roberto314/Unicomp2/various/JTAG Chain.pdf

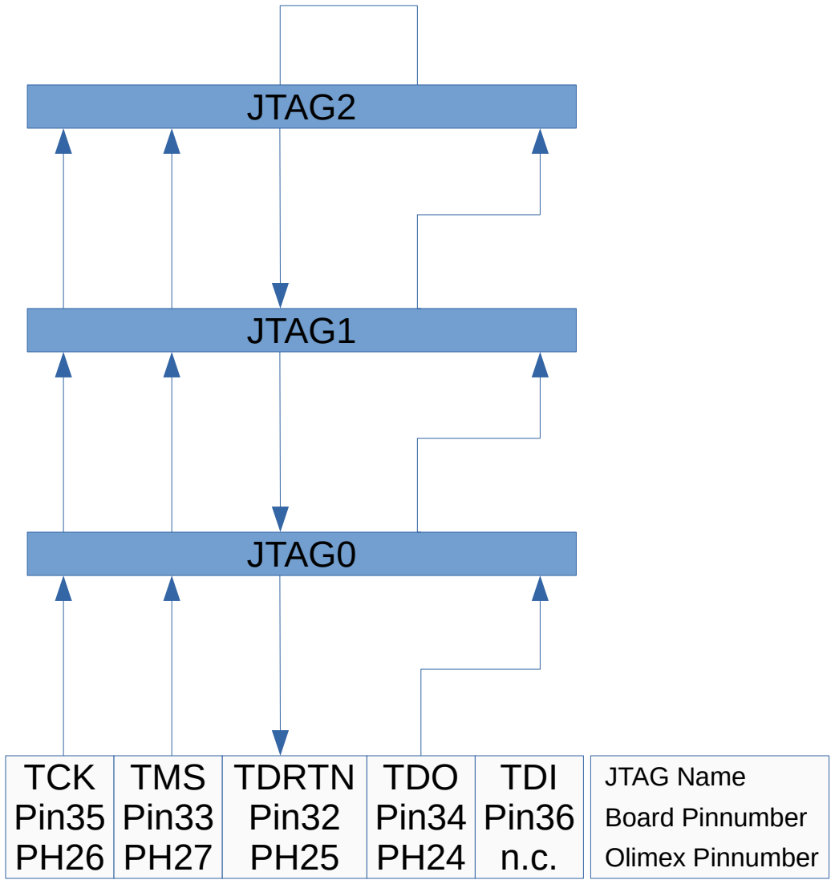
[picture p6: figure]
JTAG0; TCK Pin35 PH26; TMS Pin33 PH27; TDI Pin36 n.c.; TDO Pin34 PH24; TDRTN Pin32 PH25; JTAG1; JTAG2; JTAG Name Board Pinnumber Olimex Pinnumber

JTAG Chain and end connection
