roberto314/Unicomp2/computer/dream6800/Dream_Invaders/Dream_Invaders.pdf

### T EI FI EAM I TVVAtrTE FIEiI

COPYRIGHT 1980 | M.J. Bauer

Memory requ'irements :

Loading address:

Run address:

2K (0800)
0200 - 0700

0200 (Not C000)

Control s : Move gun-tumet LEFT: key 0, Move gun-turret RIGHT: key Lo
FIRE photon missile: key 3,
Game ends if | all four guns get zapped, or
an alien gets down to the bottom row (6th row).

Scoring:
10 points are scored for each alien exterminated. There are 24 aliens per round. Internal arithmetic is 8 bits, so maximum score is 250 x 10 = 2500, at which point the score (and ]evel of djfficulty) freezes; but you'1i never get to 2500 unless you're superhuman! Beyond 2500, the number of rounds played continues to be counted. The score is displayed after each completed round, and whenever the aliens score a turret hit. Also shown js the current round (on the left) and number of gun-turrets remaining.
Player gets a bonus of 2 new guns at the end of round 101

Mi scel I aneous :
Game speed increases as the game progresses; starting off fairly tame, but getting frantic towards round 8! The rate at whjch aliens tend to drop to a lower level also increases;, beware when one gets onto the 5th row! (Hint: Many events which appear to be random-are not, but in fact are more or less under the control of the player!)

The aliens also step up the number of missi'les they use, at round 3, and again at round 6. There are no shields, so you must rely on your skil1 at dodging and develop
a strategy to avoid being anihilated!
Game can be restarted by pressing any key (after 4 second delay).

Checks um:
A short Checksum Verify program is provided to check that your Invaders program 'loaded from tape without error. Key in and run this routine at 0700. It only takes a fraction of a second to run. Then use 'memory modify' to
examine location 00FF; jt should contain AA. If it does, there is a99.6% probabi'lity that your program loaded without emor.

DREAM INVADERS has been thoroughly debugged and tuned, and exhaustively tested (by eager Space invaders addicts) so as to ensure you many'long hours of enjoyment. If the program appears to be misbehaving on your systemo then either it did not load correctly (which can be checked, as above), or your

system has a hardware fault. Note: adjustment to the tape demoduiator trimpot may be necessary to effect a successful load.

(4, I or C) (5, 9 or D) (7, g or F)

(a)
(b)

## trl Ft EAM6sOO soFrvl/AFIE

CI{TCKSUM VERI FI ER
Titis litt1e program is used to check that d4ta in a given menory block (in chls case,0200 - 0700) has been correctly loaded. A1l it does js to add all the bytes together, without carry, and the B-bit result is stored in a certain RAM localion. namely 00FF. Thls result should be AA in the case of DREAM INVAIERS, trt i6
highly reconunended that you run rhe verifier after the firsL attempt at load'lng INVADERS. Note that the srarting address of the veri-fier is $0700 (not C000) ,
* CHECI{SUII VERIFY RBUTINEI (,7OC, | trRB | $0700
o70O CE O?OCI VI-RIFY I"DX | *$OzO{t
oloS 4F | CLR A
C'7O4 E6 {'O | VER1 LDA B X
0706 IB | AFA
a707 06 | INX
o70B 8C 0700 | CPX | *tO700
OTOB 2b F7 | BNE | VER1
Cr7ofr V7 Ff | STA A tlOoFF
o70F 7E C360 | JF1P *C360

LEVER AND PUSH-BUTTON CONTROLS
To avoid wear and tear on your keyboard, I recormend that you construcL a heavy-duty control-lever and fire-button assenbly on a lump of 4-by-21 The buttons are wired in parallel with key-switches (0), (1) and (3). They will not interf,ere with keypad operation because they are normally open. For ultra-reliabili-ty, you
could use rnicroswitehes.

A

V

ocK

Fm

W0 |DEN Et
l fBi-cFrFl

# Fre

eble
C HE,4 P
PUtH-gurroNt

NET|L ERAOKETS

WN'HE' PIVOT
( EMst)
CA N rNOL LEV ER 4 SSEfu TLY | ,tN PLu6. {2700)

2K RAM EXPANSION FOR TIJE DREAM-6800
Important Notes:
It is highly recomrnended to wire B x 10k pullup resistors from the data lines (00 - D7) to Vcc (+5V), on rhe DREAM board; (see diagram).

A 2.2k pullup resistor is required on R/W, as shornrn, since VMA is not used. REMOVE RAM CHIPS FROM TIIE DREAM BOARD; to be installed later in expander board..
Never remove or replace the e>cpander board with power appJ-ied.
GND and Vcc leads should be connected first on installation (before bus leads). Ground yourself and your work (via a lM resistor) to avoid static discharge damage. Construction Hints:
Fabricate the circuit on vero rDrp Boardf (No. zoo-21084E) or similar.
Use sockets for all ICs. Place O.luF ceramic bypass capaci-tors near the 2114s. Use two ribbon cables (4" to 6" long), terminated at each end with 16-pin DIL plugs ' to connect. the expander board to the DREAM board. These can be purchased already made up. The DIL plugs on the expander board end should be soldered in (i.e. not socketed) to ensure reliability and to save 2 sockets.

Take extra special precautions not to get Vcc and GND reversed! The use of a
polarized Z-pin plug and socket is highly recommended to avoid catastrophy.
Use fine hookup wire for interconnections on the expander board; 30 gauge 'Klmart wj-re-wrap wire is ideal. Cut wires about fu cn longer than the direct point-to- point distanee; youtll end up with a mess if they are too short or too long. Be eareful not to nick the wire when stripping insulation and avoid bending the wires at the joints too often. use solder sparingly; donrt make blobs!

The signat frE (rnemory Write Enable) is not available on the bus connectors, so it is necessary to sacrifice one that is. It so happens that IlQ is pretty useless,
so wer11 use pin-10 for FE. Cut the PCB track at pin L0 on the lower bus socket. wire a link from rc10 (74LSl0) pin-12(wT) ro rhe bus connecror pin-L0.

Testi ng
First, test your expanded system using tmemory modifyr. Try reading and writing a few locations at random. If the computer appears to be working at all, thatrs a very good sign! You should be able to deposit and exannine data from 0100 to 0800, but from 0800 to 2000 you should get 'FFt, indicating no RAIvI present.

If that works OK, you mi-ght like to try the memory check program in the CHIpOS manual, j.f you have one. This program can be improved to provi-de an audio bleep after each successful scan of the block under test; as foll-ows:-

O22C BD CzDF
022F 7E 0203
| JSR BLEEP JMP OVER
Note that DREAMBUG is required with the memory check" so that if a RAIvI fault occurs' a register dump will be displayed so you can figure out what went wrong!

Check the block starring at 0280, ending at 0800.
If you have a malfunction, carefully check over your wiring. With ICs removed, use a multimeter (on ohms x 1) to check for shorts and continuity. The RAM chips
can be tested in the DREAI'{ board, without the expander board connected.
Another useful test is to run the DREAIvI board (with its lK), with the expander board EMPTY (i:". all ICs, incl. 741s138, removed). If it doesnft work, you know for sure therers a wiring error somewhere!

Addendum:
The December '80 issue
Many of the above noLes

of E.A. contains details
will also be applicable

of a 4K RAM expander PCB design. to that, design.

6 F,lD
nlw

AOn(
frLA1 'A+

h5. ftb
h7
AS
A9
00

'at 4
D'A
93p9
9E
96n?
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
2.7.K

2K - +K RATh EXPAN9ION FOK THE DREAM - 58OO

2.7k

Iir (o+oo-oloo)

Resis+ors : 94W 5%
DioAes; 1Nt1*s or
7+ LS 1,38 | I,apacilors: pref. monolilhit (erami<,
nr.
log | 10 | 8 | 108

Vrc 6ND

;
A

:
:
0 t 1t+ L LL I
t----

D
FwE

Vcc 6Nt

;
:
A

211+

n

I
cs wE

V(c 6ilD

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
211+ D0--

Dr
DZ
D7

Vc< 6ND

;
:
A

4t'lL LLL I

[56 (oooo-o+oo)

vd< 6ND
ao
AOAt 4'
AZ
_q2 E
F43
E

L-..,*.--.-.,
Jj liEfrlw g0a8o | +5 Ct{} +12 -5'
,

id-A- o

-ol

| ------J
t,,*,,,-- JC3-
-,
| j.:-:;6::x: .ir,i., [fI r- I
| siil;i-.,i'; i ; I

### I",i,i'i

| | * I

tl

il
.rl

f

lm
1>< l"o{>32. iw

1oIt

;

I rrr
lL
I ltt l-lxI :-t

I
i
JY

## L{EErk'

(x ree )
I hot.tj

0
Ic5 | ICI+
H

trc6
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
## li ^t^^

I

<^>tl

ErDtrtolv5 T0 ,8Enm E0A8p
F06 Ex?nNstoN j gus socKETs
IIN' ?ALL.UP frESISTORS.

SU66ESTFD VENO LAYOUT i
8oT'r0M | ^ vrEW ! | r',\ V

L€AV€ frOON FOF FUTUEE
ExfnNstotv (e.9. p.r"A. ) .
cHEcK hllslN6 A6Att(5T ClRCotr !

6rp
0,Lr,P'
\76a o1 fi\e
6ND * (irH
Y" '.:Y;
iEEFr irr-,
vb .I*

## gg $EggHsEfi$EgaEaS$ $EgnEEgE $g$$3}$$$$3E $3

st*fr 8$rH gsil*f; fr $8R 8s s8H8S8S hHSSFilS*hSgf, H8 b 8HtflilHtafil3sSsf;$H8ftHsSSHEf;tHhfrh?HtHsHSflHf; co E F,F g gf t+ g!? h. gg €€ gJ s !.8 {! E l o sglr.{r rr, tr r(.r n. €rJ€x { rr o e a ir} rrr"t o o.(\ + s,{ EErs tr.O8j dtrsi [.J qt.{ 46{.j6f d,r AiUil dEdir. <i} 6t mn j stRh$3b*$ssi8s8s8H8bsst*8s8fHHk8Hs*sEil?s

## = e{t.g+gass€qNN${ o E0s roo,rjnr' dFdiric+8fl3t? ftn3Sflh8k$HSiHS*SSHSgt

S tagEES.Of{st! O€ rfr.O {

## :r a;dEEFrn{uooos'ot3U3B dSSnSgSSSSHtfr$fSH*fl?S

: RTbEEftT83HH3E8$tSEhEfiHSIgSKfKF*STSHEilRHf;
'F qg { h f t{qtP g g{-) g{ h r,.r I?a g g g FrF.q e € \ t €r.\ { tf rrr{ Nt.o br . r{ o :, {$ e r.rN s {rr E ou e{ NN E <x o 6 tr i6itft6 db ii Iii { of d Lj n,J tFl G i

## g 8HHhfi3*atH8S83iF8f;U88$8R:5fft8ilEftfrH38fl8H8

o H I s l'-l € t I € Q F t'.. { f r\ $ F LJ o H n { q gJ s E :r g u a g s tr | g} < !{ rr} s o. r.r o { o s < id m o 6 < E $ < {J 6 o q F.t l^t u fi d t\ ii m G Ci A E fi rq d ct fi O 6 5 Fr r. r'.

## th ft +*ft Ef, H8t$ sg 8H8 3ilrS*ff h8fr H85ft Sil8838Ufl H8

8 k h *8 fr t fr g f S E H * H 5d E E * h H b f HS I H8 3 H s S H I k b i9 R e

## Rgefi8s8H 3fr ES*i8+ilSSft 8H8drf; s8h*Eh88hF 88S8

8S$ES Hrts$ilRhh* SSh E 88S88rf8 SRlHSdEsFsk$fl f,
I g f* \ lg € !& I -t F E q A q tr { * $ l.f F { td g g $ { € O tfi t\ id r g r,. { { r\ u $ trl c.i o s < cr e.t tr rd <> e O o cr u rn -r $t -{ u ii 6 E fi d ; {,1 d ; t ii E ti 6 fr f, d it E - [

## tsdtsEstH?f, 3s* E$s sf;s8ffsgHrH8*ttH*$rili8fl il

il 8h lt $8 8h3 S 83 k 8r R8b 8S8 r hF t 8E 6 *8 tLiE 8FR f; 3t d

## s*3 8EE EbBSSSEh$ft 838:kf 33EB**h$*S8f; s8S3Hfr

I q g E I E x :r I E U !l el $ |o c' o. a H A € E O g tJ -r x € ct 8\ o. O { q c0 € o € { .{t
u <t (8 c| $ o (} o E] u co fl o o o € F{ s u c o ft t'. a s o o. o. ; Ft fiJ di o o r < 6 LI 6 6
o r,. u a r\ !q .8 g o r! !q o Ll gl E t\ trt o o + s N td *t o .o < f\ o fit rA o N rr c0 N Ll (t) .o 6 O e LJ E u} tl,l C* f'{ (J E O -t (J C.l O e 6 < ; c0 8,,t Cv li < 6 4 f n Fi fl { O t\| { + iF r\ {t d tr u (o ry I { l! irl Ll E 4 o -r S Q -r o r x cl r o t lrl { u s tq { |f} € \ Ll n {} € !t N El cf {} € -r o o O 3E O $ N S (} Ll O O < €} i S 6 + € O -{ f N fi O S { f.t g. \ { $ -r {l () lE E O cO { g lr. F $ t al Ol E f\ tO O € € .0 € O u) + +r -t € O o. -{ N trl .o tr. tr. LJ -r N & @ l& O -t (J o o a x !Qs ta c8 E r]l <Ef,{ tr. < 6 { f{ o o * € Lr c.t o o bJ (\ gi d fl} tr fi o { N o N 6 trt x
O E$ {! Fl g -r Ll\ q to { $ f{ A O { }\ € tf a0 P'rr. r\ { NN lr. O. € { {-t lr. €.0 tl NN S o !E x t]e lr.'JG nq :f u- m <L! N s trt 6 d < rrr * € rr ir< 6 u ct o h r d 6 o r,. 6d 6 { ij d', x I O I O I {l Clr € I\ lL { tL € lrl.O b 6 -rn E -t O O A -t € rr. U tJ E { $ A trt -t l,r. E Fl { o (J o t\| r|{ 0F E t t& o. !f ul t= N fl o rR L,t o. o\ € g { o E E0 fi |o (rt (q rI < ql E s ql i& E o
O Ll tr LL '.) € tJ € -{ € lL O O rr { E ct { O € Ll { O € U tf t O .o € € tt} € o' u) r\ O .{t m t\ r l\ E \ t s g* s o f1'| tl. s o fi U) o. t A o $' t s, o s. h ..8 { -r o c! o { o tfJ o o.. t c o ft O Q q.D L, trl'{I Fl .{l € < € l& t! {t m O g { u o. E0 C € fit O .o { O cl {f E r\ S trl € o d o € E
Ct <E E .{] cg s (} -r t\| rfi !O If $l O $ O cO < O $! <C O { t'" I U b A E rln Q r N O tJ Ll O < fJ d
trt n N E tt < E trl tlt tJ A O tf { € t/. .o E Go (\| € lL t\| lrt O { t\ l'} .a n O. q !f g rD < { N < O u {}. o € o u cB 4 o lr. E0 LJ a u o r\ 6 S O u s x r E o $' |lt E < { o *r { (1 < @ N b, o. 6 0 I F { t. Fl |n n { I I o € x e{ r E o o x o 0. i.l x L { s e,t N o o. € -{ E € € o o { < O'3 E { $'i'3 trt c,r s f.l o O o m s ft N + 6 rrt o rrj trl { N o o o tr,'5 o (s g" ld 6 + 6 o 6 ri { { q b S g g I CJ < lrl bf E H} Ll O \t € Ll Q -r < ttl { x O {f € u { N f c) € 0. O €l € Q -r o s < $.aE t\| r\ri ct Lru to ':} El l{ tl|{ trlo. < { It o € ltrq 4 tf N $t {o e.{ fil qf € {Q t&
x { I u'^{ \ u tr {! -{ I s O € t\ { -t o trt € \ o r\ ct € o o g. fit u o r\ .{t o s cl tf o. ti |n € lr. o -l a8'3 E s iE O O(t, O {J.0 N g* S S{}tS O &E (} Lt -r O Q|gl -r o.{ $'i.']1+ { fl} L{ ci
N n L. { € { { { € -t N € x -r € { m lrt O O I O 4 O Cl Cl € n. Ll € O fl {0 O trl x -0 r !O E (J O l\ tB < t1'| S tt* II. .3 O lr. < { O n & rf O $ -l x Q O E S $l (} F ,} e {} 6 O 4 -r o.' iJI O E g g O { € -r r} E '| S. bf € L. O tr m .o N U| lL {l € fr N -r rr O € fi E tdl ttt O Lt -{ -{ E .A Cl .\ tr| S 6 { & O L S E {} \ r\| h () A m 6 g N d tf <t O <t < .8 -r o E tr E {i O 6 € < o e* lii .s
ooqoQoooQ oQGoooooooooooo | ooooooooo | oooo000 o -r t\{ rrl tr $} .o r\ t8 o. <E rtr u {f ..d lr. o -r e{ m lf tr, € r\ fr s s H H H H h * -{ N fi tf n s r\ SS8888SS8SES888888888883ooooooooS SSt SSES

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
