roberto314/Unicomp2/6502_6802 Board v2/MC6800_MEMR_and_MEMW.png

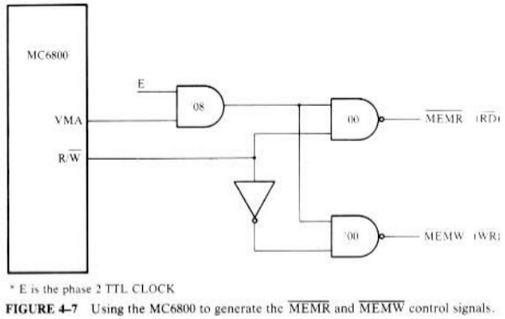
6502_6802 Board v2/MC6800_MEMR_and_MEMW.png
