roberto314/Unicomp2/computer/psion1/p1brochure.jpg

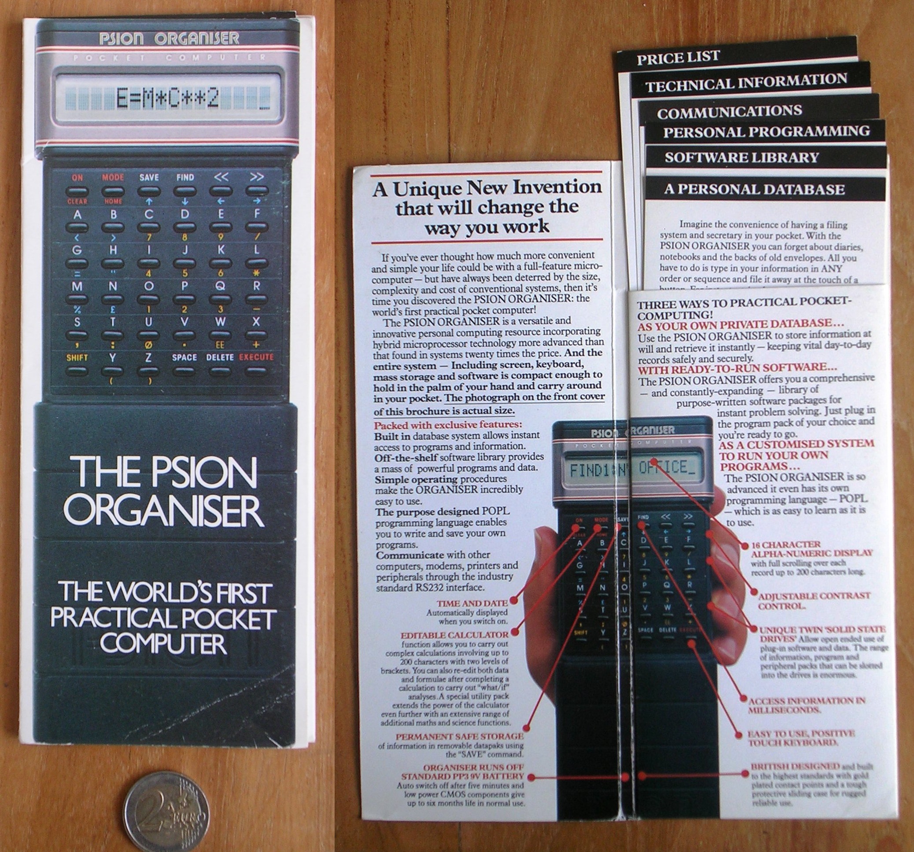
computer/psion1/p1brochure.jpg
