roberto314/Unicomp2/CPLD_board/ebay-board-EPM240.jpg

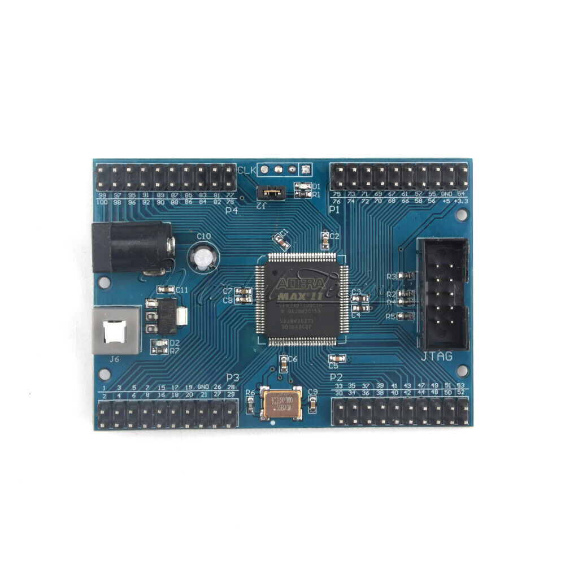
CPLD_board/ebay-board-EPM240.jpg
