roberto314/Unicomp2/Synertek KTM2/UC2_synertek_KTM2/UC2_synertek_KTM2.ods

Id | Designator | Footprint | Quantity | Designation | Supplier and ref
20 | U1 | TQFP-44_10x10mm_P0.8mm | 1 | XC9572VQ44
9 | U9,U3 | DIP-20_W7.62mm_LongPads | 2 | 74LS245
11 | U7,U10 | DIP-16_W7.62mm_LongPads | 2 | 74LS166
12 | U8,U12 | DIP-28_W15.24mm_LongPads | 2 | 27C64
18 | U2 | DIP-14_W7.62mm_LongPads | 1 | 74LS05
15 | U11,U6 | DIP-24_W15.24mm_LongPads | 2 | 6116
1 | U4 | SO-20_5.3x12.6mm_P1.27mm | 1 | 74ABT245
 |  | Sockets and Headers
2 | J8,J5 | PinHeader_1x09_P2.54mm_Vertical | 2 | Conn_01x09
3 | J1,J4,J2,J3 | PinSocket_2x20_P2.54mm_Vertical | 4 | BUS
14 | J6,J7 | PinHeader_1x08_P2.54mm_Vertical | 2 | Conn_01x08
19 | J9 | PinHeader_1x01_P2.54mm_Vertical | 1 | Conn_01x01
13 | J20 | RCA-Jack | 1 | Video
 |  | R and C and Q
4 | C5,C4,C6,C10,C1,C11,C2,C7,C3,C8,C9 | C_1206_3216Metric | 11 | 100n
5 | Q1 | TO-92_Inline | 1 | BC337
7 | R6,R1,R8 | R_1206_3216Metric_Pad1.30x1.75mm_HandSolder | 3 | 1k
8 | R17 | R_1206_3216Metric_Pad1.30x1.75mm_HandSolder | 1 | 150E
21 | R19 | R_1206_3216Metric_Pad1.30x1.75mm_HandSolder | 1 | 75E
22 | R18 | R_1206_3216Metric_Pad1.30x1.75mm_HandSolder | 1 | 680E
17 | R20,R3,R2 | R_1206_3216Metric_Pad1.30x1.75mm_HandSolder | 3 | 200E
6 | LS1 | MagneticBuzzer_Kingstate_KCG0601 | 1 | Speaker
