roberto314/Unicomp2/MultiParallel v2/schematic/MOS_MultiParallel_2/pdf/MOS_MultiParallel_2.pdf

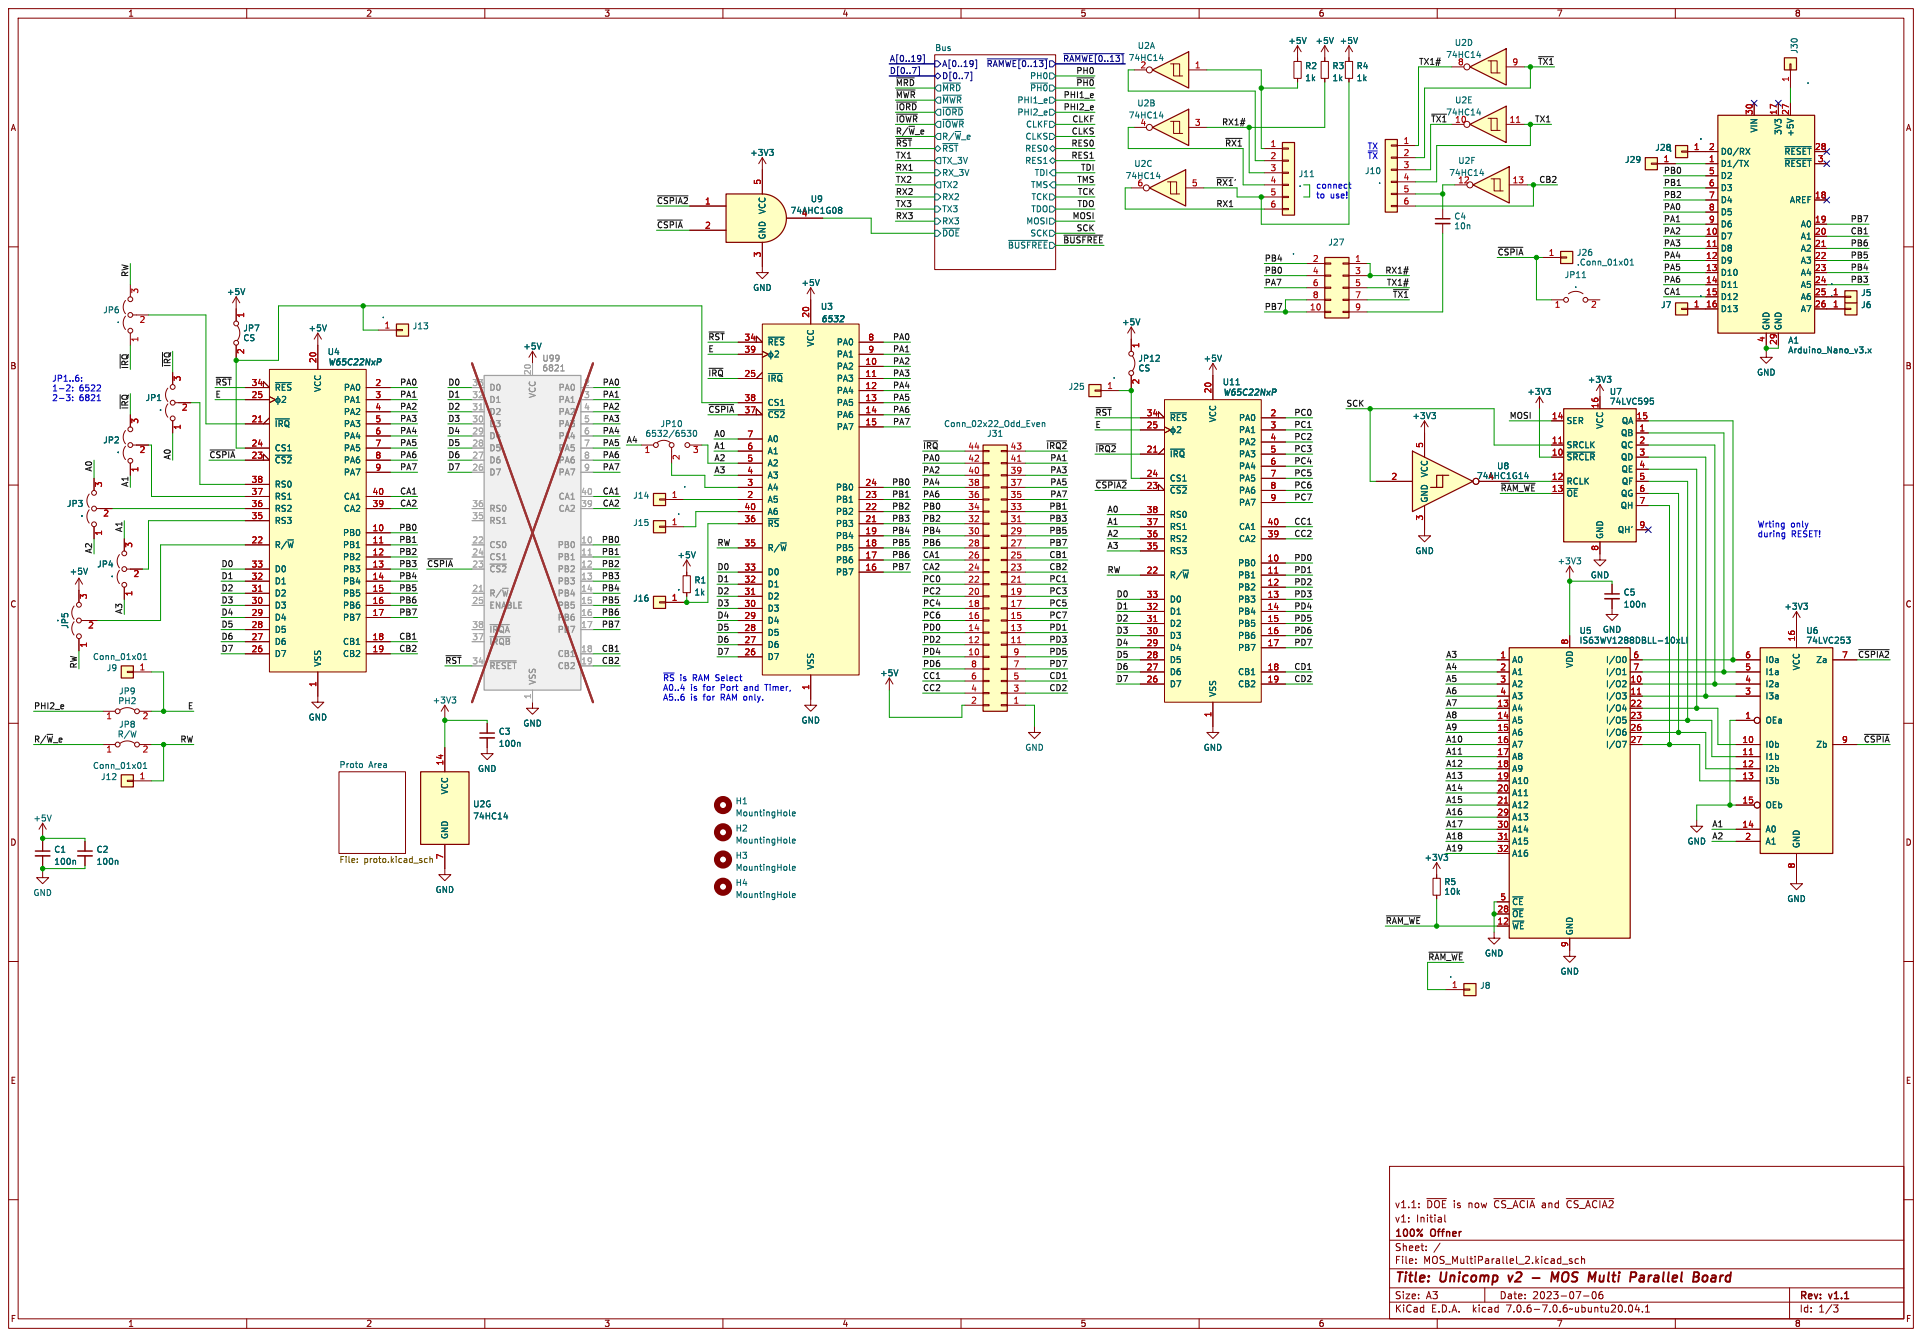
[picture p31: page 1]

1 PA2 10 PA3 11 PA4 12 PA5 13 PA6 14 PA7 15 PB7 16 PB6 17 PB5 18 PB4 19 A5 2 VCC 20 PB3 21 PB2 22 PB1 23 PB0 24 ~{IRQ} 25 D7 26 D6 27 D5 28 D4 29 A4 3 D3 30 D2 31 D1 32 D0 33 ~{RES} 34 R/~{W} 35 ~{RS} 36 ~{CS2} 37 CS1 38

7 GND GND GND GND

Proto Area File: proto.kicad_sch

Id: 1/3 Title: Unicomp v2 - MOS Multi Parallel Board

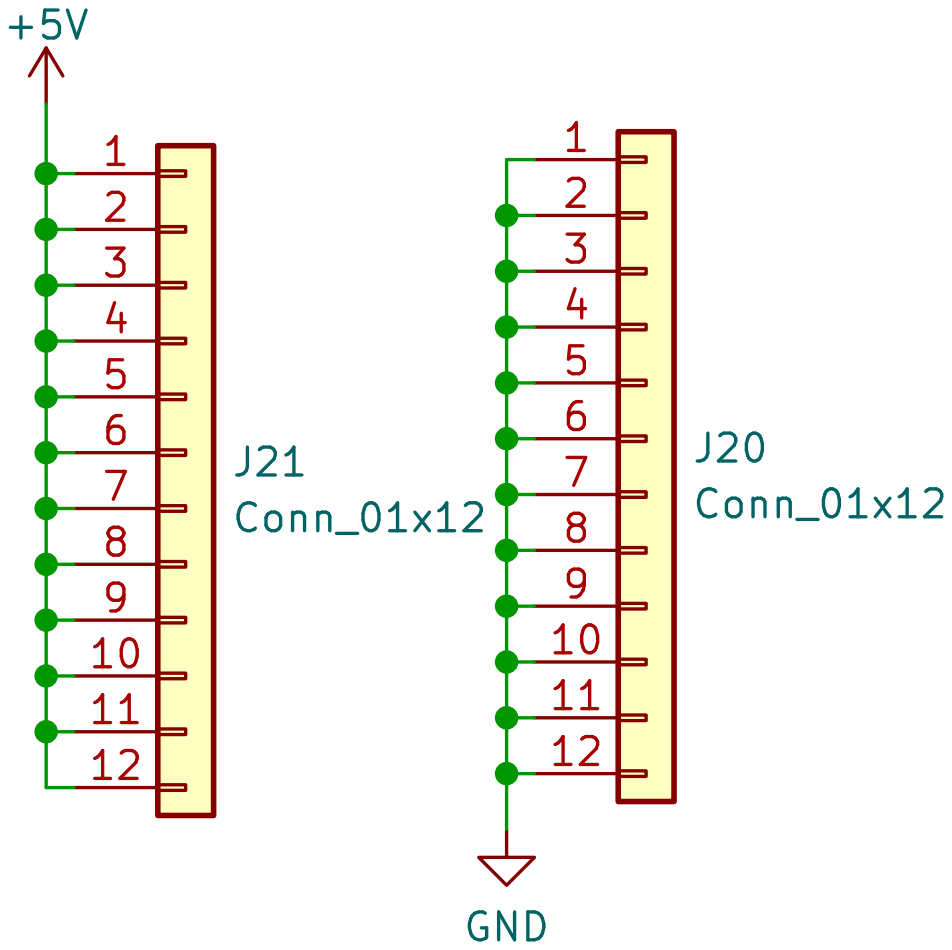
[picture p32: page 2]

Id: 2/3 Title: Unicomp v2 - MOS Multi Parallel Board

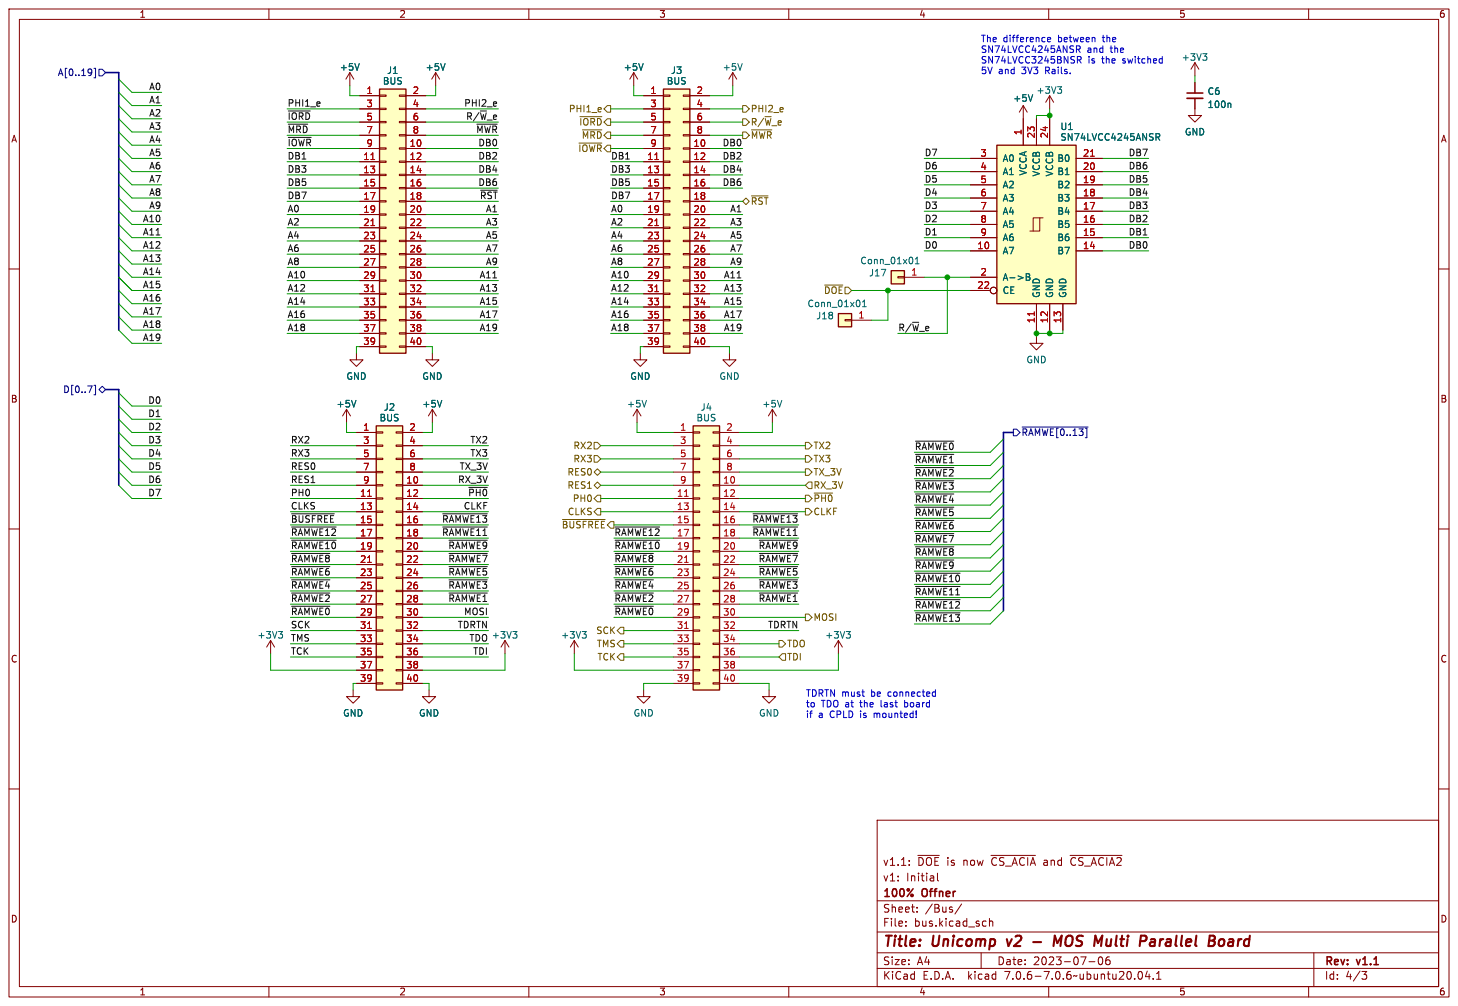
[picture p33: page 3]

1 A7 10 GND 11 GND 12 GND 13 B7 14 B6 15 B5 16 B4 17 B3 18 B2 19 A->B 2 B1 20 B0 21 CE 22 VCCB 23 VCCB 24 A0 3 A1 4 A2 5 A3 6 A4 7 A5 8 A6 9 +5V GND

1 A7 10 GND 11 GND 12 GND 13 B7 14 B6 15 B5 16 B4 17 B3 18 B2 19 A->B 2 B1 20 B0 21 CE 22 VCCB 23 VCCB 24 A0 3 A1 4 A2 5 A3 6 A4 7 A5 8 A6 9 U1SN74LVCC4245ANSR GND

TDRTN must be connected
to TDO at the last board
if a CPLD is mounted!

Id: 4/3 Title: Unicomp v2 - MOS Multi Parallel Board
