roberto314/Unicomp2/MultiSerial v2/schematic/MOS MultiSerial_ram/pdf/MOS MultiSerial_ram.pdf

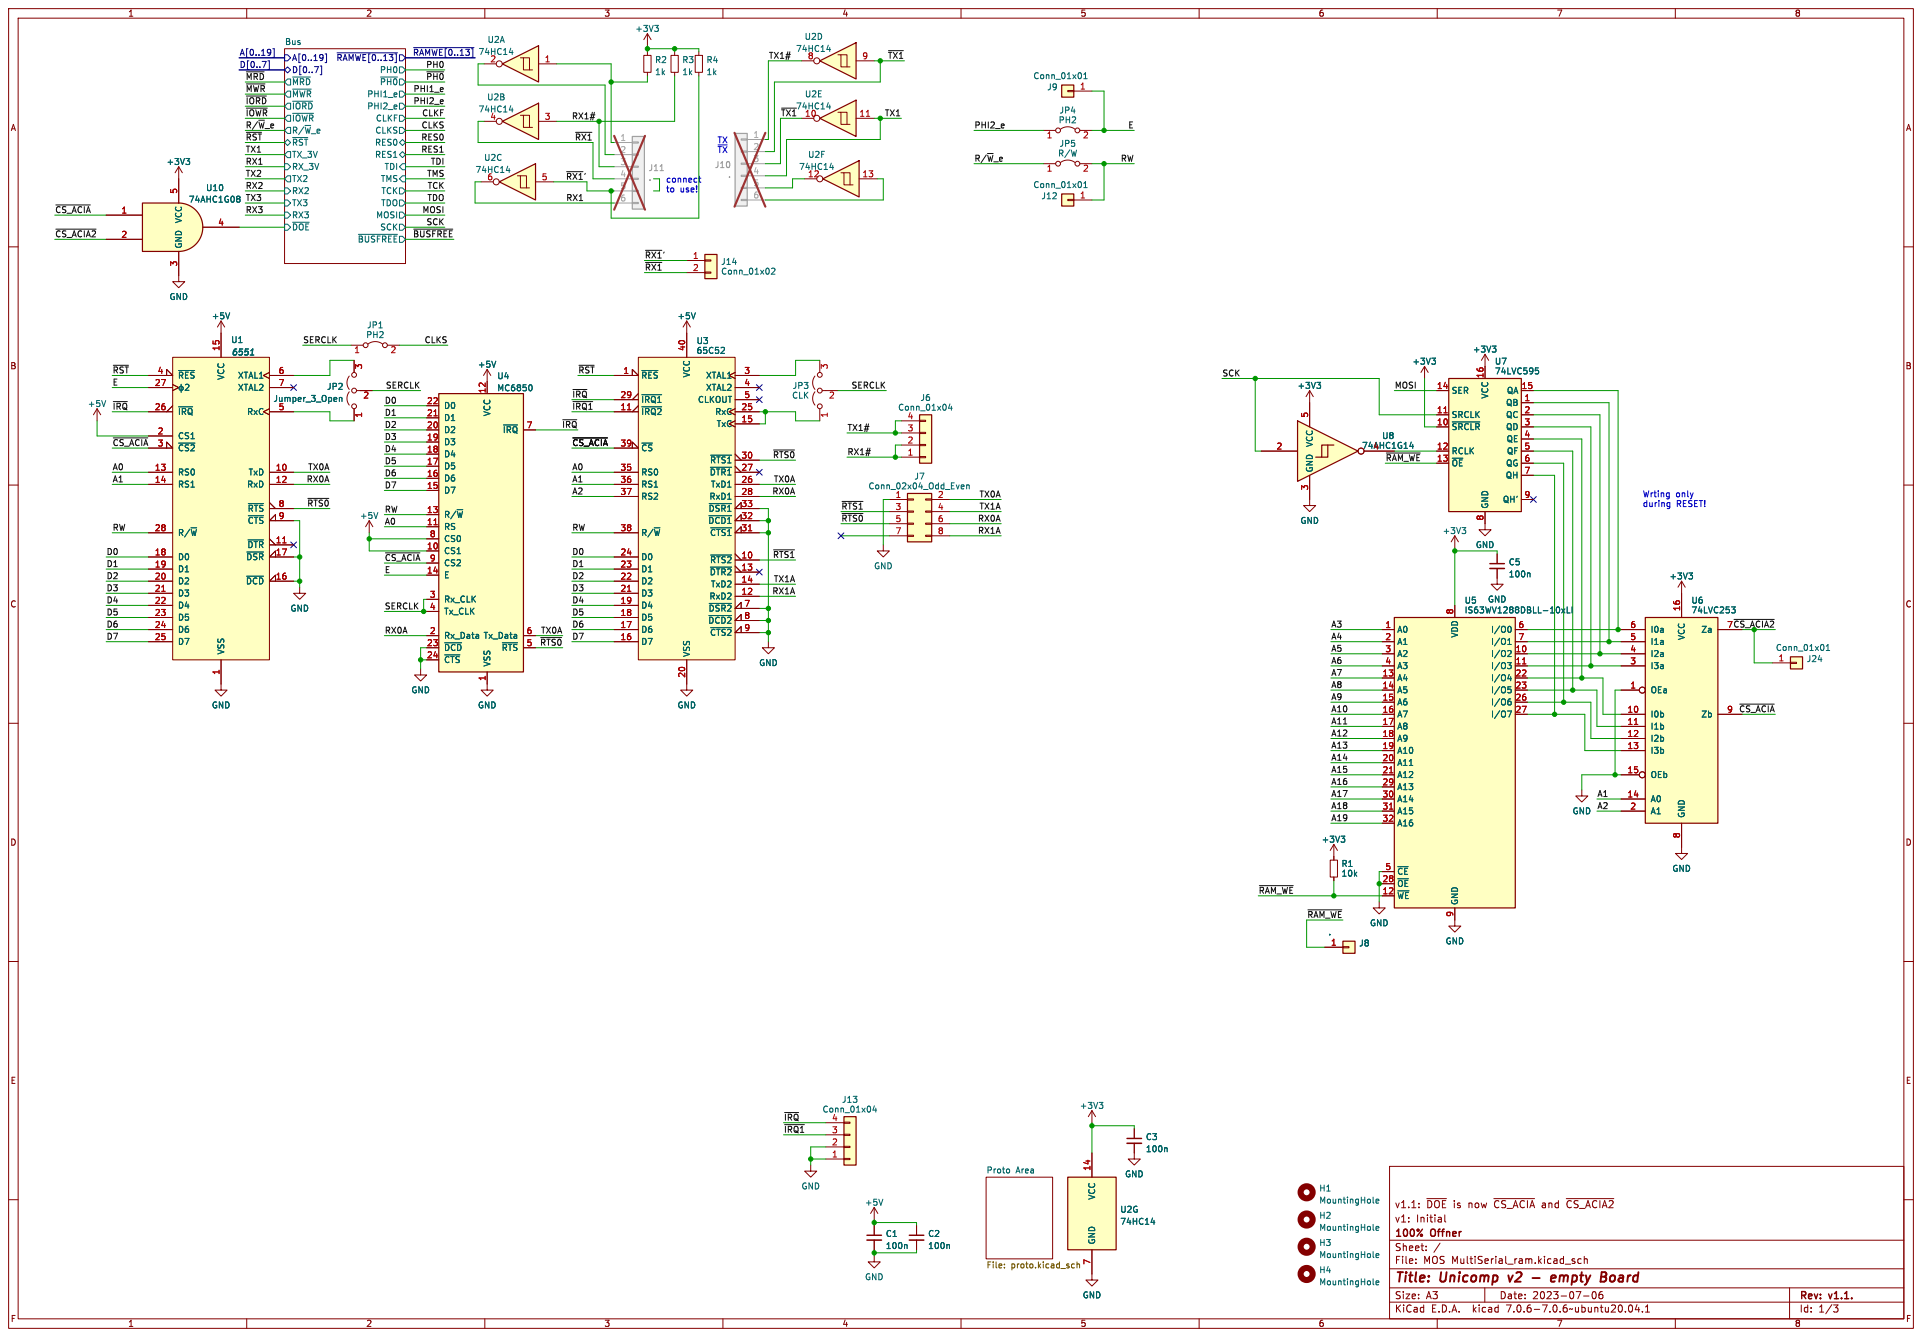
[picture p34: page 1]

1 TxD 10 ~{DTR}11 RxD 12 RS0 13 RS1 14 VCC 15

Id: 1/3 Title: Unicomp v2 - empty Board

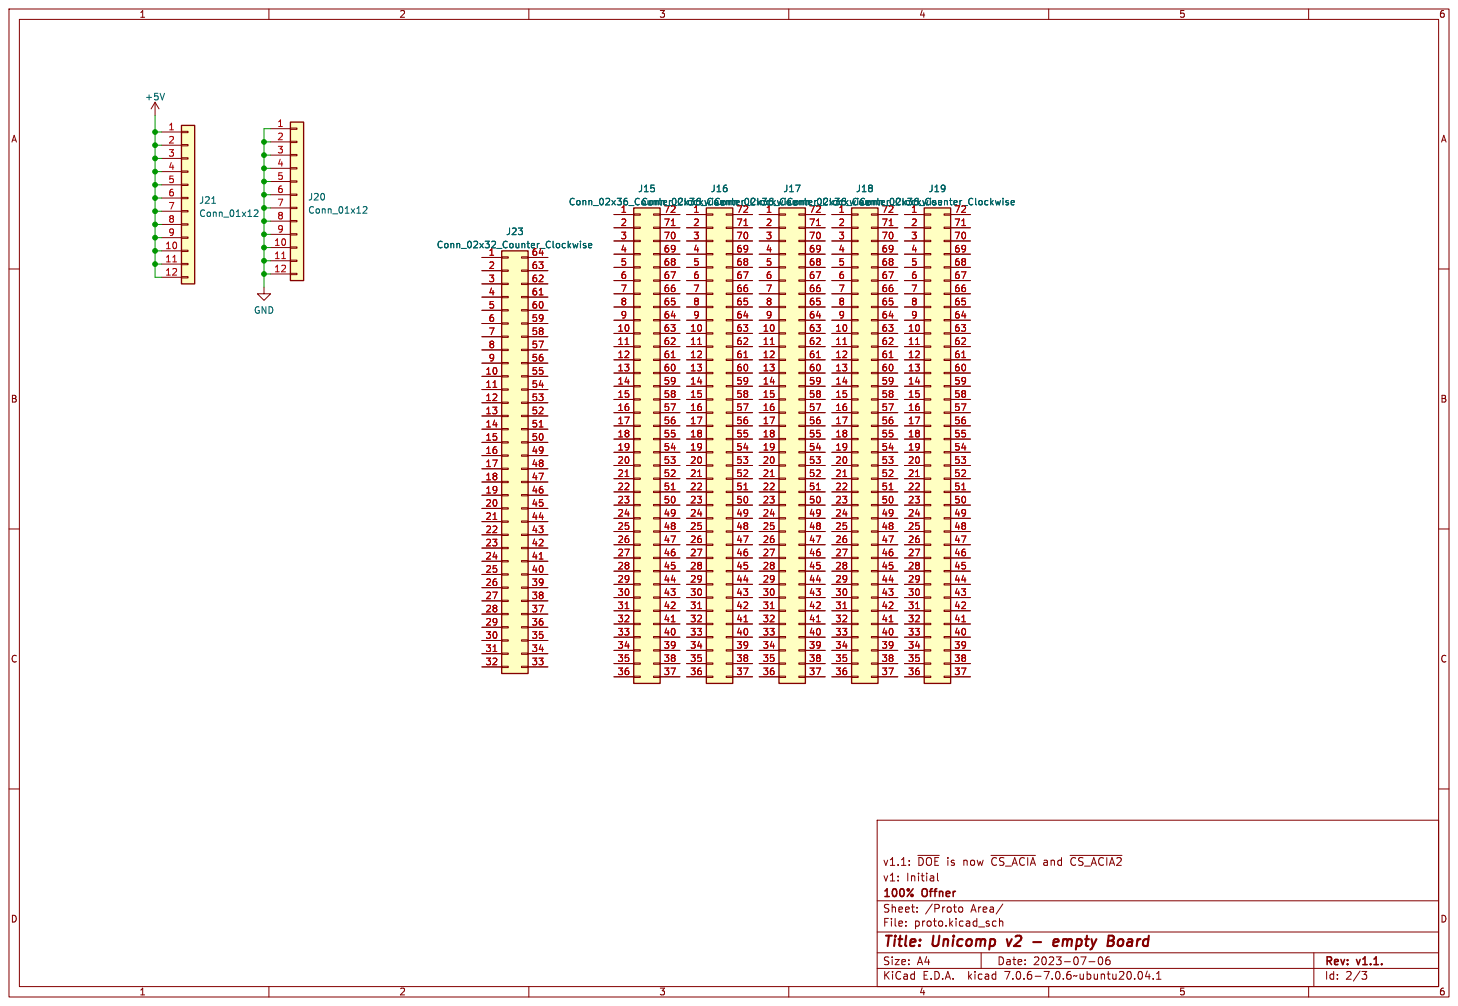
[picture p35: page 2]

Id: 2/3 Title: Unicomp v2 - empty Board

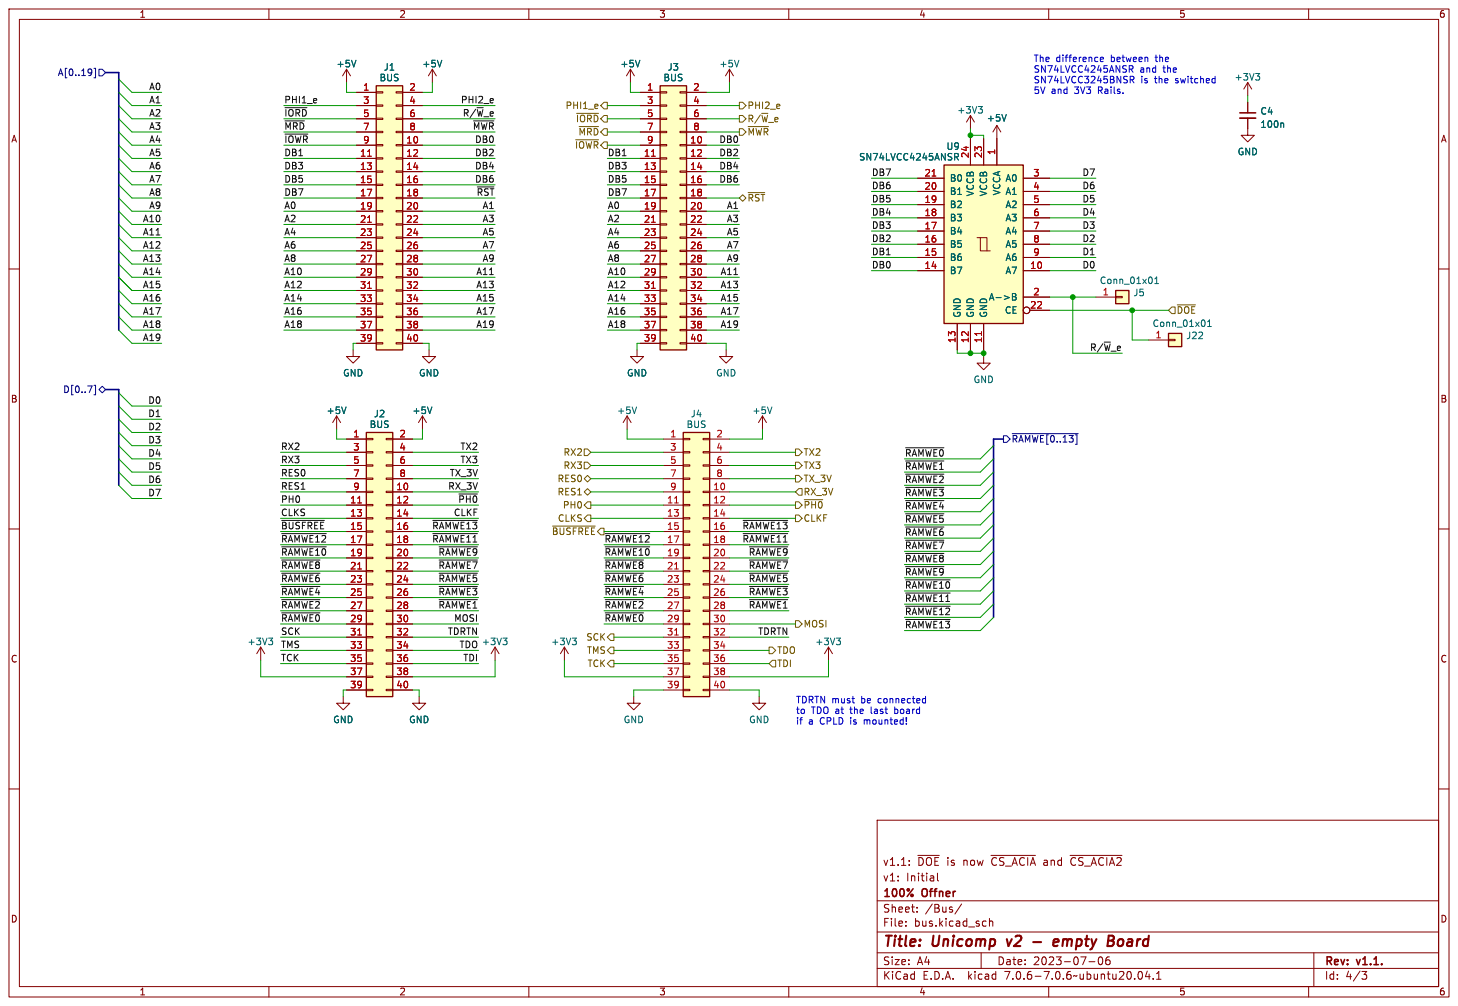
[picture p36: page 3]

1 A7 10 GND 11 GND 12 GND 13 B7 14 B6 15 B5 16 B4 17 B3 18 B2 19 A->B 2 B1 20 B0 21 CE 22 VCCB 23 VCCB 24 A0 3 A1 4 A2 5 A3 6 A4 7 A5 8 A6 9 +5V C4

1 A7 10 GND 11 GND 12 GND 13 B7 14 B6 15 B5 16 B4 17 B3 18 B2 19 A->B 2 B1 20 B0 21 CE 22 VCCB 23 VCCB 24 A0 3 A1 4 A2 5 A3 6 A4 7 A5 8 A6 9 U9 SN74LVCC4245ANSR GND

to TDO at the last board
if a CPLD is mounted!

Id: 4/3 Title: Unicomp v2 - empty Board
