roberto314/Unicomp2/olimex_board/A20-OLINUXINO-MICRO-EMMC_Rev_J.pdf

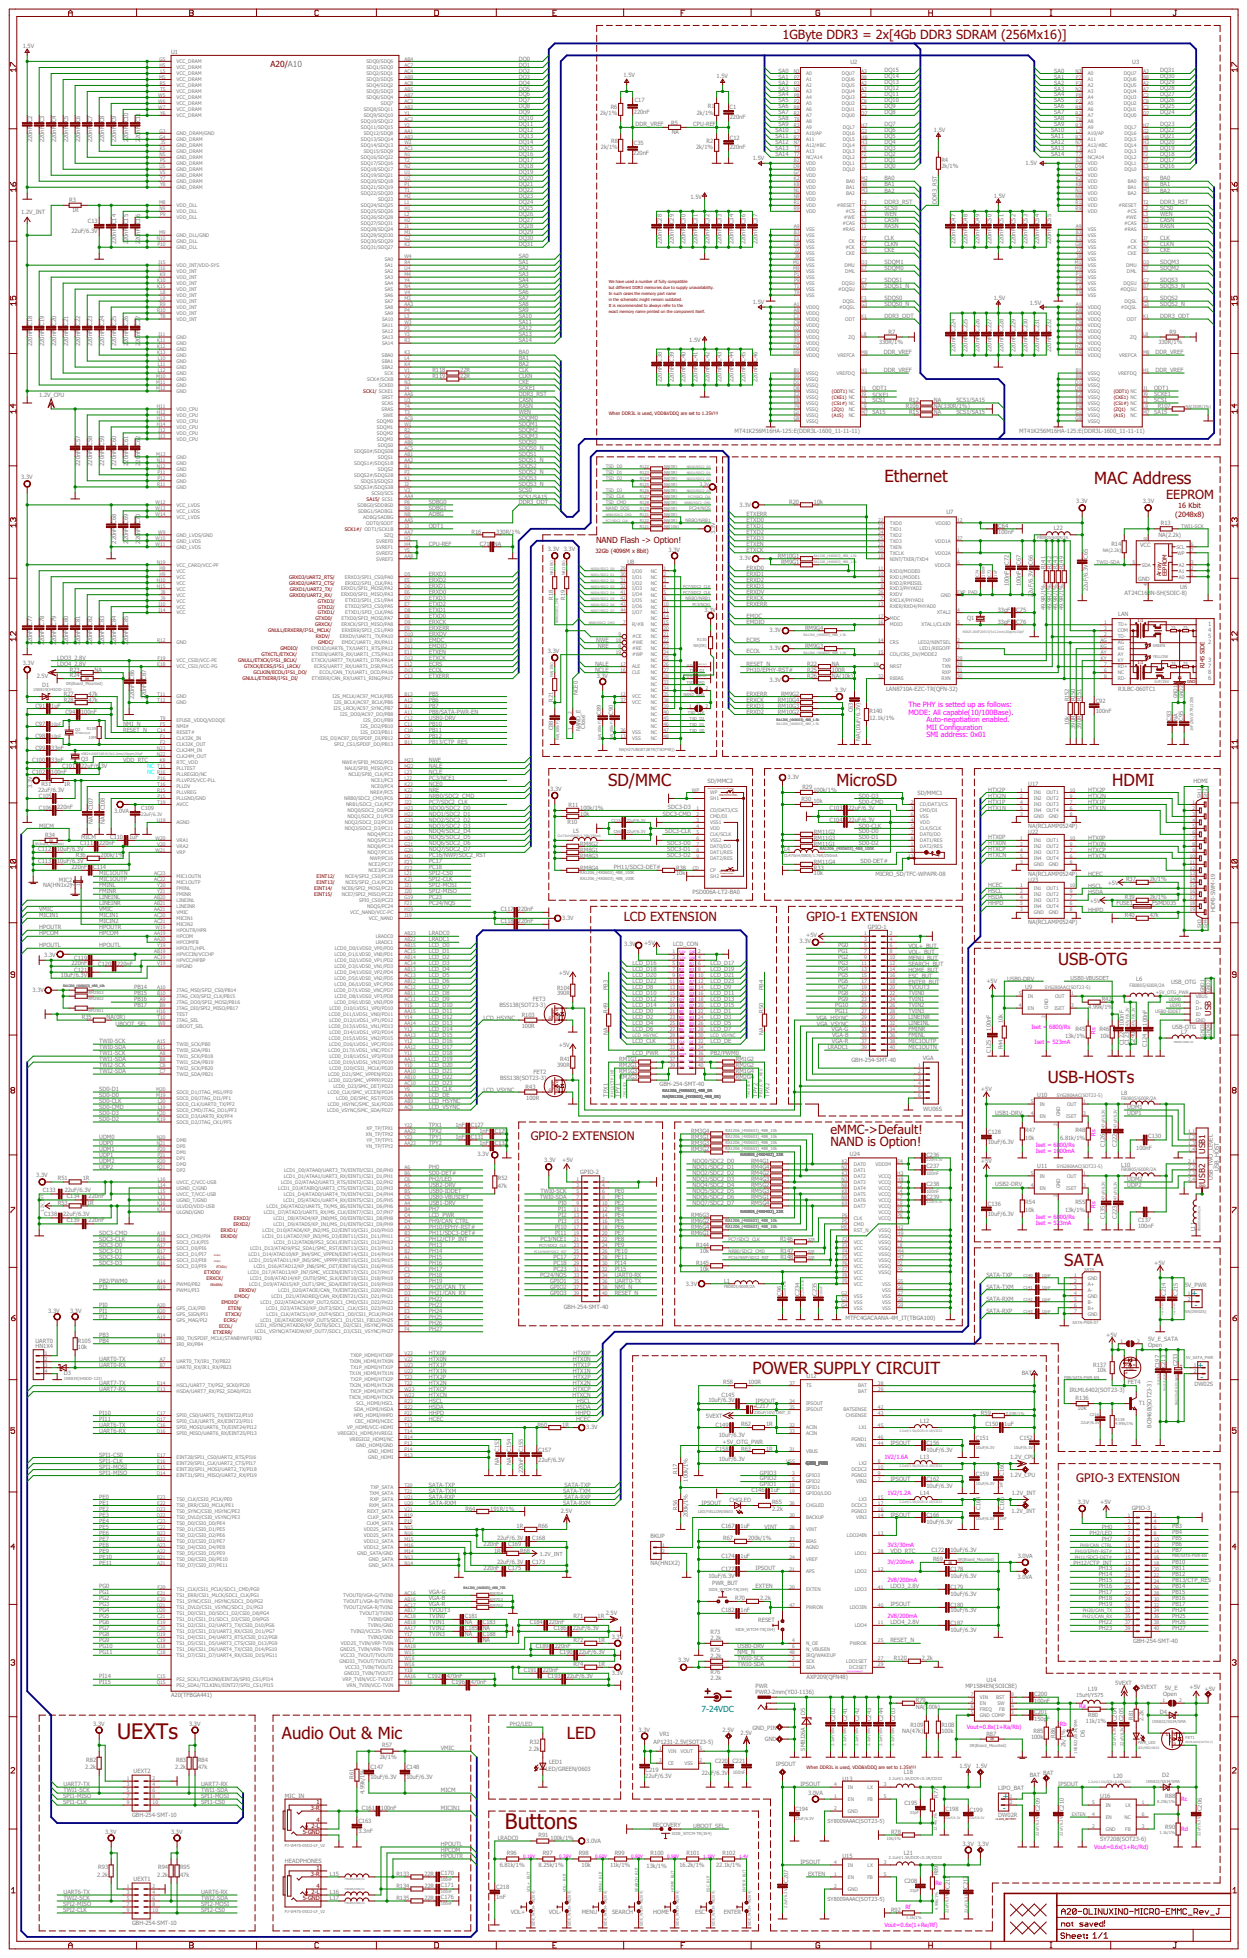
[picture p37: page 1]

We have used a number of fully compatible but different DDR3 memories due to supply unavailability. In such cases the memory part name

in the schematic might remain outdated. It is recommended to always refer to the

exact memory name printed on the component itself.

When DDR3L is used, VDD&VDDQ are set to 1.35V!!!

GRXD3/UART2_RTS/ GRXD2/UART2_CTS/ GRXD1/UART2_TX/ GRXD0/UART2_RX/ GTXD3/ GTXD2/ GTXD1/ GTXD0/ GRXCK/ GNULL/ERXERR/I²S1_MCLK/ RXDV/ GMDC/ GMDIO/ GTXCTL/ETXCK/ GNULL/ETXCK/I²S1_BCLK/ GTXCK/ECRS/I²S1_LRCK/ GCLKIN/ECOL/I²S1_DO/ GNULL/ETXERR/I²S1_DI/

eMMC->Default! NAND is Option! GPIO-2 EXTENSION
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
