roberto314/Unicomp2/RAMROM_512k_board/pdf/RAMROM_512k_board.pdf

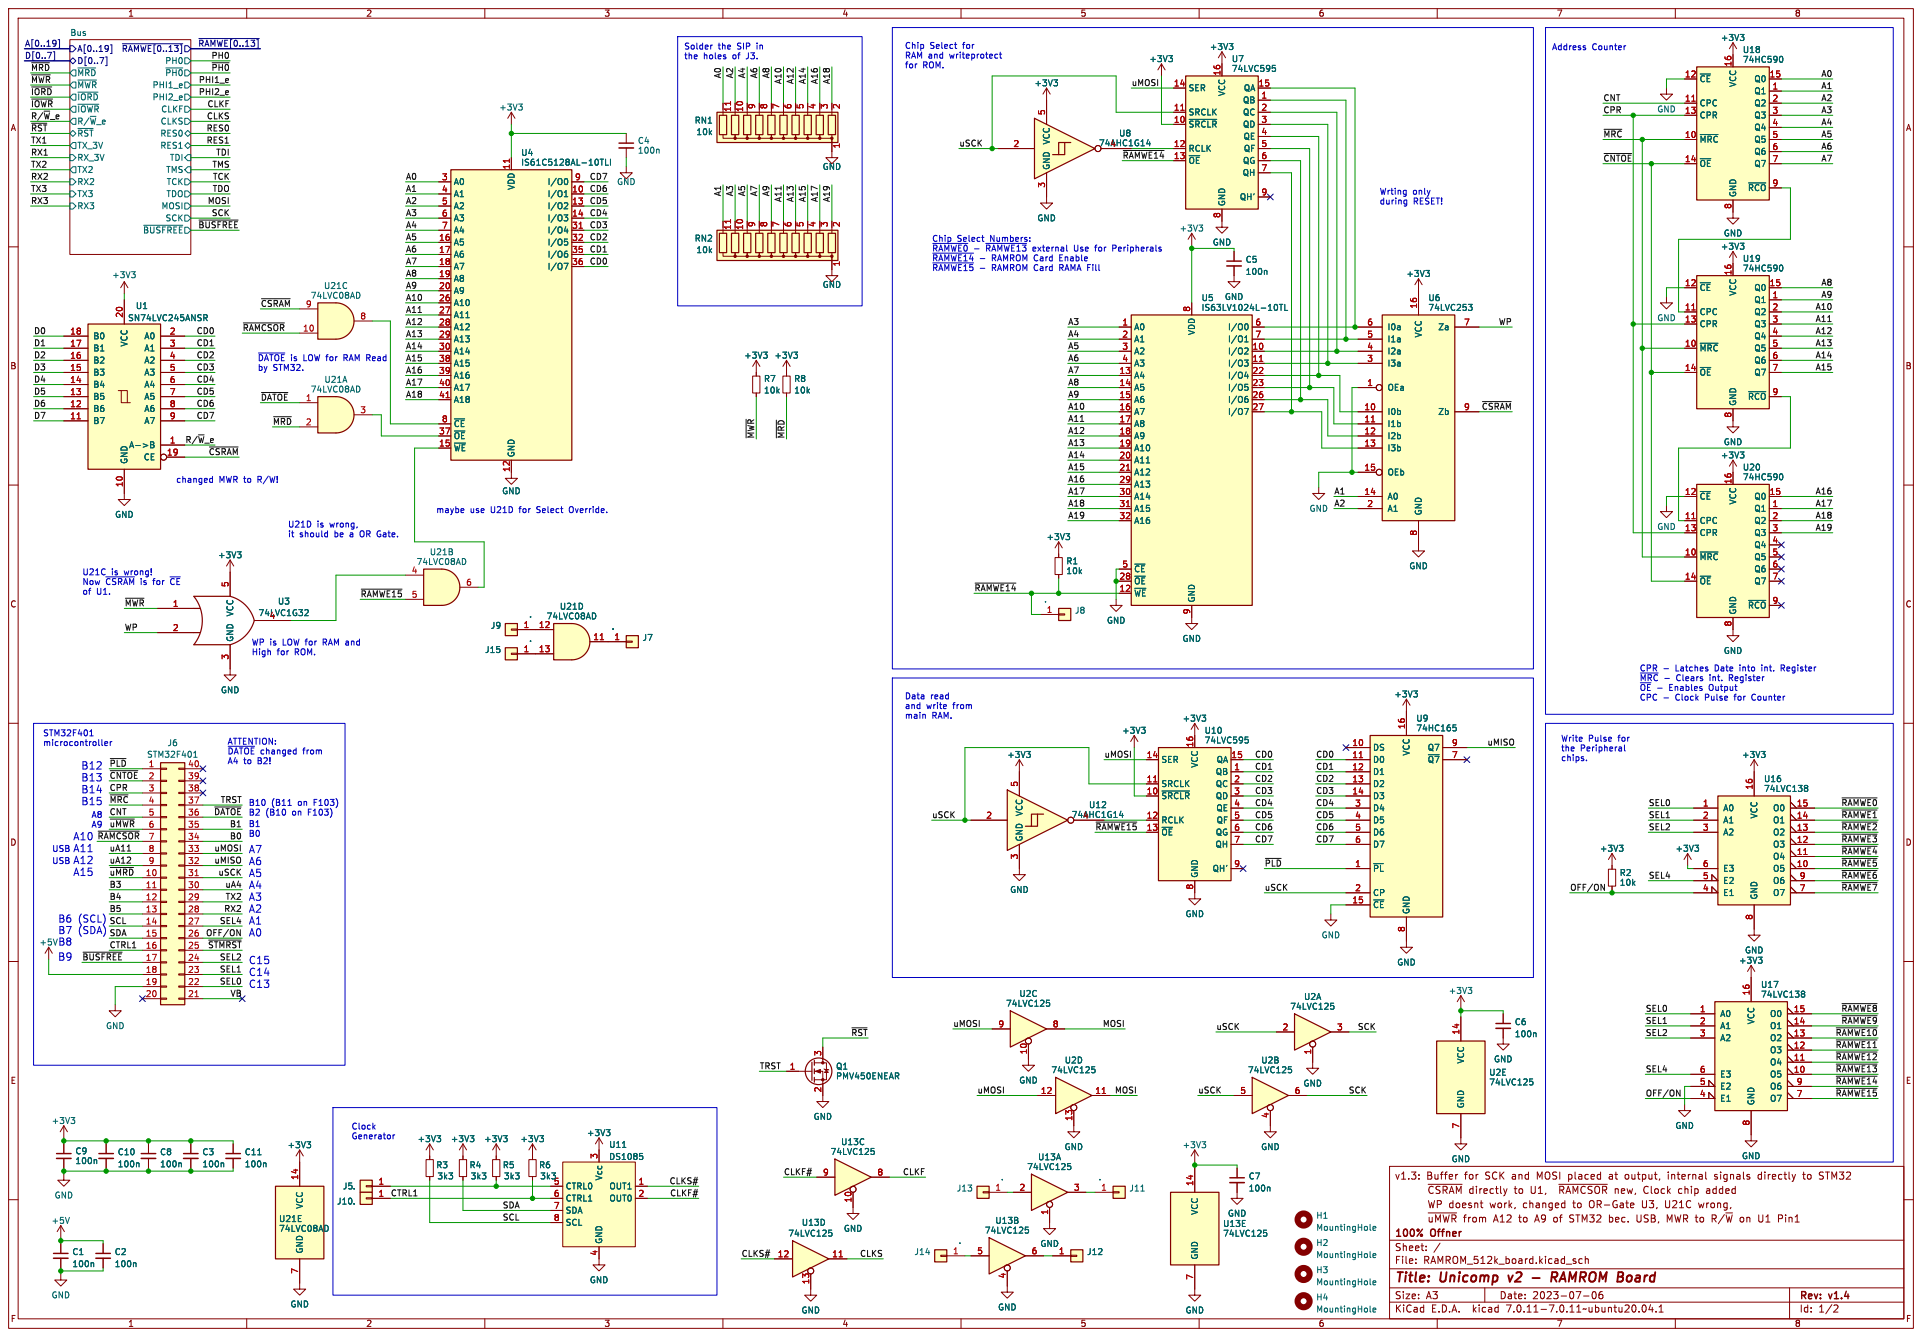
[picture p38: page 1]

Solder the SIP in

~{RAMWE14}- RAMROM Card Enable ~{RAMWE15}- RAMROM Card RAMA Fill B10 (B11 on F103) B2 (B10 on F103)

changed MWR to R/W! ~{DATOE}is LOW for RAM Read

A4 to B2! U21C is wrong! Now ~{CSRAM}is for ~{CE} of U1. USB

~{MRC}- Clears int. Register
~{OE}- Enables Output CPC - Clock Pulse for Counter

main RAM. ATTENTION: ~{DATOE}changed from

Id: 1/2 Title: Unicomp v2 - RAMROM Board

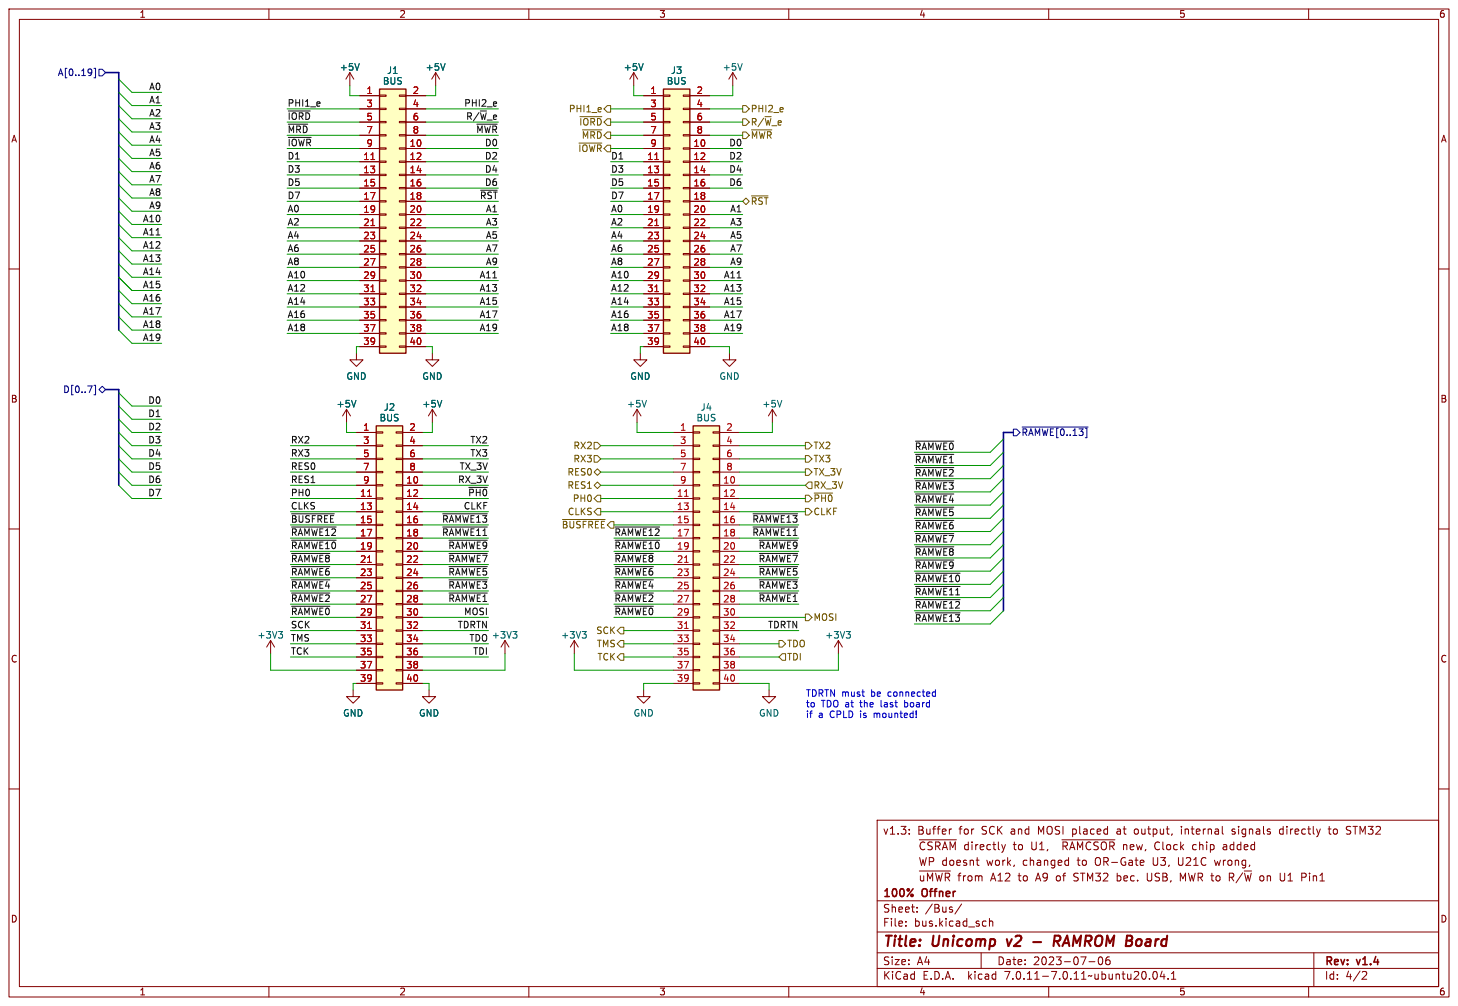
[picture p39: page 2]

to TDO at the last board

Id: 4/2 Title: Unicomp v2 - RAMROM Board
