roberto314/Unicomp2/computer/dream6800/DREAM_mini.pdf

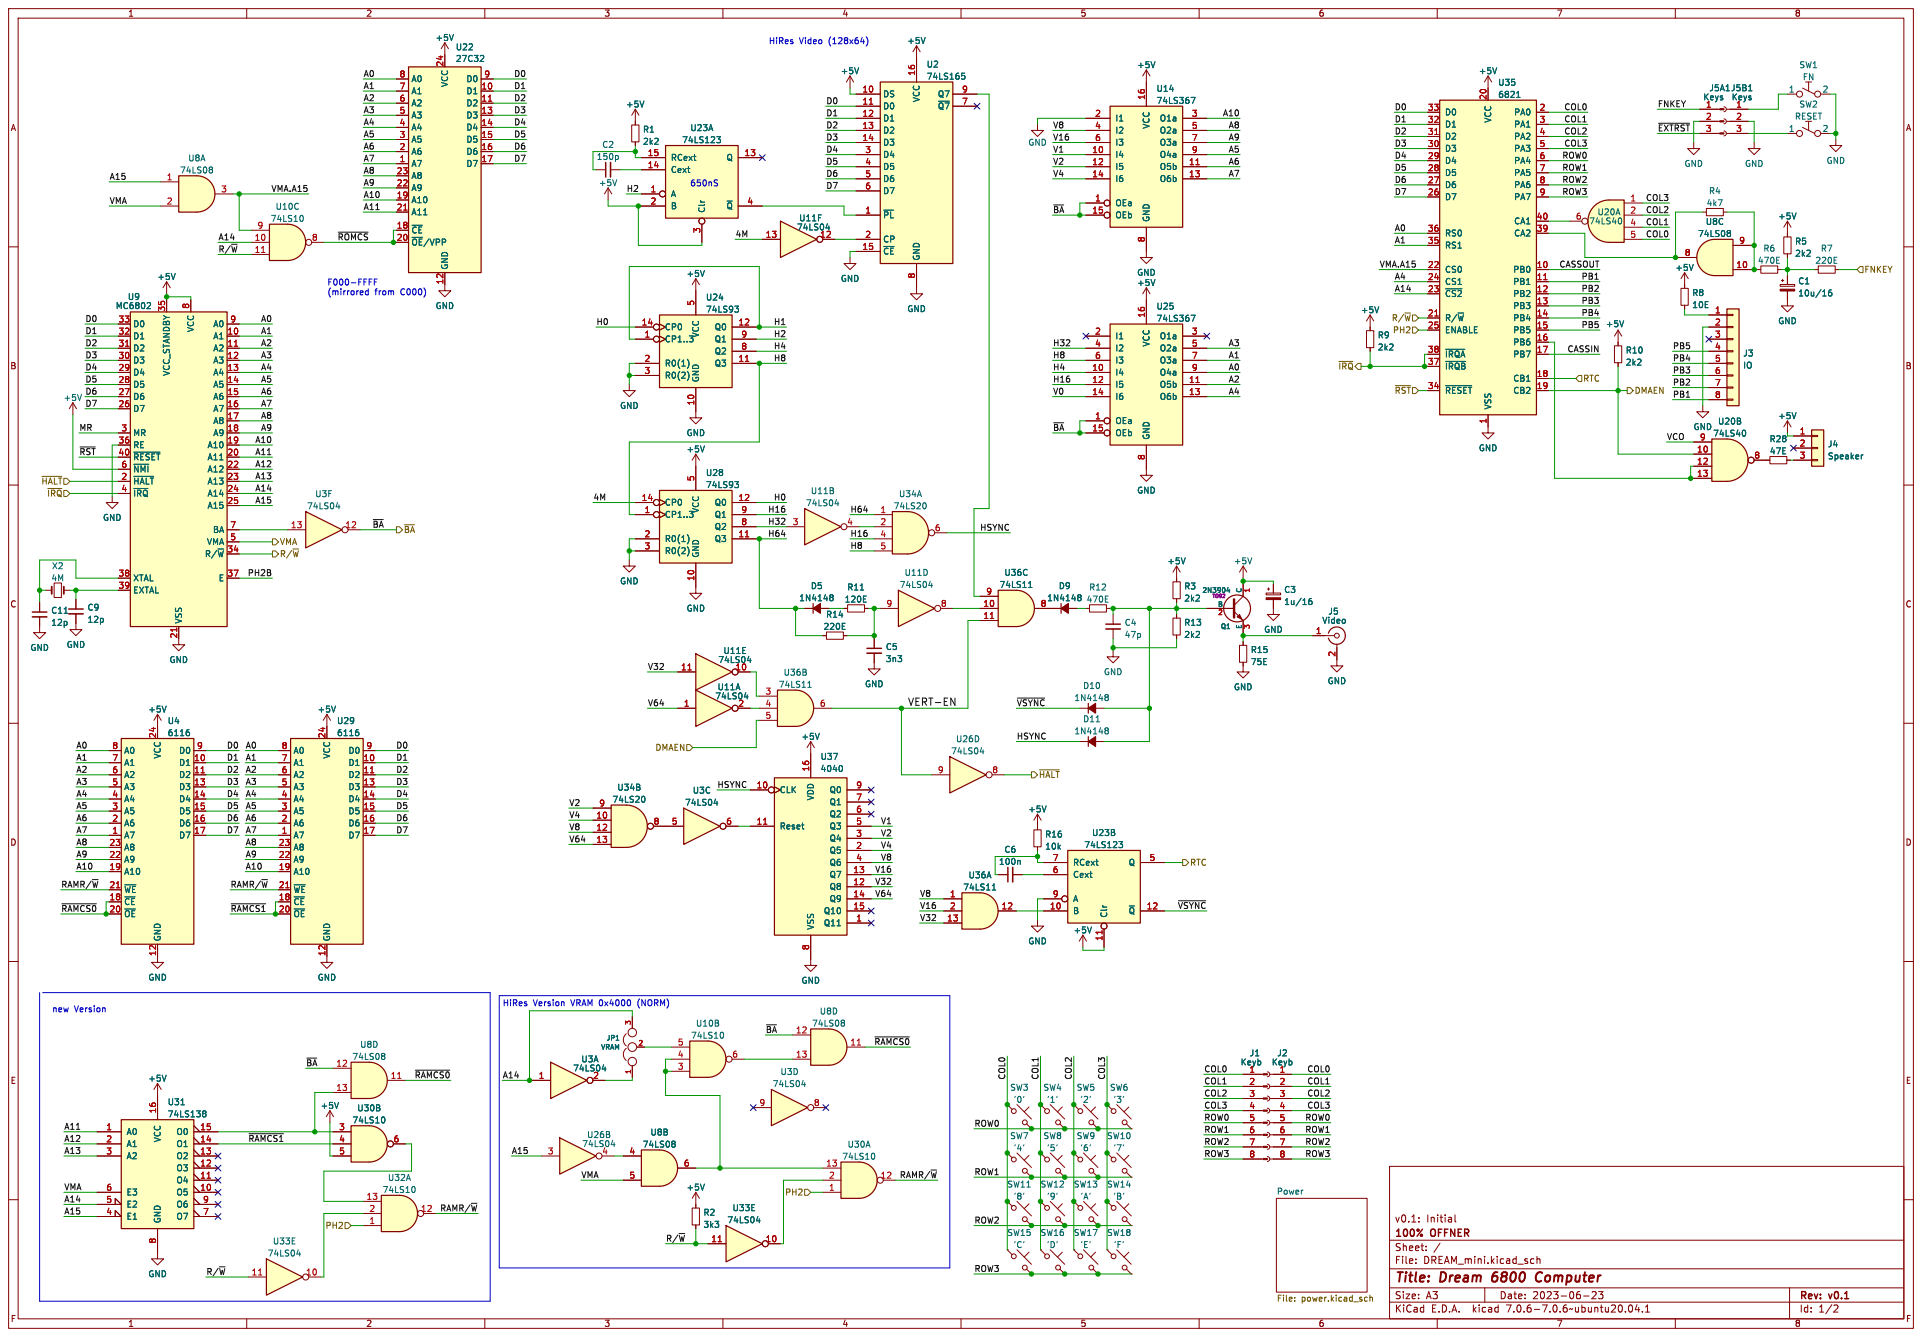
[picture p40: page 1]

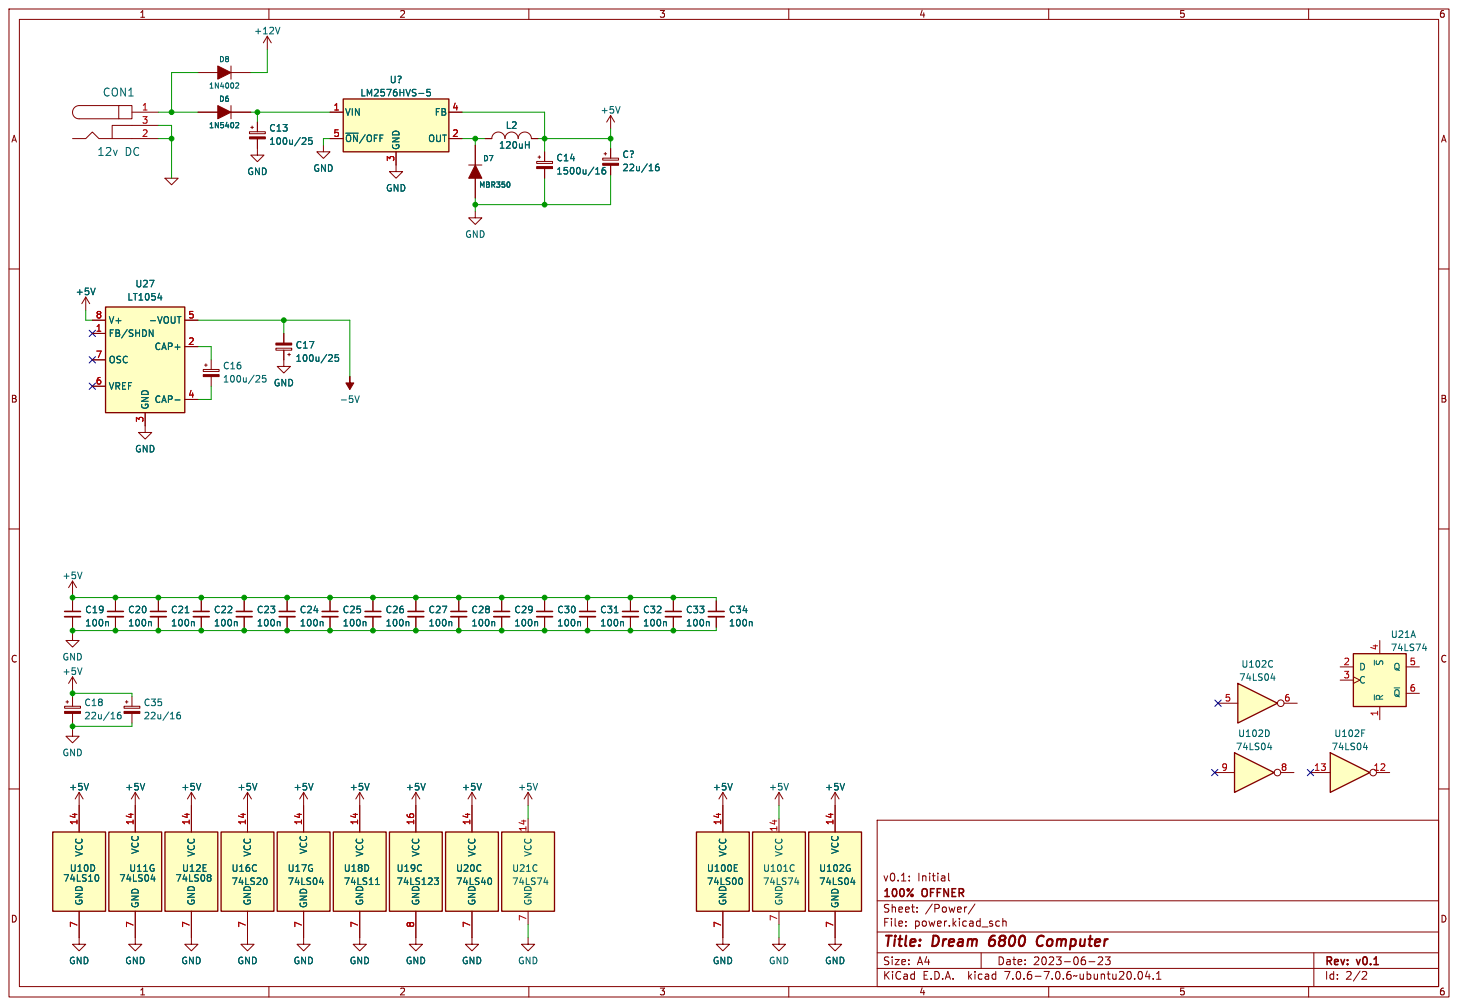
[picture p41: page 2]

3 FB 4 ~{ON}/OFF 5 GND

Id: 2/2 Title: Dream 6800 Computer File: power.kicad_sch Sheet: /Power/ 100% OFFNER
