roberto314/Unicomp2/empty_board_w_mapping_ram2/pdf/empty_board_w_mapping_ram2.pdf

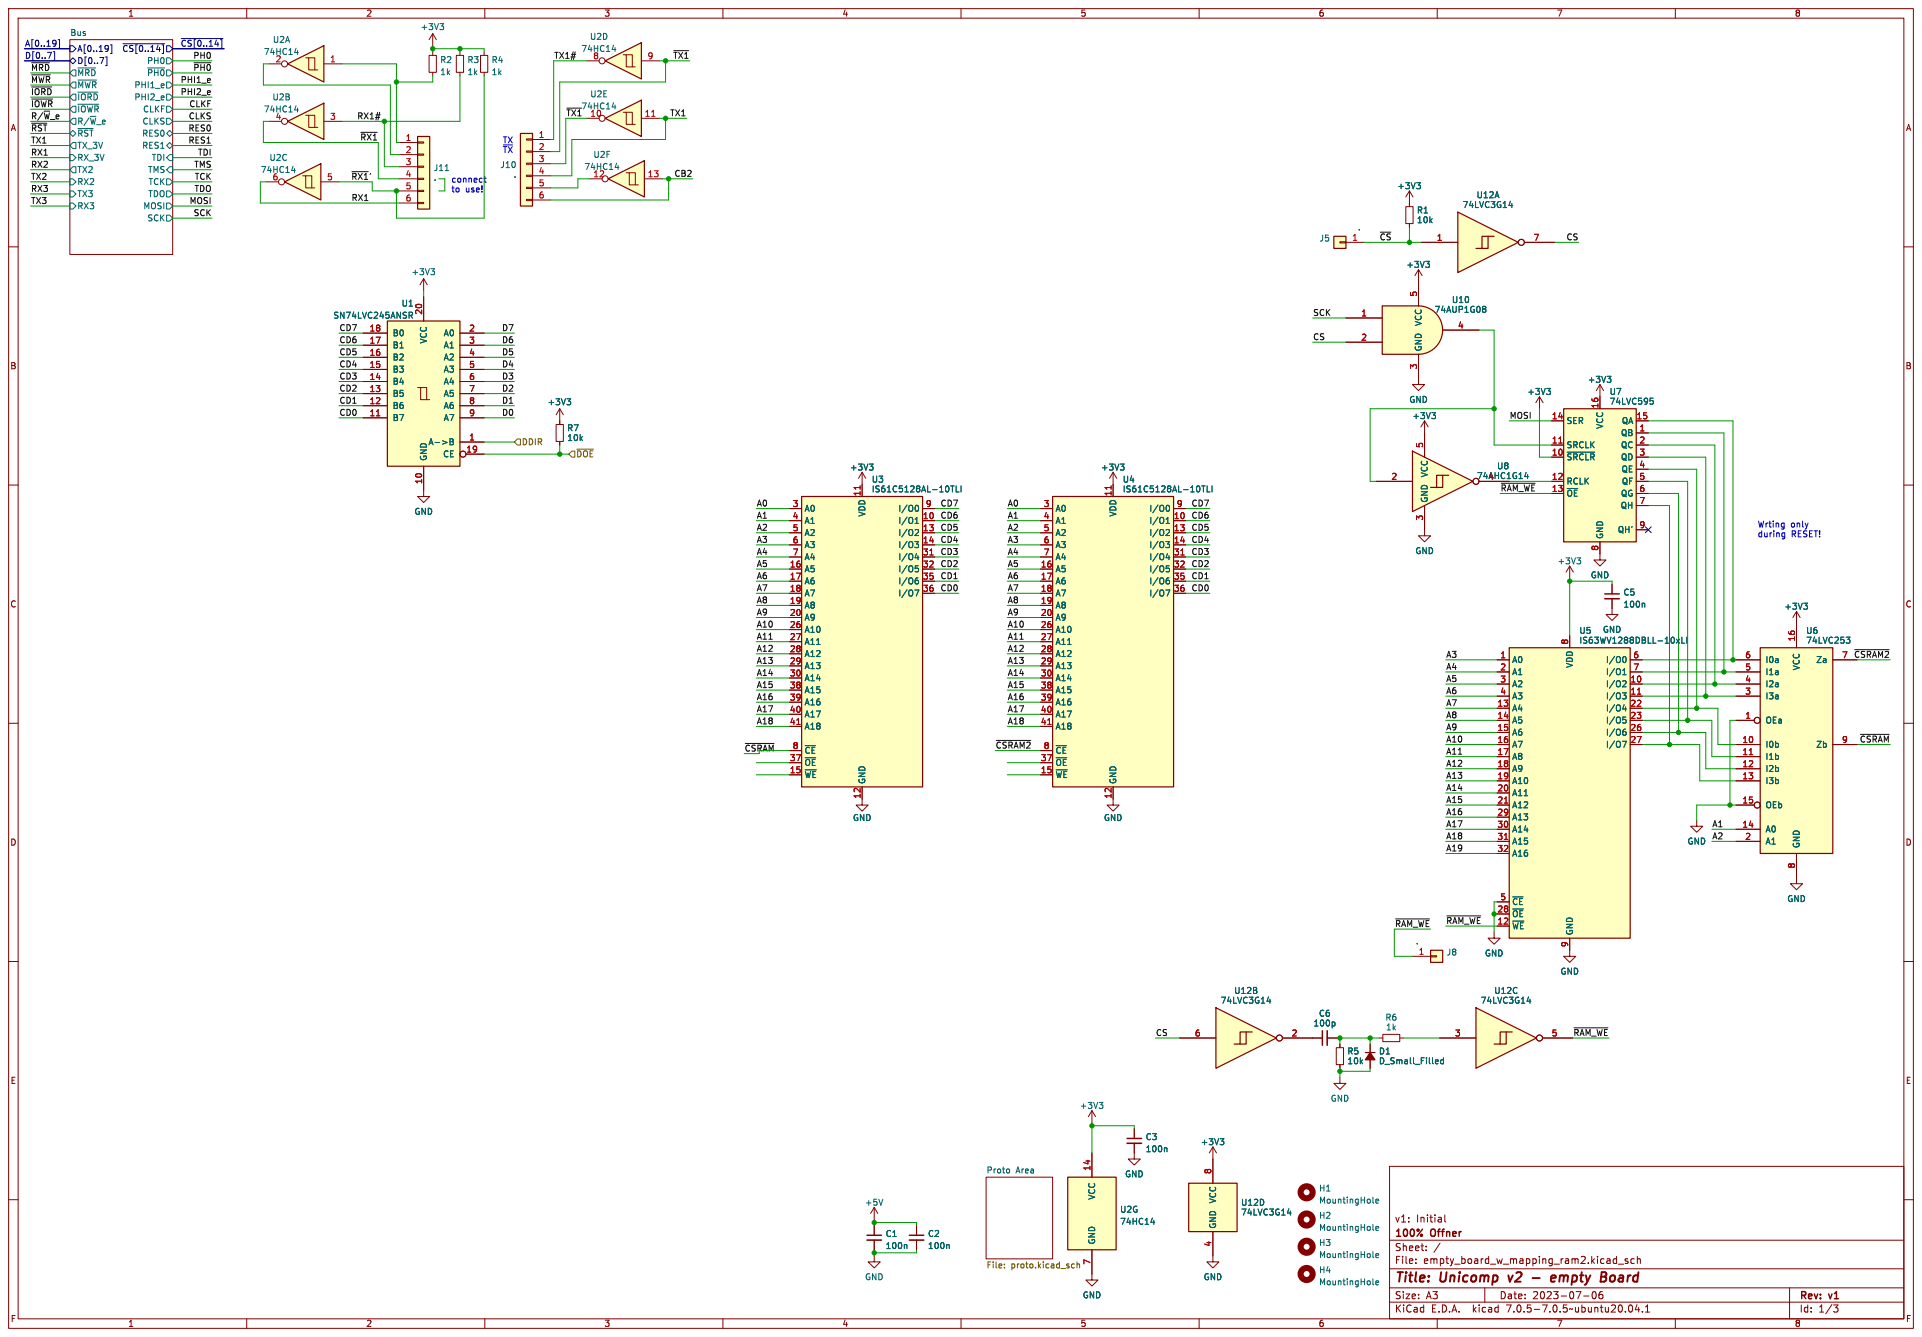
[picture p42: page 1]

File: empty_board_w_mapping_ram2.kicad_sch Sheet: / 100% Offner v1: Initial Proto Area File: proto.kicad_sch

Id: 1/3 Title: Unicomp v2 - empty Board

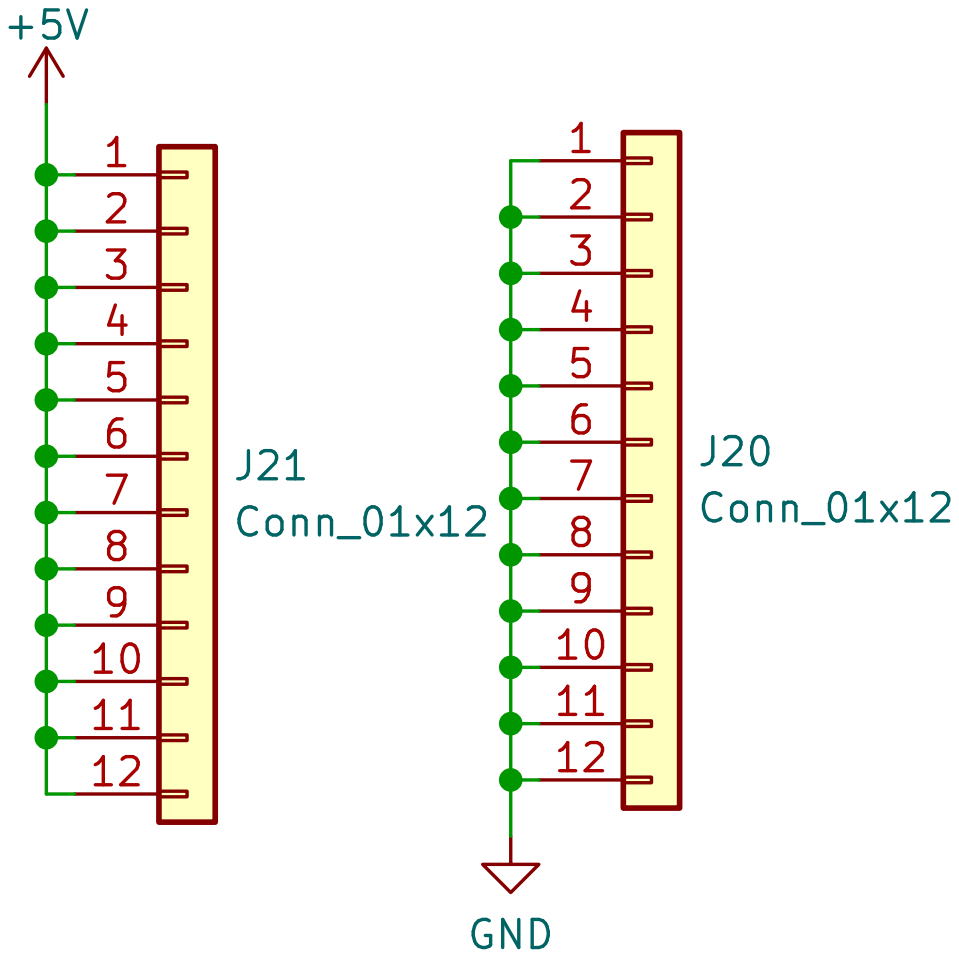
[picture p43: page 2]

Id: 2/3 Title: Unicomp v2 - empty Board

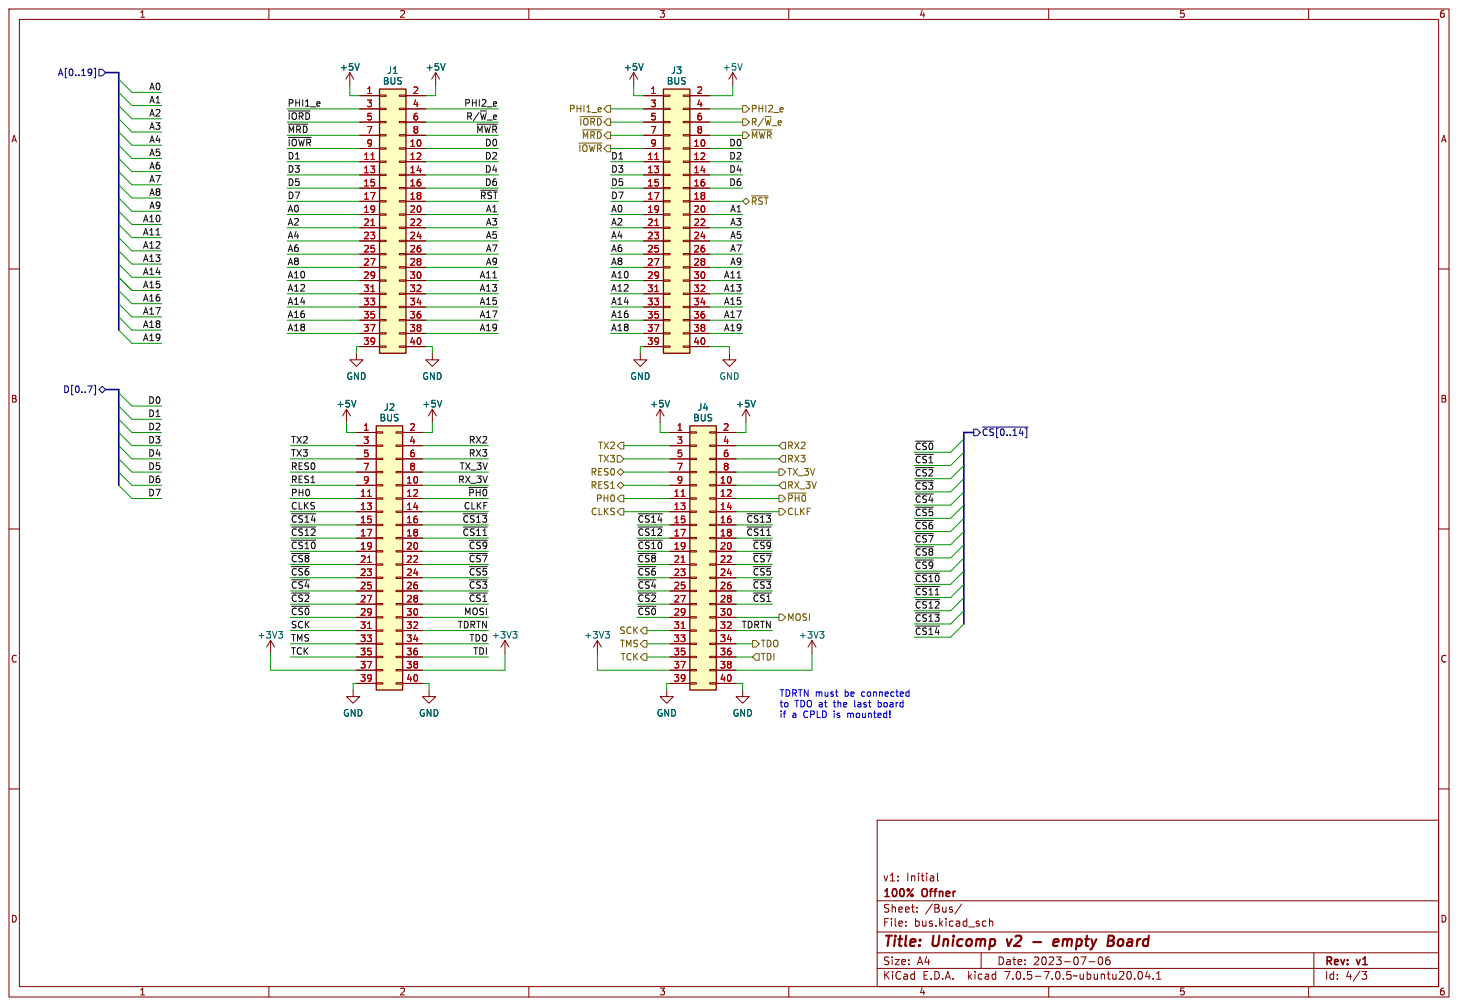
[picture p44: page 3]

if a CPLD is mounted! +5VGND

to TDO at the last board

Id: 4/3 Title: Unicomp v2 - empty Board
