roberto314/Unicomp2/empty_CPU_board_w_CPLD/pdf/empty_CPU_board_w_CPLD.pdf

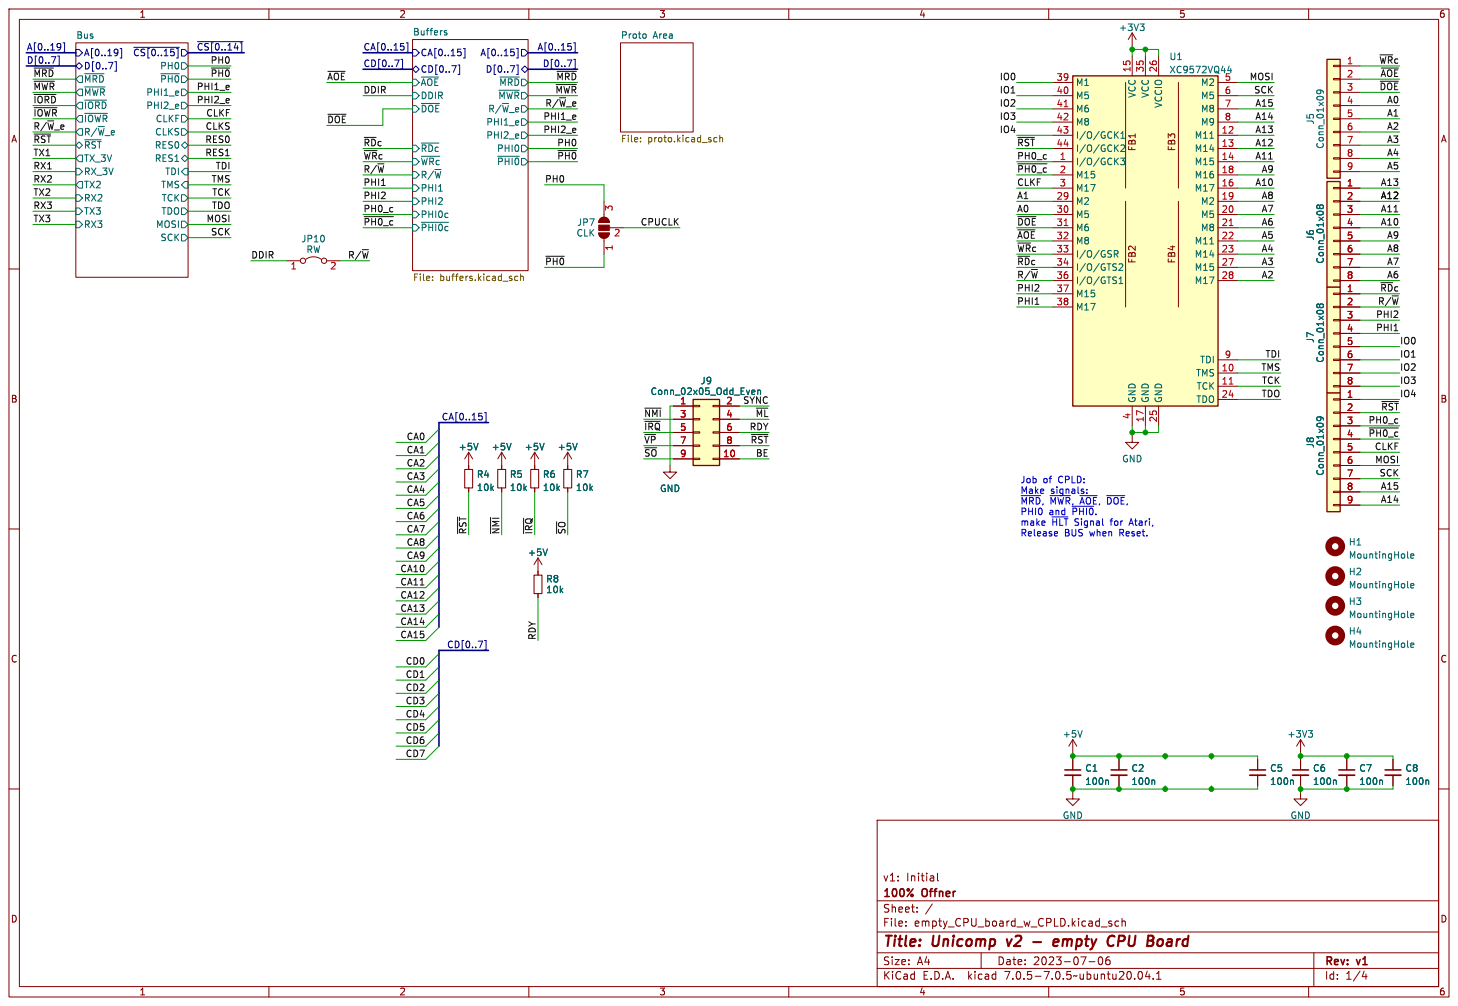
[picture p45: page 1]

Job of CPLD: Make signals:

Id: 1/4 Title: Unicomp v2 - empty CPU Board

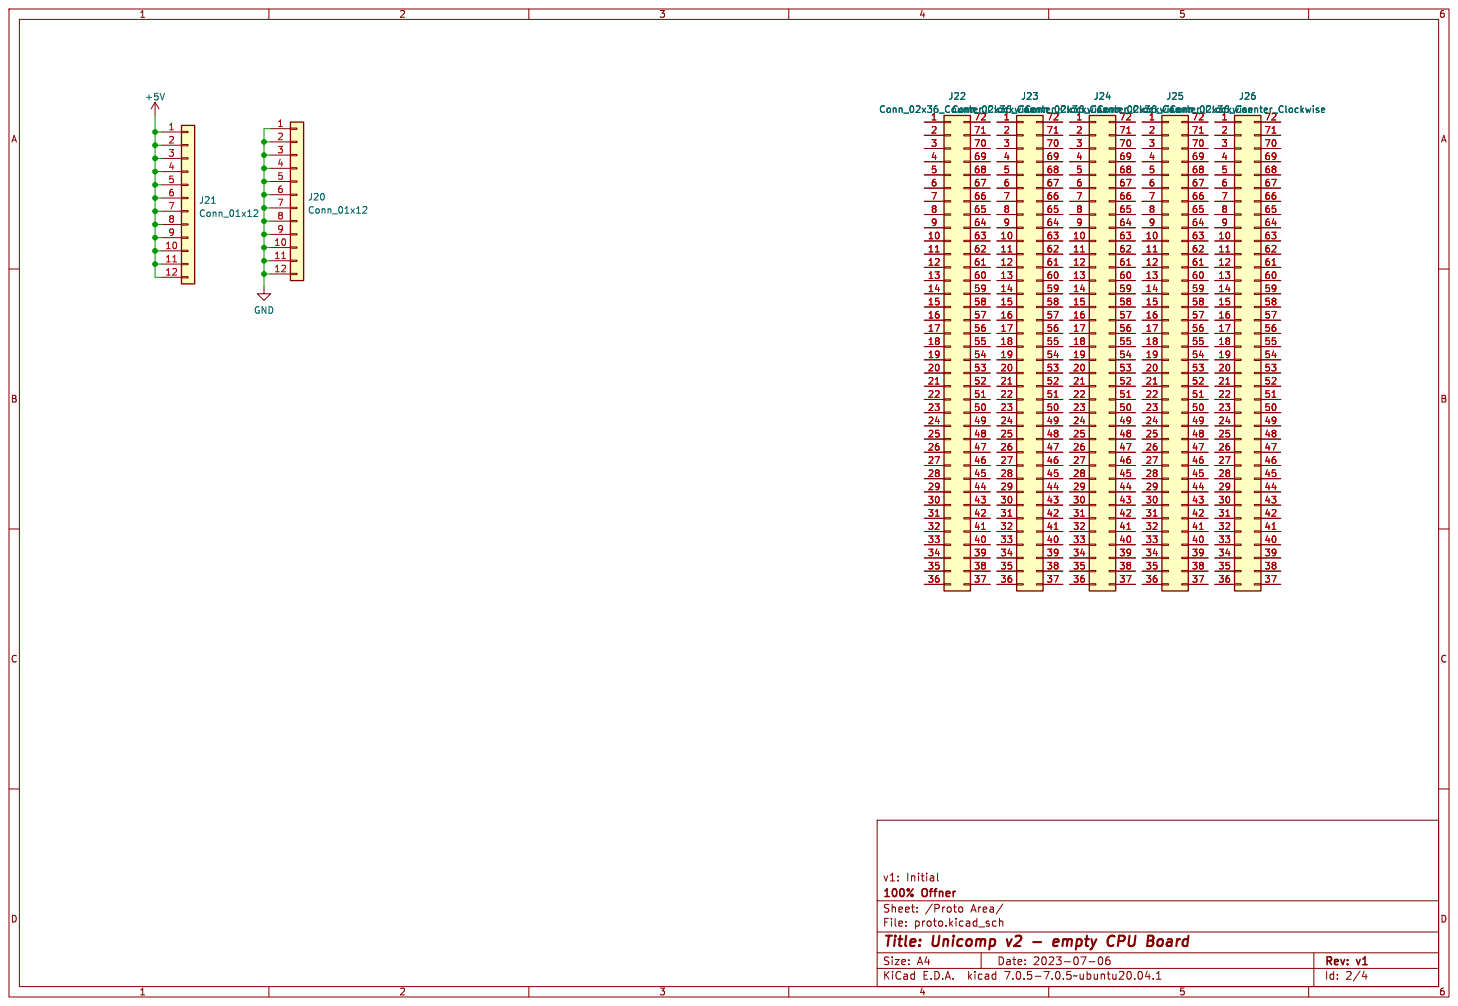
[picture p46: page 2]

Id: 2/4 Title: Unicomp v2 - empty CPU Board

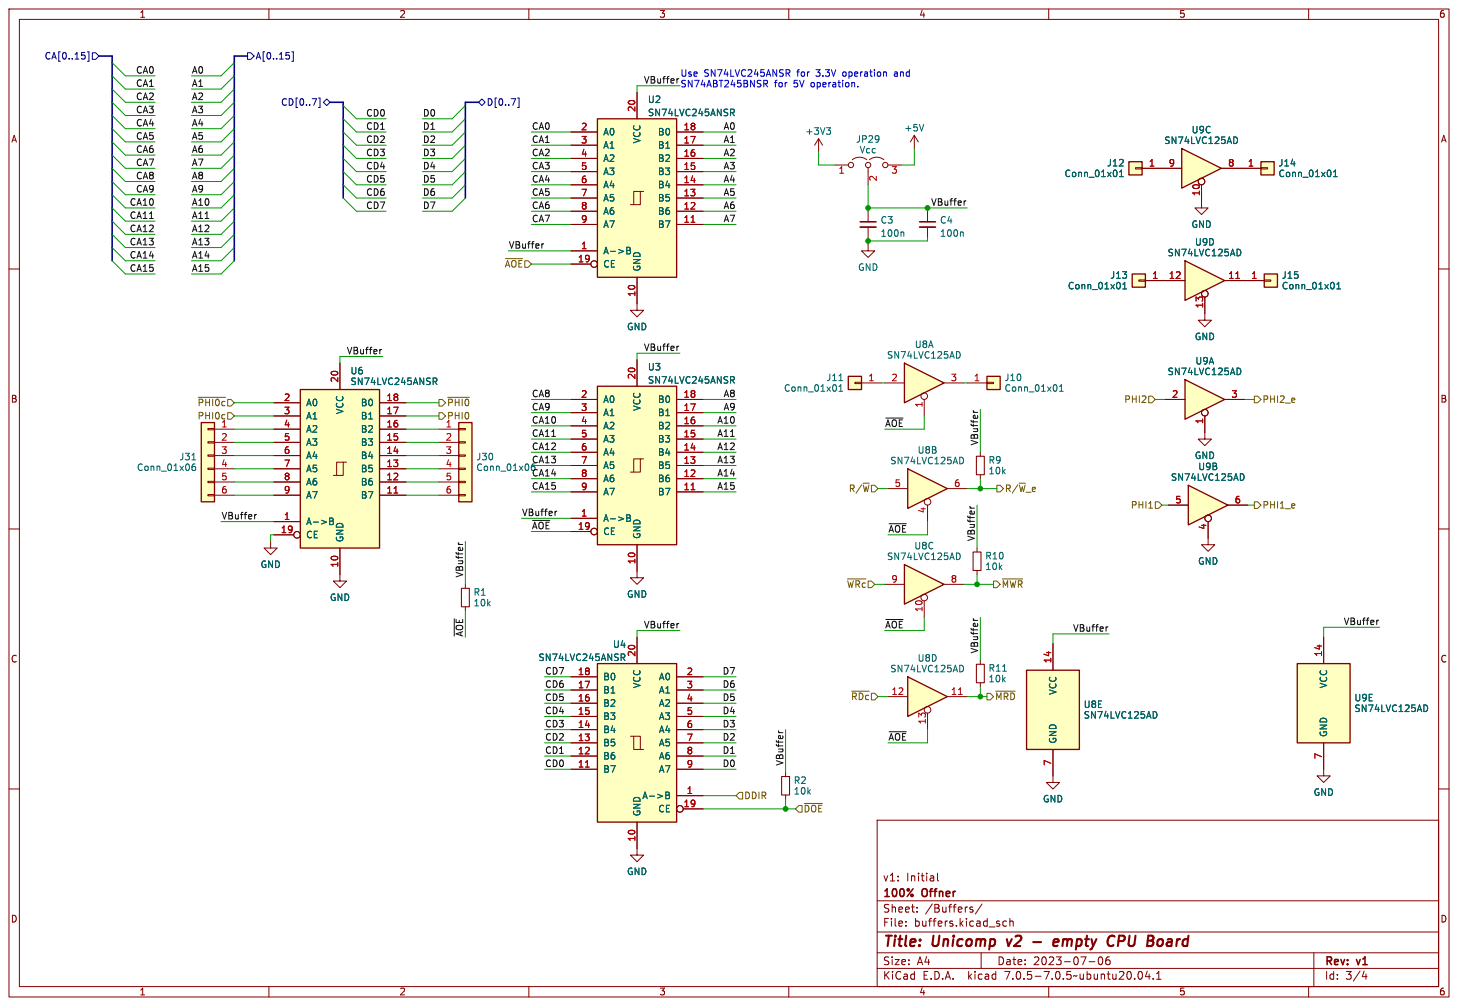
[picture p47: page 3]

Id: 3/4 Title: Unicomp v2 - empty CPU Board

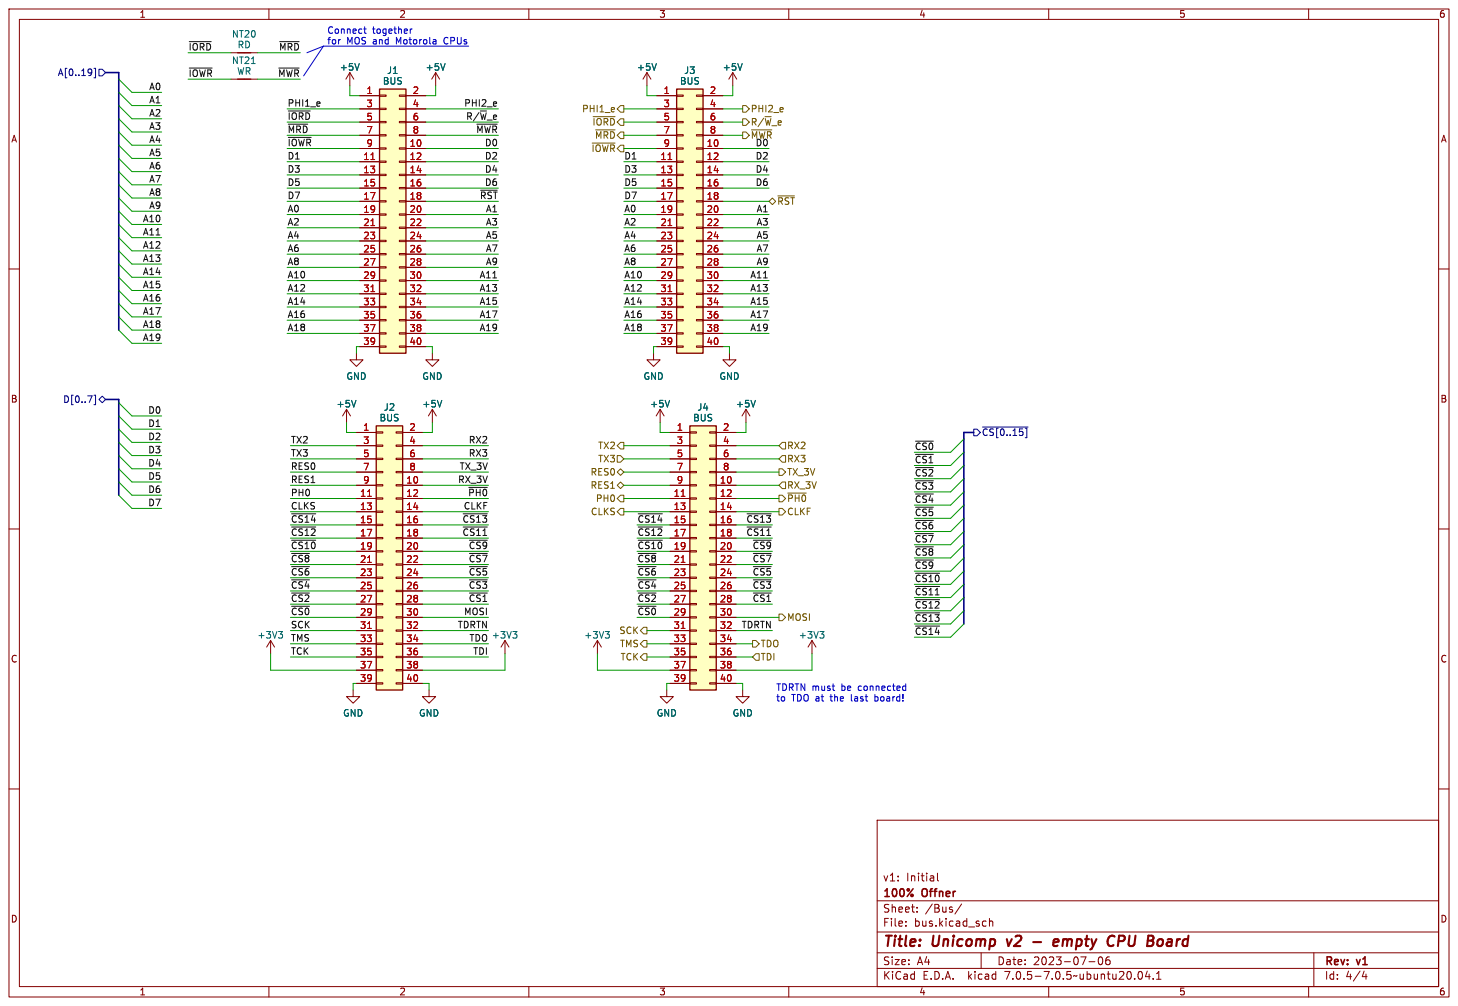
[picture p48: page 4]

for MOS and Motorola CPUs
R/~{W}_eCLKF RX_3V

TDRTN must be connected

Id: 4/4 Title: Unicomp v2 - empty CPU Board
