roberto314/Unicomp2/LCDBoard/Unicomp_LCD_Board/pdf/Unicomp_LCD_Board.pdf

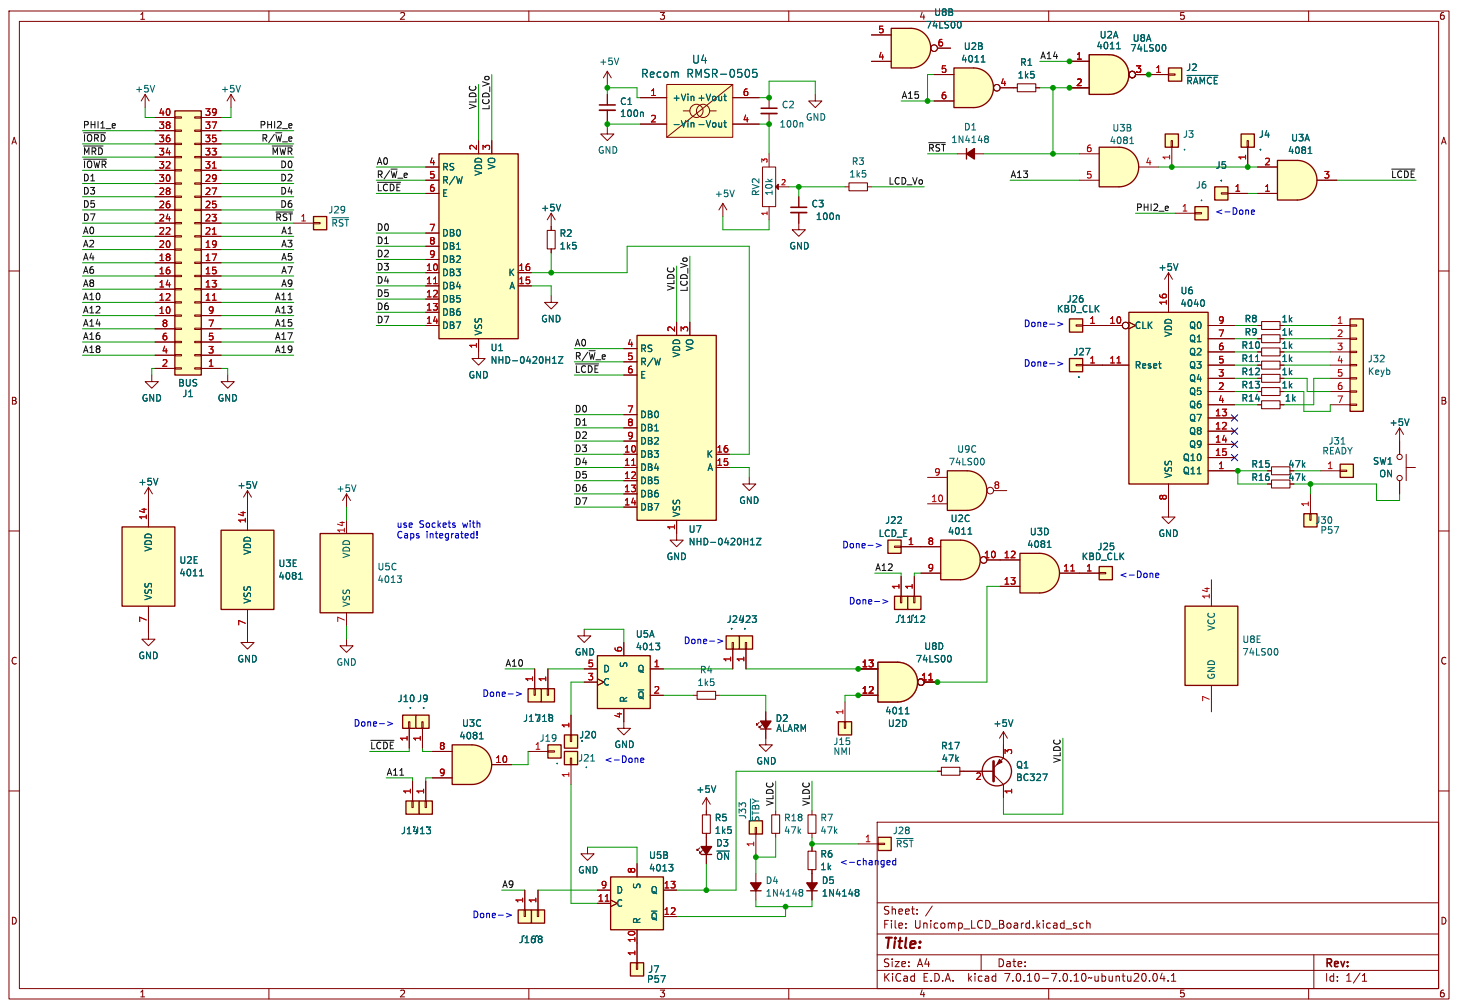
[picture p49: page 1]

use Sockets with Caps integrated! Done->

Id: 1/1 Title: File: Unicomp_LCD_Board.kicad_sch Sheet: /
