roberto314/Unicomp2/not produced boards/RAMROM_128k_board/pdf/RAMROM_128k_board.pdf

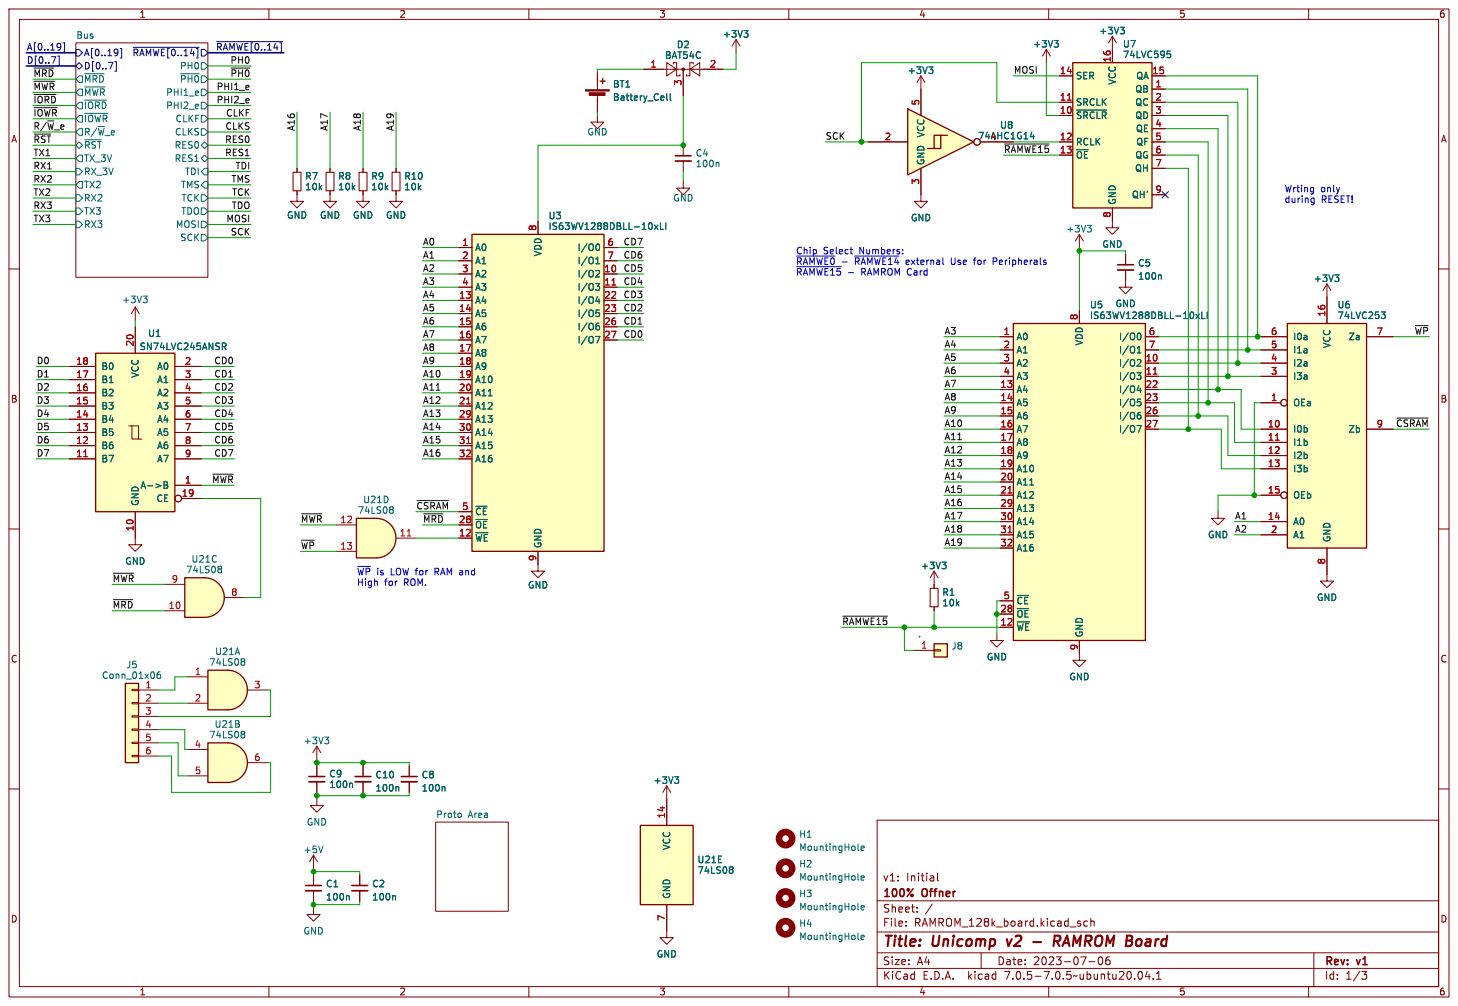
[picture p50: page 1]

Id: 1/3 Title: Unicomp v2 - RAMROM Board

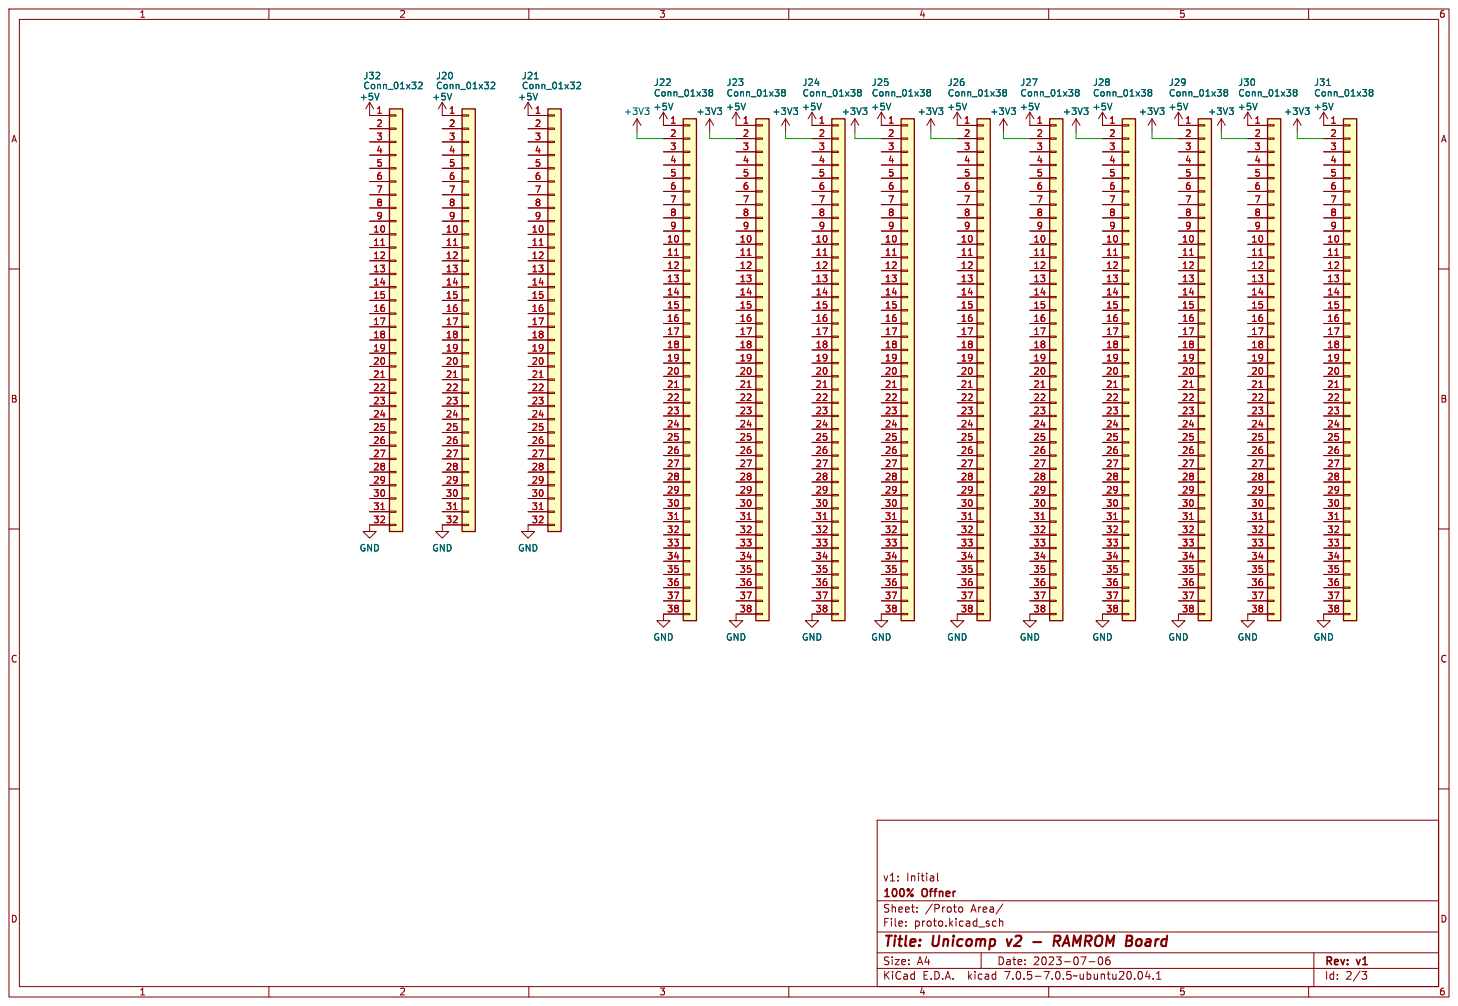
[picture p51: page 2]

Id: 2/3 Title: Unicomp v2 - RAMROM Board

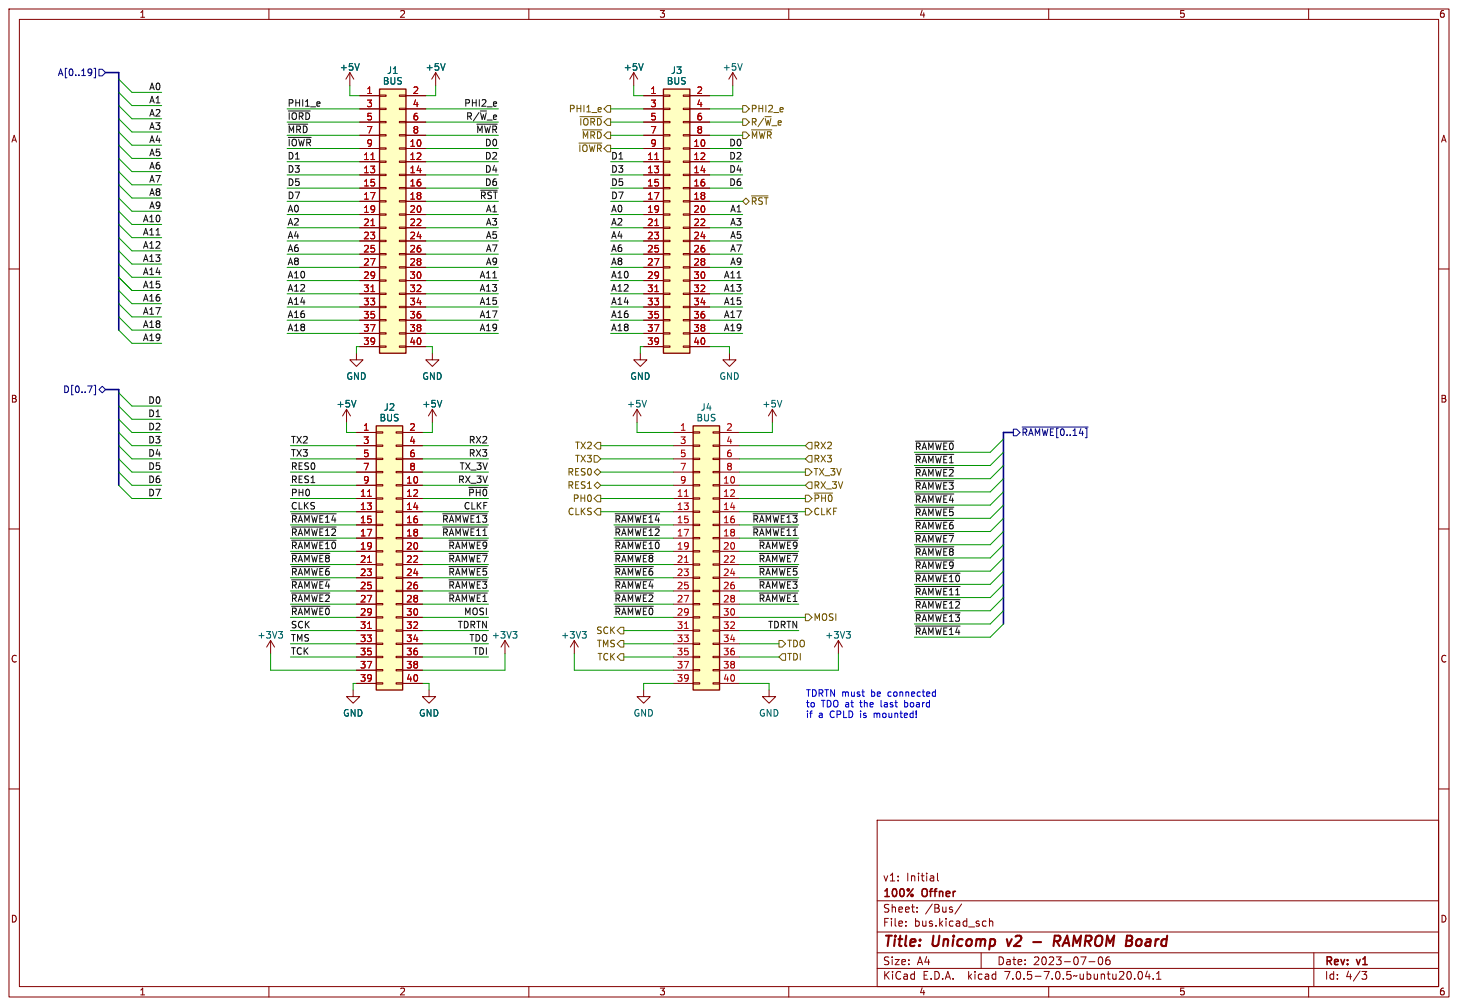
[picture p52: page 3]

to TDO at the last board
if a CPLD is mounted!

Id: 4/3 Title: Unicomp v2 - RAMROM Board
