roberto314/Unicomp2/not produced boards/RAMROM_CPLD_board/pdf/RAMROM_CPLD_board.pdf

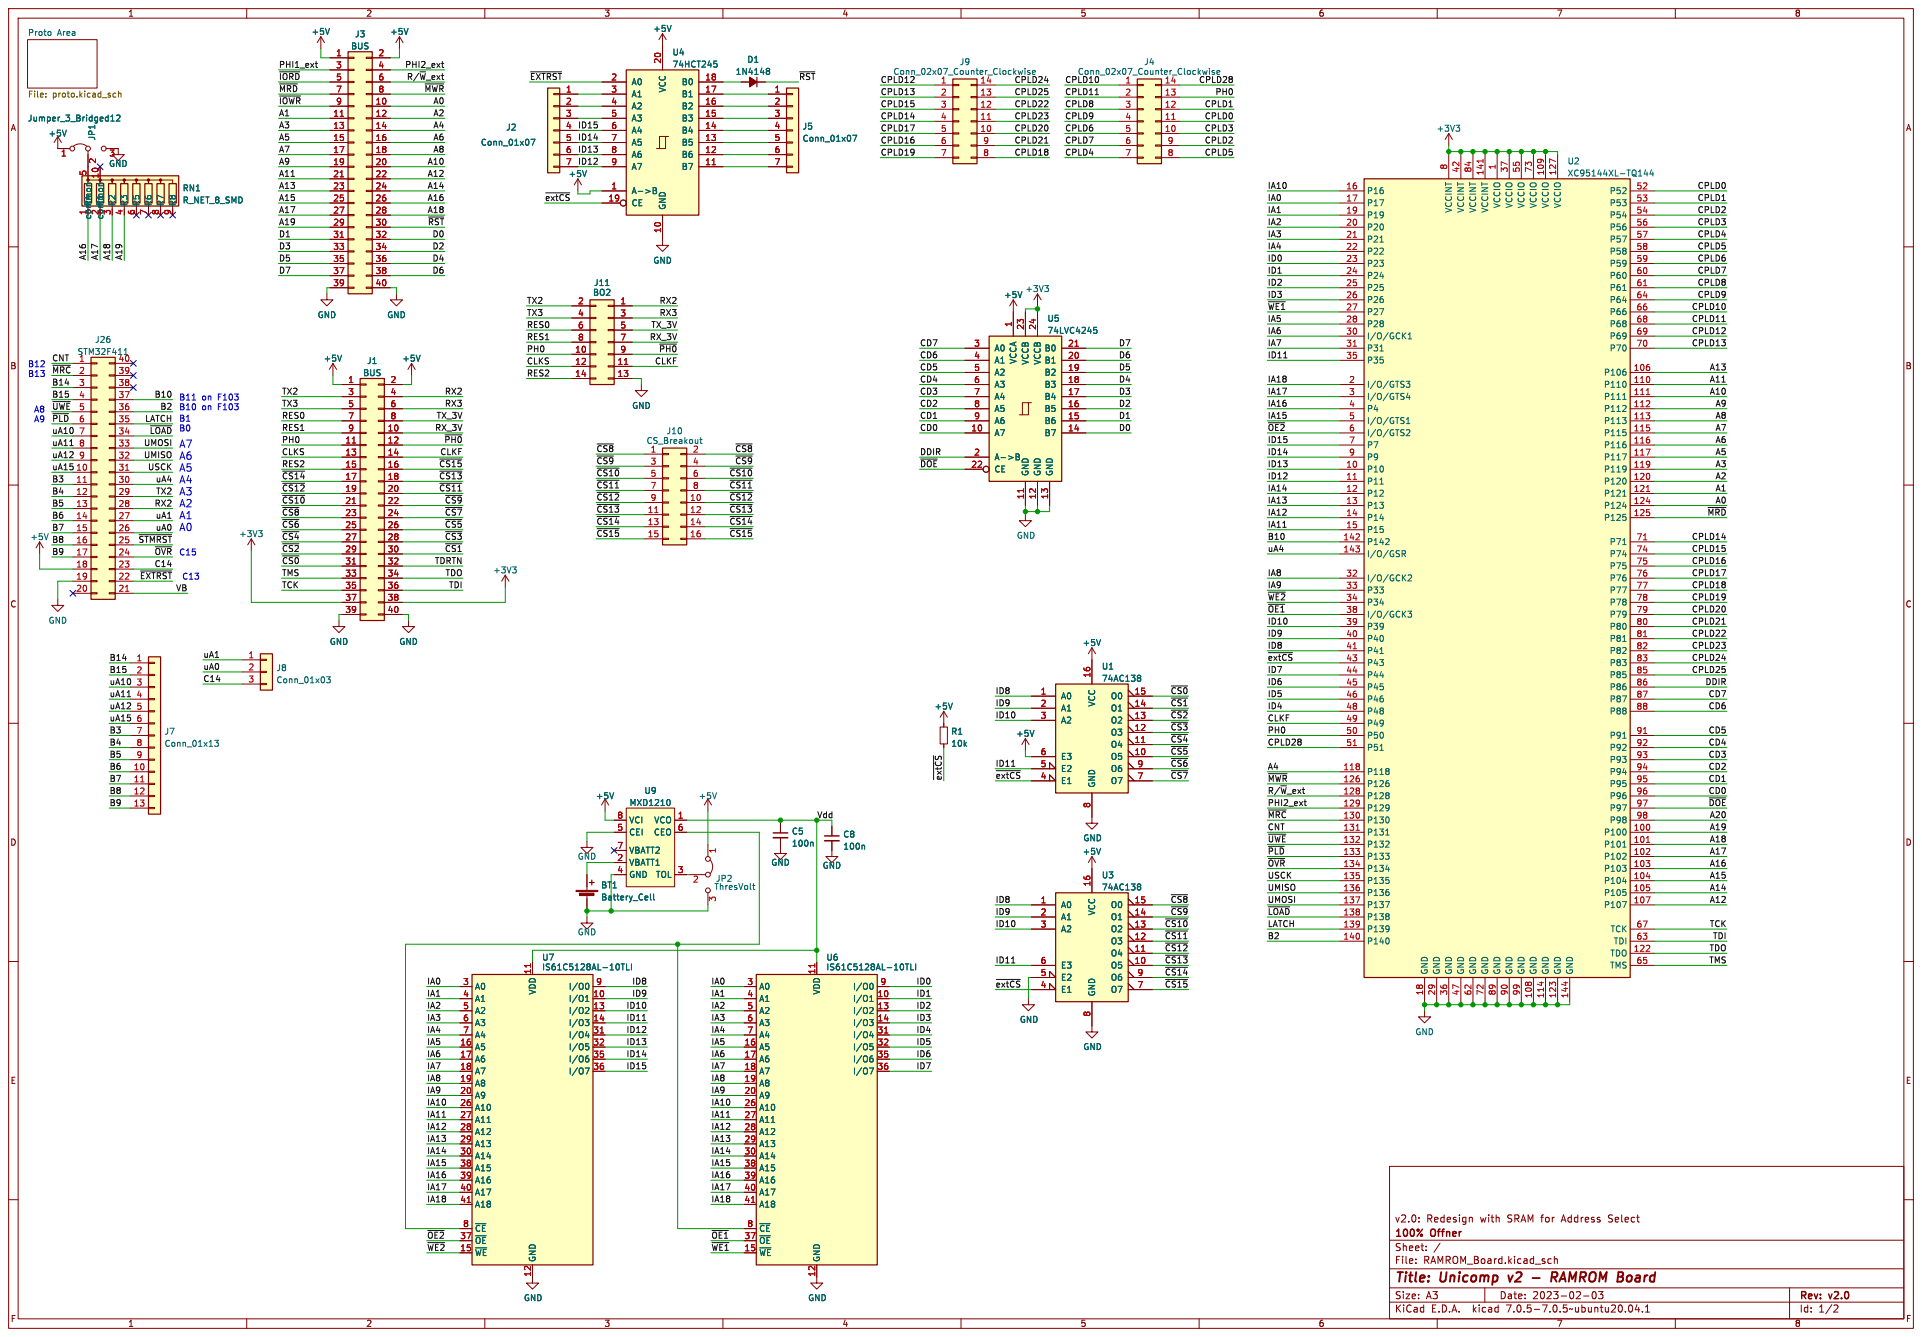
[picture p53: page 1]

8 P80 80 P81 81 P82 82 P83 83 VCCINT 84 P85 85 P86 86 P87 87 P88 88 GND 89 P9 9 GND 90 P91 91 P92 92 P93 93 P94 94 P95 95 P96 96 P97 97 P98 98 GND 99 U2XC95144XL-TQ144

1 A7 10 GND 11 GND 12 GND 13 B7 14 B6 15 B5 16 B4 17 B3 18 B2 19 A->B 2 B1 20 B0 21 CE 22 VCCB 23 VCCB 24 A0 3 A1 4 A2 5 A3 6 A4 7 A5 8 A6 9 U5

1 A7 10 GND 11 GND 12 GND 13 B7 14 B6 15 B5 16 B4 17 B3 18 B2 19 A->B 2 B1 20 B0 21 CE 22 VCCB 23 VCCB 24 A0 3 A1 4 A2 5 A3 6 A4 7 A5 8 A6 9 +5V U1

Id: 1/2 Title: Unicomp v2 - RAMROM Board

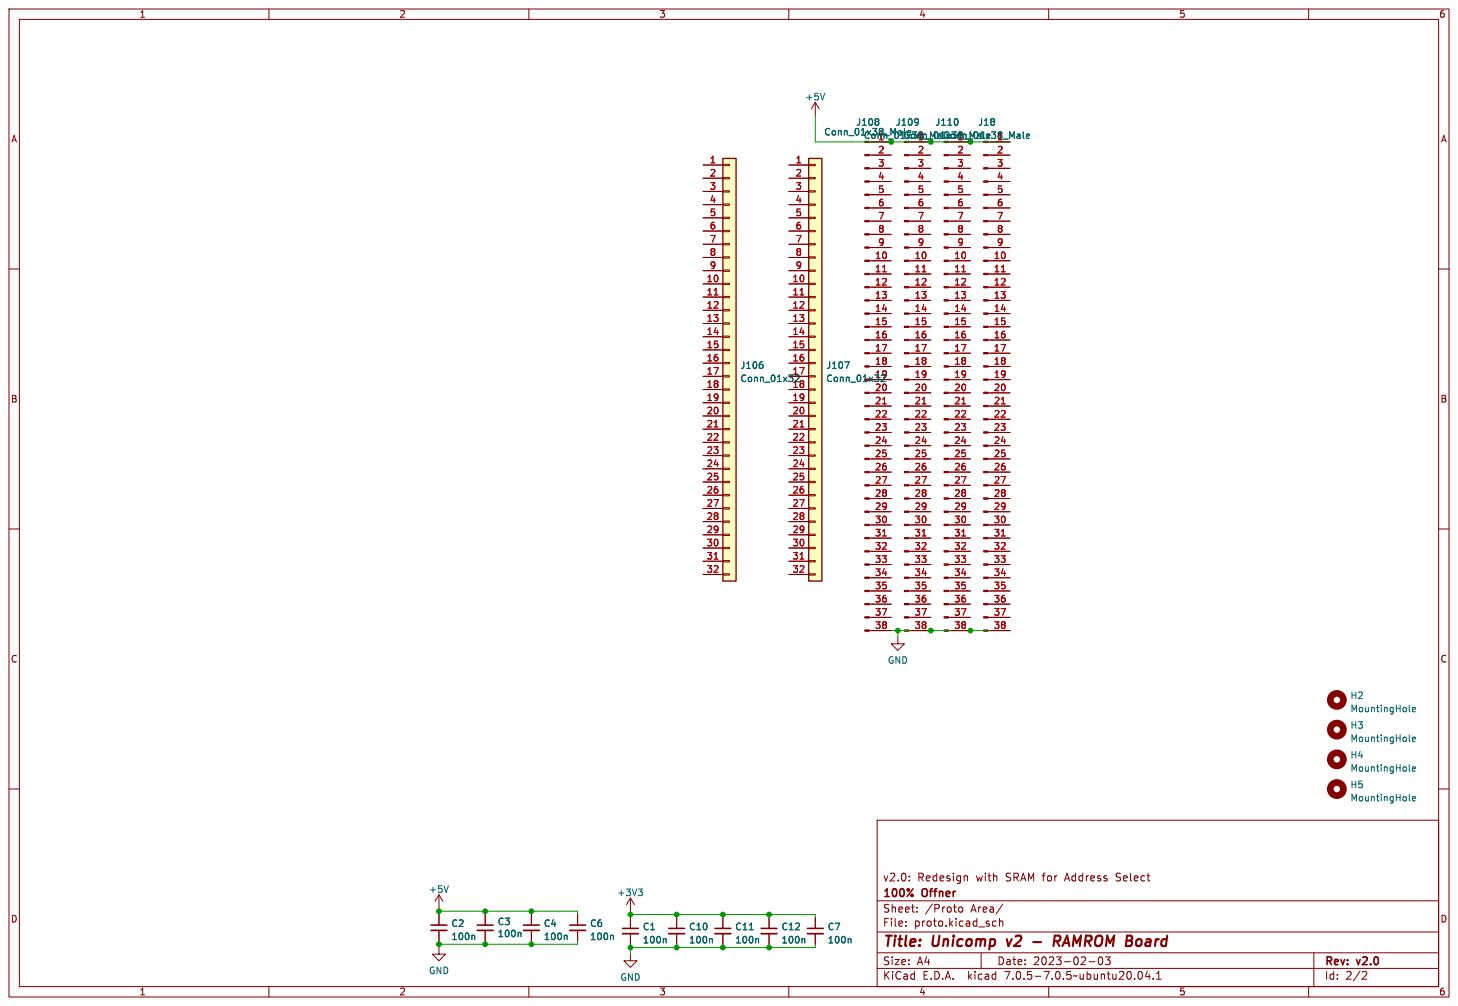
[picture p54: page 2]

Id: 2/2 Title: Unicomp v2 - RAMROM Board
