roberto314/Unicomp2/Synertek KTM2/UC2_synertek_KTM2/pdf/UC2_synertek_KTM2.pdf

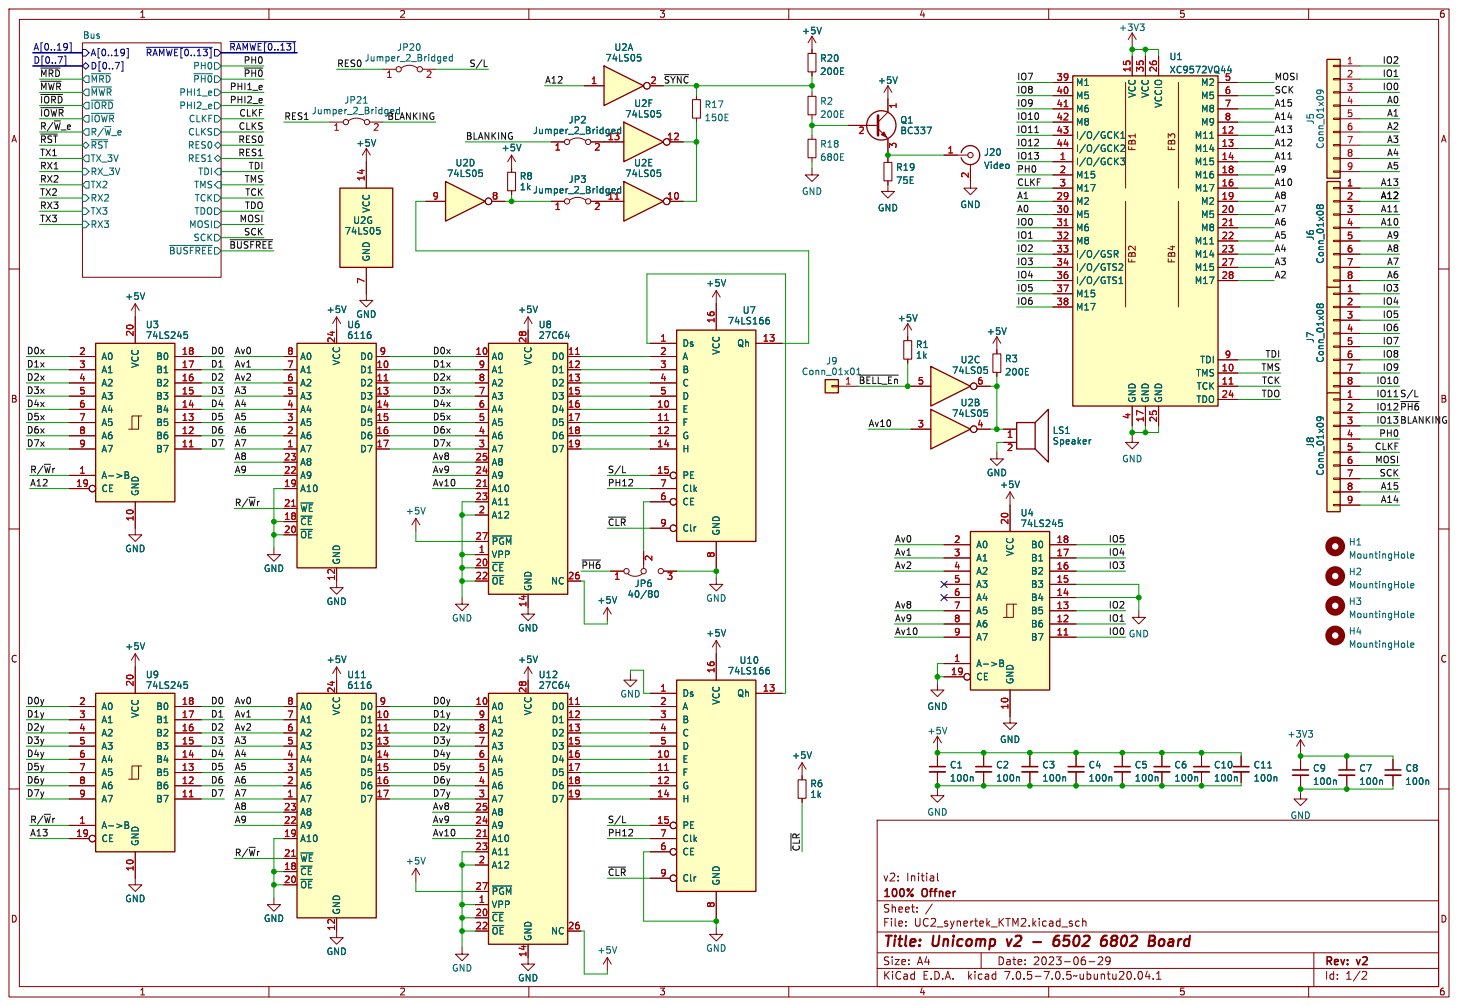
[picture p55: page 1]

Id: 1/2 Title: Unicomp v2 - 6502 6802 Board

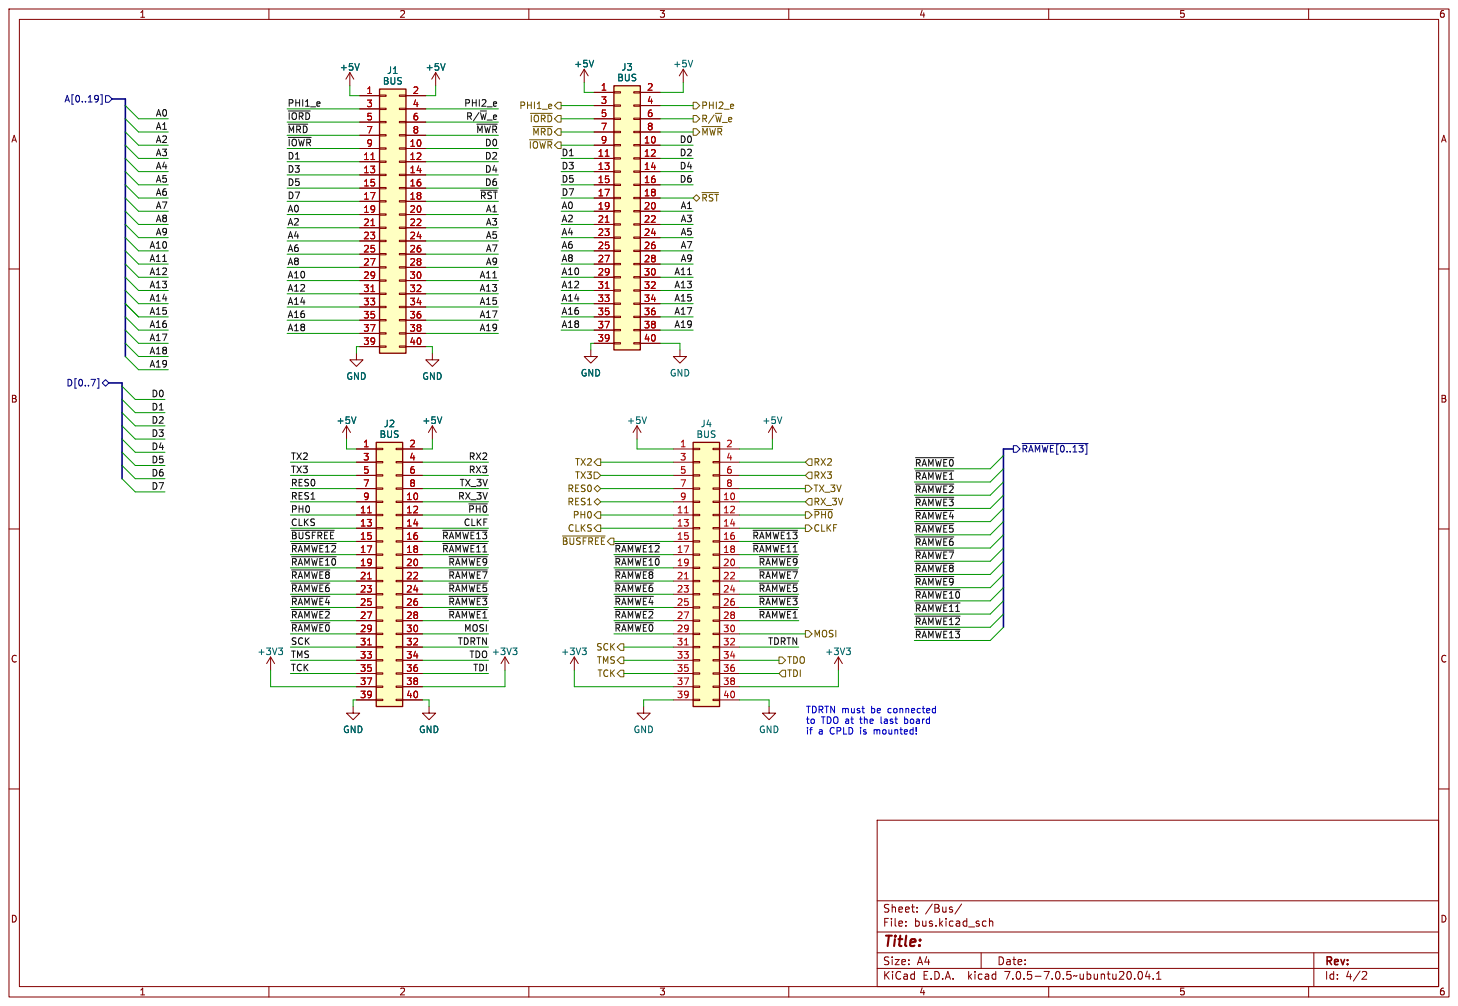
[picture p56: page 2]

Id: 4/2 Title: File: bus.kicad_sch Sheet: /Bus/
