roberto314/Unicomp2/Splitter Board/schematic/SplitterBoard/SplitterBoard.kicad_pcb

## KiCad design Splitter Board/schematic/SplitterBoard/SplitterBoard.kicad_pcb (2023-09-11)

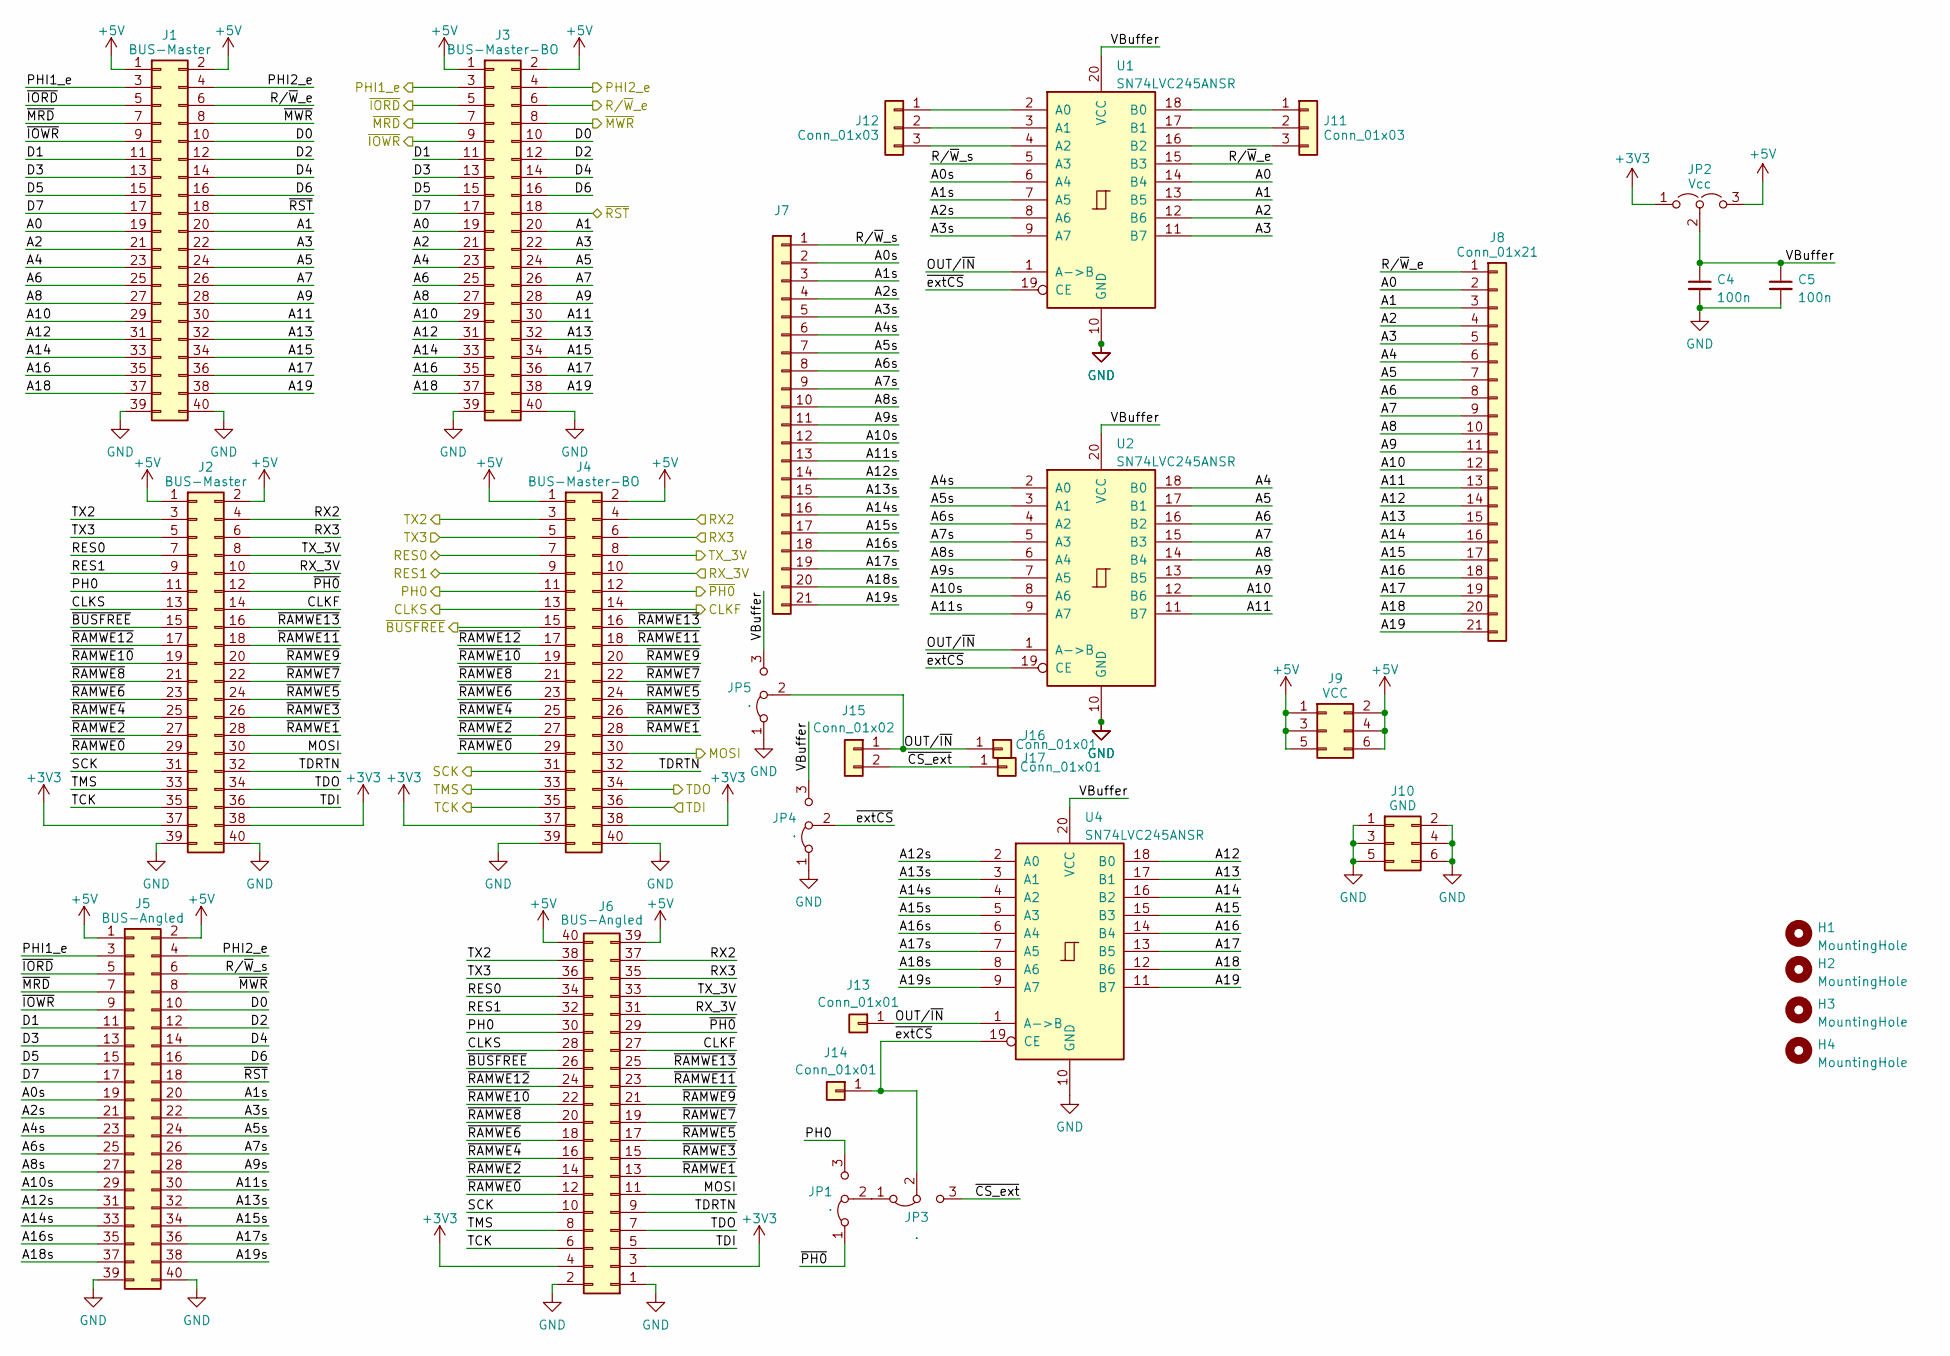
[picture p89: schematic SplitterBoard.kicad_sch, Unicomp v2 - Splitter Board]

Parts:
C4, C5: 100n; C_1206_3216Metric
H1, H2, H3, H4: MountingHole; MountingHole_3.2mm_M3
J1, J2: BUS-Master; PinSocket_2x20_P2.54mm_Vertical
J3, J4: BUS-Master-BO; PinSocket_2x20_P2.54mm_Vertical
J5, J6: BUS-Angled; PinHeader_2x20_P2.54mm_Horizontal
J7, J8: Conn_01x21; PinHeader_1x21_P2.54mm_Vertical
J9: VCC; PinHeader_2x03_P2.54mm_Vertical
J10: GND; PinHeader_2x03_P2.54mm_Vertical
J11, J12: Conn_01x03; PinHeader_1x03_P2.54mm_Vertical
J13, J14, J16, J17: Conn_01x01; PinHeader_1x01_P2.00mm_Vertical
J15: Conn_01x02; PinHeader_1x02_P2.54mm_Vertical
JP1, JP3, JP4, JP5: .; SolderJumper-3_P1.3mm_Open_Pad1.0x1.5mm_NumberLabels
JP2: Vcc; SolderJumper-3_P1.3mm_Open_RoundedPad1.0x1.5mm_NumberLabels
U1, U2, U4: SN74LVC245ANSR; SO-20_5.3x12.6mm_P1.27mm

Connections:
+3V3: J2.37, J2.38, J4.37, J4.38, J6.3, J6.4, JP2.1 (A)
+5V: J1.1, J1.2, J2.1, J2.2, J3.1, J3.2, J4.1, J4.2, J5.1, J5.2, J6.39, J6.40, J9.1, J9.2, J9.3, J9.4, J9.5, J9.6, JP2.3 (B)
/A0: J1.19, J3.19, J8.2, U1.14 (B4)
/A0s: J5.19, J7.2, U1.6 (A4)
/A1: J1.20, J3.20, J8.3, U1.13 (B5)
/A1s: J5.20, J7.3, U1.7 (A5)
/A2: J1.21, J3.21, J8.4, U1.12 (B6)
/A2s: J5.21, J7.4, U1.8 (A6)
/A3: J1.22, J3.22, J8.5, U1.11 (B7)
/A3s: J5.22, J7.5, U1.9 (A7)
/A4: J1.23, J3.23, J8.6, U2.18 (B0)
/A4s: J5.23, J7.6, U2.2 (A0)
/A5: J1.24, J3.24, J8.7, U2.17 (B1)
/A5s: J5.24, J7.7, U2.3 (A1)
/A6: J1.25, J3.25, J8.8, U2.16 (B2)
/A6s: J5.25, J7.8, U2.4 (A2)
/A7: J1.26, J3.26, J8.9, U2.15 (B3)
/A7s: J5.26, J7.9, U2.5 (A3)
/A8: J1.27, J3.27, J8.10, U2.14 (B4)
/A8s: J5.27, J7.10, U2.6 (A4)
/A9: J1.28, J3.28, J8.11, U2.13 (B5)
/A9s: J5.28, J7.11, U2.7 (A5)
/A10: J1.29, J3.29, J8.12, U2.12 (B6)
/A10s: J5.29, J7.12, U2.8 (A6)
/A11: J1.30, J3.30, J8.13, U2.11 (B7)
/A11s: J5.30, J7.13, U2.9 (A7)
/A12: J1.31, J3.31, J8.14, U4.18 (B0)
/A12s: J5.31, J7.14, U4.2 (A0)
/A13: J1.32, J3.32, J8.15, U4.17 (B1)
/A13s: J5.32, J7.15, U4.3 (A1)
/A14: J1.33, J3.33, J8.16, U4.16 (B2)
/A14s: J5.33, J7.16, U4.4 (A2)
/A15: J1.34, J3.34, J8.17, U4.15 (B3)
/A15s: J5.34, J7.17, U4.5 (A3)
/A16: J1.35, J3.35, J8.18, U4.14 (B4)
/A16s: J5.35, J7.18, U4.6 (A4)
/A17: J1.36, J3.36, J8.19, U4.13 (B5)
/A17s: J5.36, J7.19, U4.7 (A5)
/A18: J1.37, J3.37, J8.20, U4.12 (B6)
/A18s: J5.37, J7.20, U4.8 (A6)
/A19: J1.38, J3.38, J8.21, U4.11 (B7)
/A19s: J5.38, J7.21, U4.9 (A7)
/CLKF: J2.14, J4.14, J6.27
/CLKS: J2.13, J4.13, J6.28
/D0: J1.10, J3.10, J5.10
/D1: J1.11, J3.11, J5.11
/D2: J1.12, J3.12, J5.12
/D3: J1.13, J3.13, J5.13
/D4: J1.14, J3.14, J5.14
/D5: J1.15, J3.15, J5.15
/D6: J1.16, J3.16, J5.16
/D7: J1.17, J3.17, J5.17
/MOSI: J2.30, J4.30, J6.11
/OUT/~IN: J13.1, J15.1, J16.1, JP5.2 (C), U1.1 (A->B), U2.1 (A->B), U4.1 (A->B)
/PH0: J2.11, J4.11, J6.30, JP1.3 (B)
/PHI1_e: J1.3, J3.3, J5.3
/PHI2_e: J1.4, J3.4, J5.4
/RES0: J2.7, J4.7, J6.34
/RES1: J2.9, J4.9, J6.32
/RX2: J2.4, J4.4, J6.37
/RX3: J2.6, J4.6, J6.35
/RX_3V: J2.10, J4.10, J6.31
/R/~W_e: J1.6, J3.6, J8.1, U1.15 (B3)
/R/~W_s: J5.6, J7.1, U1.5 (A3)
/SCK: J2.31, J4.31, J6.10
/TCK: J2.35, J4.35, J6.6
/TDI: J2.36, J4.36, J6.5
/TDO: J2.34, J4.34, J6.7
/TDRTN: J2.32, J4.32, J6.9
/TMS: J2.33, J4.33, J6.8
/TX2: J2.3, J4.3, J6.38
/TX3: J2.5, J4.5, J6.36
/TX_3V: J2.8, J4.8, J6.33
/VBuffer: C4.1, C5.1, JP2.2 (C), JP4.3 (B), JP5.3 (B), U1.20 (VCC), U2.20 (VCC), U4.20 (VCC)
/~BUSFREE: J2.15, J4.15, J6.26
/~CS_ext: J15.2, J17.1, JP3.3 (B)
/~IORD: J1.5, J3.5, J5.5
/~IOWR: J1.9, J3.9, J5.9
/~MRD: J1.7, J3.7, J5.7
/~MWR: J1.8, J3.8, J5.8
/~PH0: J2.12, J4.12, J6.29, JP1.1 (A)
/~RAMWE0: J2.29, J4.29, J6.12
/~RAMWE1: J2.28, J4.28, J6.13
/~RAMWE2: J2.27, J4.27, J6.14
/~RAMWE3: J2.26, J4.26, J6.15
/~RAMWE4: J2.25, J4.25, J6.16
/~RAMWE5: J2.24, J4.24, J6.17
/~RAMWE6: J2.23, J4.23, J6.18
/~RAMWE7: J2.22, J4.22, J6.19
/~RAMWE8: J2.21, J4.21, J6.20
/~RAMWE9: J2.20, J4.20, J6.21
/~RAMWE10: J2.19, J4.19, J6.22
/~RAMWE11: J2.18, J4.18, J6.23
/~RAMWE12: J2.17, J4.17, J6.24
/~RAMWE13: J2.16, J4.16, J6.25
/~RST: J1.18, J3.18, J5.18
/~extCS: J14.1, JP3.2 (C), JP4.2 (C), U1.19 (CE), U2.19 (CE), U4.19 (CE)
GND: C4.2, C5.2, J1.39, J1.40, J2.39, J2.40, J3.39, J3.40, J4.39, J4.40, J5.39, J5.40, J6.1, J6.2, J10.1, J10.2, J10.3, J10.4, J10.5, J10.6, JP4.1 (A), JP5.1 (A), U1.10 (GND), U2.10 (GND), U4.10 (GND)
unnamed: J11.1, U1.18 (B0)
unnamed: J11.2, U1.17 (B1)
unnamed: J11.3, U1.16 (B2)
unnamed: J12.1, U1.2 (A0)
unnamed: J12.2, U1.3 (A1)
unnamed: J12.3, U1.4 (A2)
unnamed: JP1.2 (C), JP3.1 (A)

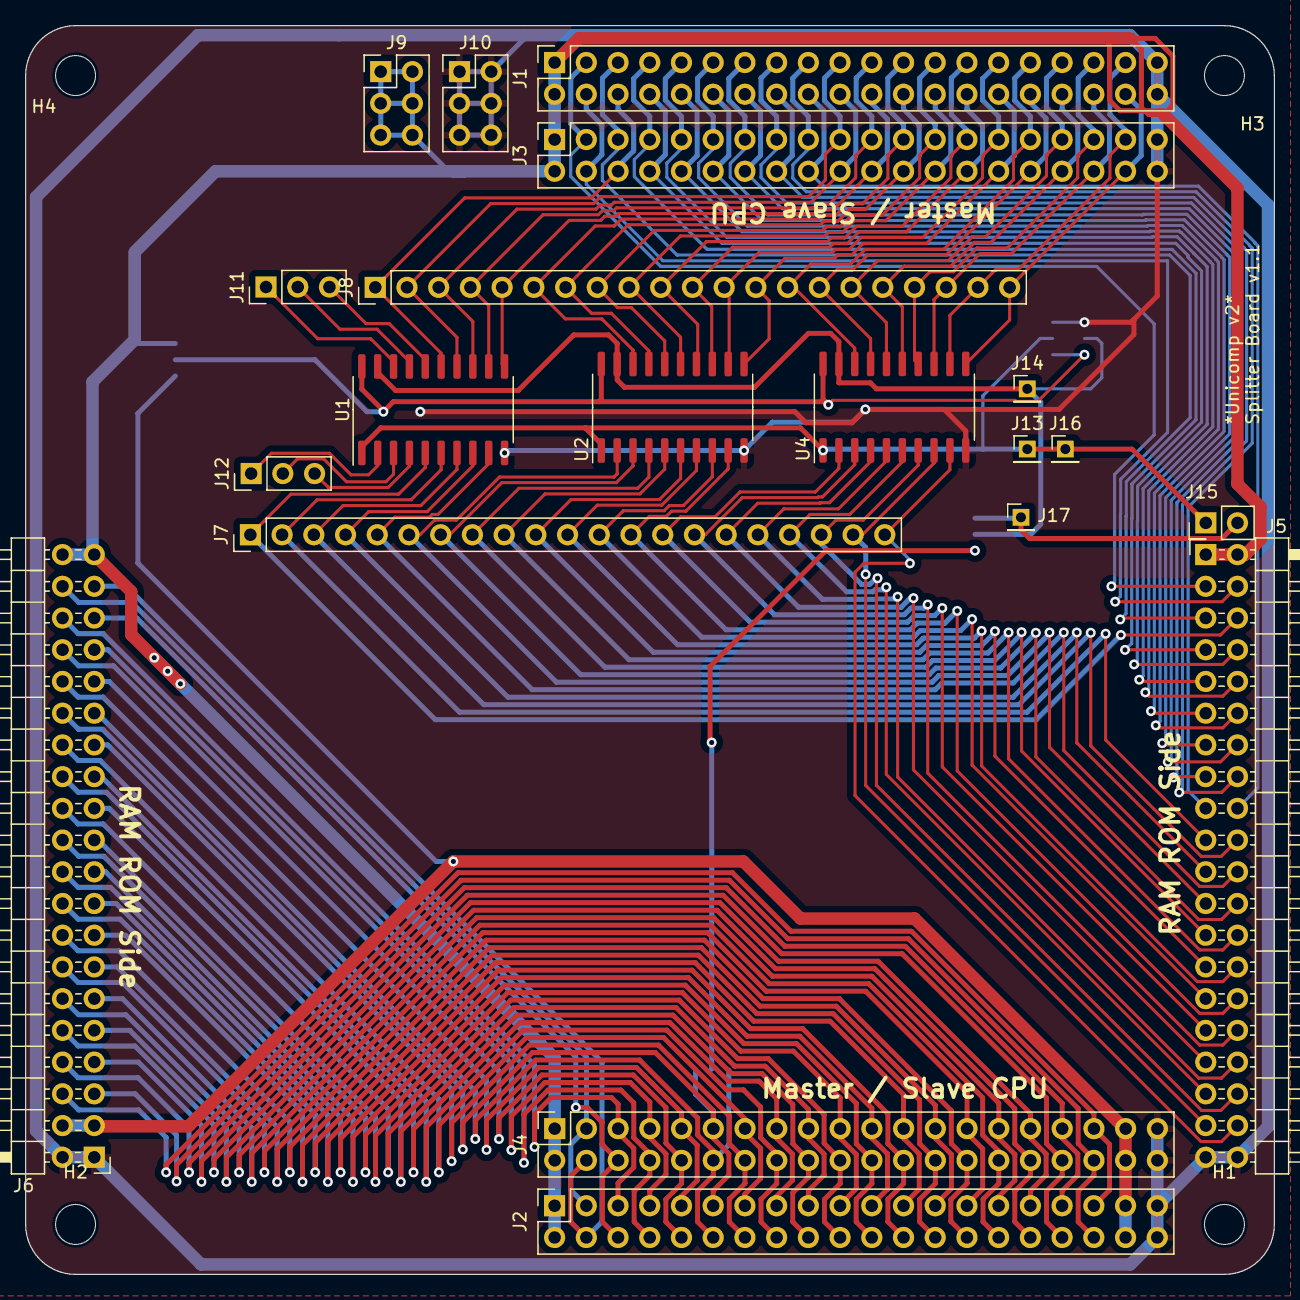
[picture p90: board SplitterBoard.kicad_pcb from above]

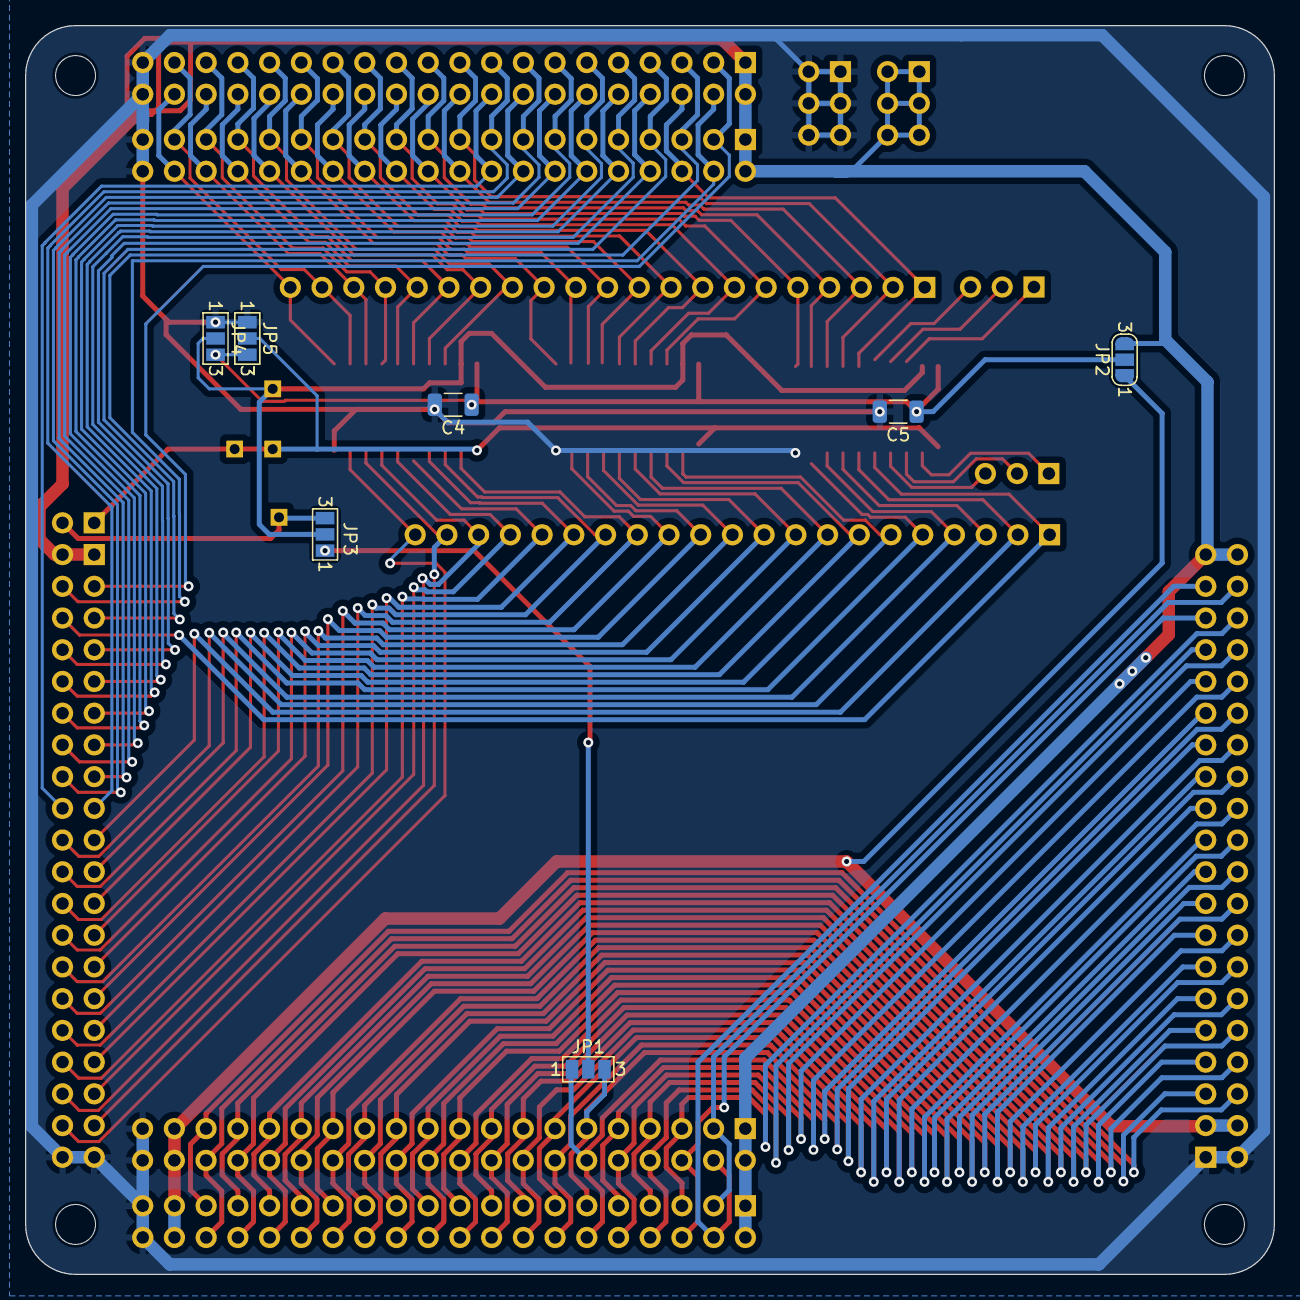
[picture p91: board SplitterBoard.kicad_pcb from below]

Board: 2 copper layers, 100.0 x 100.0 mm, 31 parts (7 on the bottom side), 105 nets.
