roberto314/Unicomp2/RAMROM_512k_board/RAMROM_512k_board.kicad_pcb

## KiCad design RAMROM_512k_board/RAMROM_512k_board.kicad_pcb (2023-08-06)

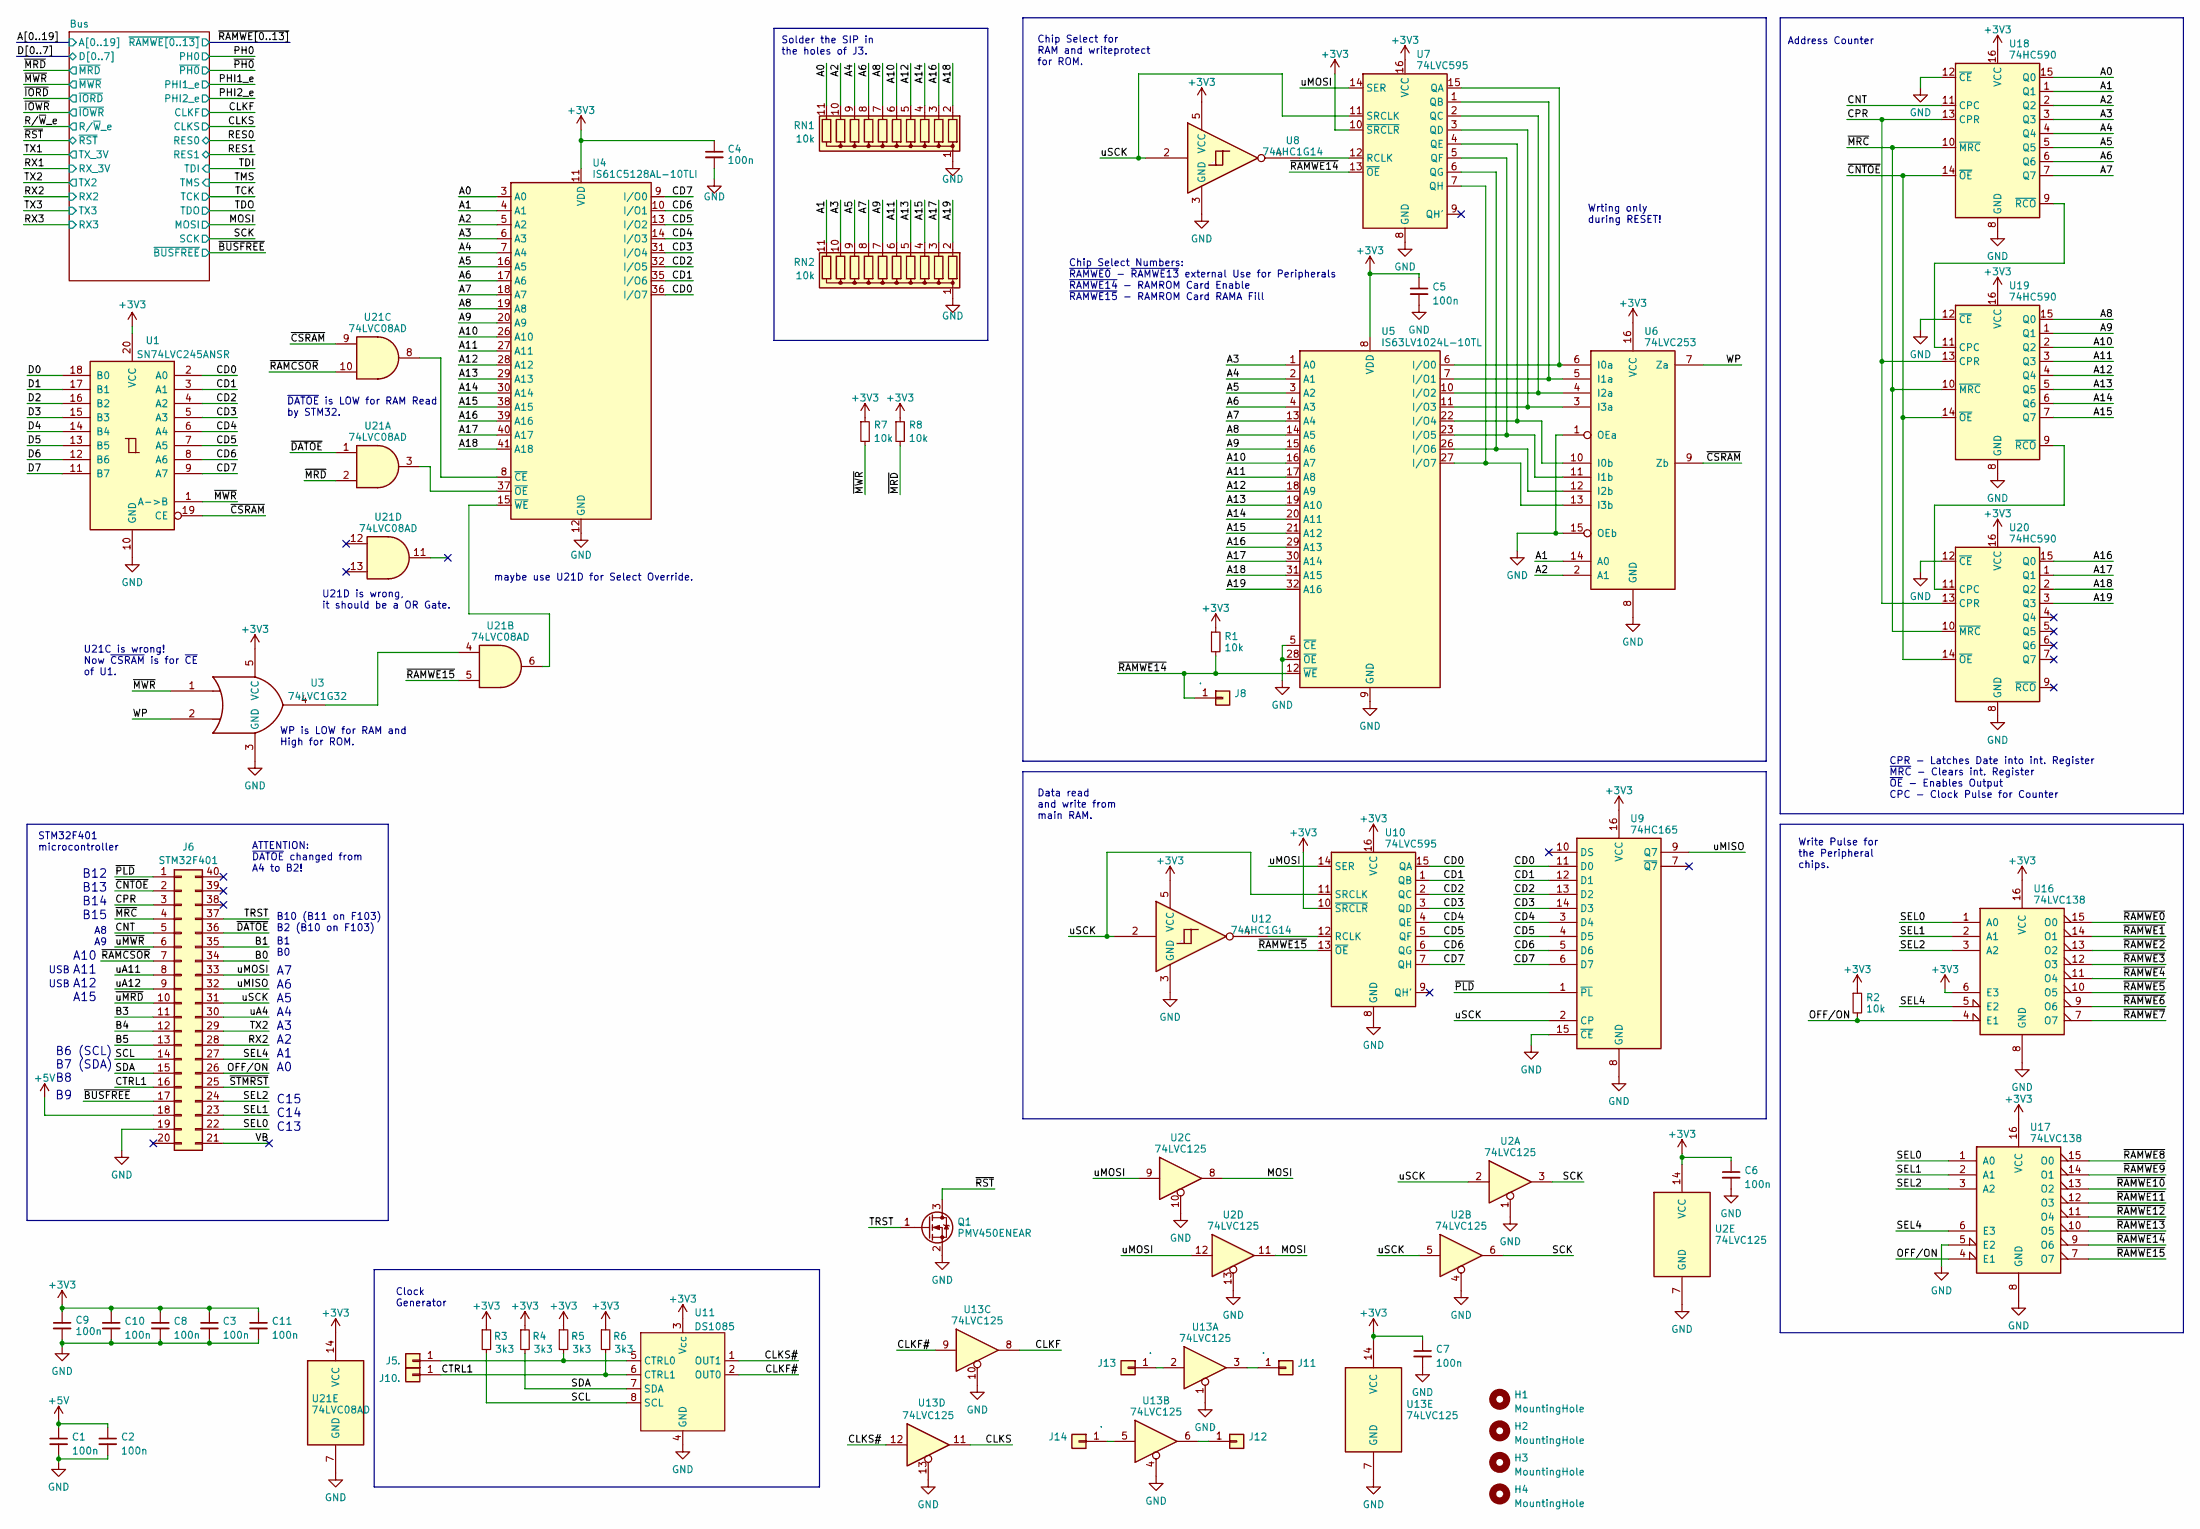
[picture p92: schematic RAMROM_512k_board.kicad_sch, Unicomp v2 - RAMROM Board]

Parts:
C1, C2, C3, C4, C5, C6, C7, C8, C9, C10, C11: 100n; C_1206_3216Metric
H1, H2, H3, H4: MountingHole; MountingHole_3.2mm_M3
J5, J8, J10, J11, J12, J13, J14: .; PinHeader_1x01_P2.00mm_Vertical
J6: STM32F401; DIP-40_W15.24mm_Socket_LongPads
Q1: PMV450ENEAR; SOT-23
R1, R2: 10k; R_1206_3216Metric_Pad1.30x1.75mm_HandSolder
R3, R4, R5, R6: 3k3; R_1206_3216Metric
R7, R8: 10k; R_1206_3216Metric
RN1, RN2: 10k; R_Array_SIP11
U1: SN74LVC245ANSR; SO-20_5.3x12.6mm_P1.27mm
U2, U13: 74LVC125; SOIC-14_3.9x8.7mm_P1.27mm
U3: 74LVC1G32; SOT-23-5_HandSoldering
U4: IS61C5128AL-10TLI; TSOP-II-44_10.16x18.41mm_P0.8mm
U5: IS63LV1024L-10TL; TSOP-II-32_21.0x10.2mm_P1.27mm
U6: 74LVC253; SO-16_3.9x9.9mm_P1.27mm
U7, U10: 74LVC595; SO-16_3.9x9.9mm_P1.27mm
U8, U12: 74AHC1G14; SOT-23-5
U9: 74HC165; SOIC-16_3.9x9.9mm_P1.27mm
U11: DS1085; SOIC-8_3.9x4.9mm_P1.27mm
U16, U17: 74LVC138; SOIC-16_3.9x9.9mm_P1.27mm
U18, U19, U20: 74HC590; SOIC-16_3.9x9.9mm_P1.27mm
U21: 74LVC08AD; SOIC-14_3.9x8.7mm_P1.27mm

Connections:
+3V3: C3.1, C4.1, C5.1, C6.1, C7.1, C8.1, C9.1, C10.1, C11.1, R1.1, R2.1, R3.1, R4.1, R5.1, R6.1, R7.1, R8.1, U1.20 (VCC), U2.14 (VCC), U3.5 (VCC), U4.11 (VDD), U4.33 (VDD), U5.8 (VDD), U5.24 (VDD), U6.16 (VCC), U7.10 (~SRCLR), U7.16 (VCC), U8.5 (VCC), U9.16 (VCC), U10.10 (~SRCLR), U10.16 (VCC), U11.3 (Vcc), U12.5 (VCC), U13.14 (VCC), U16.6 (E3), U16.16 (VCC), U17.16 (VCC), U18.16 (VCC), U19.16 (VCC), U20.16 (VCC), U21.14 (VCC); also elsewhere on the board
+5V: C1.1, C2.1, J6.18; also elsewhere on the board
/A0: RN1.11 (R10), U4.3 (A0), U18.15 (Q0); also elsewhere on the board
/A1: RN2.11 (R10), U4.4 (A1), U6.14 (A0), U18.1 (Q1); also elsewhere on the board
/A2: RN1.10 (R9), U4.5 (A2), U6.2 (A1), U18.2 (Q2); also elsewhere on the board
/A3: RN2.10 (R9), U4.6 (A3), U5.1 (A0), U18.3 (Q3); also elsewhere on the board
/A4: RN1.9 (R8), U4.7 (A4), U5.2 (A1), U18.4 (Q4); also elsewhere on the board
/A5: RN2.9 (R8), U4.16 (A5), U5.3 (A2), U18.5 (Q5); also elsewhere on the board
/A6: RN1.8 (R7), U4.17 (A6), U5.4 (A3), U18.6 (Q6); also elsewhere on the board
/A7: RN2.8 (R7), U4.18 (A7), U5.13 (A4), U18.7 (Q7); also elsewhere on the board
/A8: RN1.7 (R6), U4.19 (A8), U5.14 (A5), U19.15 (Q0); also elsewhere on the board
/A9: RN2.7 (R6), U4.20 (A9), U5.15 (A6), U19.1 (Q1); also elsewhere on the board
/A10: RN1.6 (R5), U4.26 (A10), U5.16 (A7), U19.2 (Q2); also elsewhere on the board
/A11: RN2.6 (R5), U4.27 (A11), U5.17 (A8), U19.3 (Q3); also elsewhere on the board
/A12: RN1.5 (R4), U4.28 (A12), U5.18 (A9), U19.4 (Q4); also elsewhere on the board
/A13: RN2.5 (R4), U4.29 (A13), U5.19 (A10), U19.5 (Q5); also elsewhere on the board
/A14: RN1.4 (R3), U4.30 (A14), U5.20 (A11), U19.6 (Q6); also elsewhere on the board
/A15: RN2.4 (R3), U4.38 (A15), U5.21 (A12), U19.7 (Q7); also elsewhere on the board
/A16: RN1.3 (R2), U4.39 (A16), U5.29 (A13), U20.15 (Q0); also elsewhere on the board
/A17: RN2.3 (R2), U4.40 (A17), U5.30 (A14), U20.1 (Q1); also elsewhere on the board
/A18: RN1.2 (R1), U4.41 (A18), U5.31 (A15), U20.2 (Q2); also elsewhere on the board
/A19: RN2.2 (R1), U5.32 (A16), U20.3 (Q3); also elsewhere on the board
/B0: J6.34
/B1: J6.35
/B3: J6.11
/B4: J6.12
/B5: J6.13
/CD0: U1.2 (A0), U4.36 (I/O7), U9.11 (D0), U10.15 (QA)
/CD1: U1.3 (A1), U4.35 (I/O6), U9.12 (D1), U10.1 (QB)
/CD2: U1.4 (A2), U4.32 (I/O5), U9.13 (D2), U10.2 (QC)
/CD3: U1.5 (A3), U4.31 (I/O4), U9.14 (D3), U10.3 (QD)
/CD4: U1.6 (A4), U4.14 (I/O3), U9.3 (D4), U10.4 (QE)
/CD5: U1.7 (A5), U4.13 (I/O2), U9.4 (D5), U10.5 (QF)
/CD6: U1.8 (A6), U4.10 (I/O1), U9.5 (D6), U10.6 (QG)
/CD7: U1.9 (A7), U4.9 (I/O0), U9.6 (D7), U10.7 (QH)
/CLKF: U13.8; also elsewhere on the board
/CLKF#: U11.2 (OUT0), U13.9
/CLKS: U13.11; also elsewhere on the board
/CLKS#: U11.1 (OUT1), U13.12
/CNT: J6.5, U18.11 (CPC)
/CPR: J6.3, U18.13 (CPR), U19.13 (CPR), U20.13 (CPR)
/CTRL1: J6.16, J10.1, R6.2, U11.6 (CTRL1)
/D0: U1.18 (B0); also elsewhere on the board
/D1: U1.17 (B1); also elsewhere on the board
/D2: U1.16 (B2); also elsewhere on the board
/D3: U1.15 (B3); also elsewhere on the board
/D4: U1.14 (B4); also elsewhere on the board
/D5: U1.13 (B5); also elsewhere on the board
/D6: U1.12 (B6); also elsewhere on the board
/D7: U1.11 (B7); also elsewhere on the board
/MOSI: U2.8, U2.11; also elsewhere on the board
/OFF/ON: J6.26, R2.2, U16.4 (E1), U17.4 (E1)
/RX2: J6.28; also elsewhere on the board
/SCK: U2.3, U2.6; also elsewhere on the board
/SCL: J6.14, R3.2, U11.8 (SCL)
/SDA: J6.15, R4.2, U11.7 (SDA)
/SEL0: J6.22, U16.1 (A0), U17.1 (A0)
/SEL1: J6.23, U16.2 (A1), U17.2 (A1)
/SEL2: J6.24, U16.3 (A2), U17.3 (A2)
/SEL4: J6.27, U16.5 (E2), U17.6 (E3)
/TRST: J6.37, Q1.1 (G)
/TX2: J6.29; also elsewhere on the board
/VB: J6.21
/WP: U3.2, U6.7 (Za)
/uA4: J6.30
/uA11: J6.8
/uA12: J6.9
/uMISO: J6.32, U9.9 (Q7)
/uMOSI: J6.33, U2.9, U2.12, U7.14 (SER), U10.14 (SER)
/uSCK: J6.31, U2.2, U2.5, U7.11 (SRCLK), U8.2, U9.2 (CP), U10.11 (SRCLK), U12.2
/~BUSFREE: J6.17; also elsewhere on the board
/~CNTOE: J6.2, U18.14 (~OE), U19.14 (~OE), U20.14 (~OE)
/~CSRAM: U1.19 (CE), U6.9 (Zb), U21.9
/~DATOE: J6.36, U21.1
/~MRC: J6.4, U18.10 (~MRC), U19.10 (~MRC), U20.10 (~MRC)
/~MRD: R8.2, U21.2; also elsewhere on the board
/~MWR: R7.2, U1.1 (A->B), U3.1; also elsewhere on the board
/~PLD: J6.1, U9.1 (~PL)
/~RAMCSOR: J6.7, U21.10
/~RAMWE0: U16.15 (O0); also elsewhere on the board
/~RAMWE1: U16.14 (O1); also elsewhere on the board
/~RAMWE2: U16.13 (O2); also elsewhere on the board
/~RAMWE3: U16.12 (O3); also elsewhere on the board
/~RAMWE4: U16.11 (O4); also elsewhere on the board
/~RAMWE5: U16.10 (O5); also elsewhere on the board
/~RAMWE6: U16.9 (O6); also elsewhere on the board
/~RAMWE7: U16.7 (O7); also elsewhere on the board
/~RAMWE8: U17.15 (O0); also elsewhere on the board
/~RAMWE9: U17.14 (O1); also elsewhere on the board
/~RAMWE10: U17.13 (O2); also elsewhere on the board
/~RAMWE11: U17.12 (O3); also elsewhere on the board
/~RAMWE12: U17.11 (O4); also elsewhere on the board
/~RAMWE13: U17.10 (O5); also elsewhere on the board
/~RAMWE14: J8.1, R1.2, U5.12 (~WE), U7.13 (~OE), U17.9 (O6)
/~RAMWE15: U10.13 (~OE), U17.7 (O7), U21.5
/~RST: Q1.3 (D); also elsewhere on the board
/~STMRST: J6.25
/~uMRD: J6.10
/~uMWR: J6.6
GND: C1.2, C2.2, C3.2, C4.2, C5.2, C6.2, C7.2, C8.2, C9.2, C10.2, C11.2, J6.19, Q1.2 (S), RN1.1 (common), RN2.1 (common), U1.10 (GND), U2.1, U2.4, U2.7 (GND), U2.10, U2.13, U3.3 (GND), U4.12 (GND), U4.34 (GND), U5.5 (~CE), U5.9 (GND), U5.25 (GND), U5.28 (~OE), U6.1 (OEa), U6.8 (GND), U6.15 (OEb), U7.8 (GND), U8.3 (GND), U9.8 (GND), U9.15 (~CE), U10.8 (GND), U11.4 (GND), U12.3 (GND), U13.1, U13.4, U13.7 (GND), U13.10, U13.13, U16.8 (GND), U17.5 (E2), U17.8 (GND), U18.8 (GND), U18.12 (~CE), U19.8 (GND), U19.12 (~CE), U20.8 (GND), U20.12 (~CE), U21.7 (GND); also elsewhere on the board
unnamed: J5.1, R5.2, U11.5 (CTRL0)
unnamed: J11.1, U13.3
unnamed: J12.1, U13.6
unnamed: J13.1, U13.2
unnamed: J14.1, U13.5
unnamed: U4.8 (~CE), U21.8
unnamed: U4.37 (~OE), U21.3
unnamed: U4.15 (~WE), U21.6
unnamed: U5.6 (I/O0), U6.6 (I0a), U7.15 (QA)
unnamed: U5.7 (I/O1), U6.5 (I1a), U7.1 (QB)
unnamed: U5.10 (I/O2), U6.4 (I2a), U7.2 (QC)
unnamed: U5.11 (I/O3), U6.3 (I3a), U7.3 (QD)
unnamed: U5.22 (I/O4), U6.10 (I0b), U7.4 (QE)
unnamed: U5.23 (I/O5), U6.11 (I1b), U7.5 (QF)
unnamed: U5.26 (I/O6), U6.12 (I2b), U7.6 (QG)
unnamed: U5.27 (I/O7), U6.13 (I3b), U7.7 (QH)
unnamed: U7.12 (RCLK), U8.4
unnamed: U10.12 (RCLK), U12.4
unnamed: U18.9 (~RCO), U19.11 (CPC)
unnamed: U19.9 (~RCO), U20.11 (CPC)
unnamed: U3.4, U21.4

Notes on the sheet:
USB
B1 B0
B6 (SCL) B7 (SDA) B8
Chip Select for RAM and writeprotect for ROM.
U21C is wrong! Now ~{CSRAM} is for ~{CE} of U1.
Data read and write from main RAM.
A10 A11 A12 A15
ATTENTION: ~{DATOE} changed from A4 to B2!
U21D is wrong, it should be a OR Gate.
CPR - Latches Date into int. Register ~{MRC} - Clears int. Register ~{OE} - Enables Output CPC - Clock Pulse for Counter
Wrting only during RESET!
WP is LOW for RAM and High for ROM.
Write Pulse for the Peripheral chips.
A8 A9
B10 (B11 on F103) B2 (B10 on F103)
~{DATOE} is LOW for RAM Read by STM32.
A7 A6 A5 A4 A3 A2 A1 A0
Clock Generator
maybe use U21D for Select Override.
Solder the SIP in the holes of J3.
B12 B13 B14 B15
C15 C14 C13
STM32F401 microcontroller
Address Counter
Chip Select Numbers: ~{RAMWE0} - ~{RAMWE13} external Use for Peripherals ~{RAMWE14} - RAMROM Card Enable ~{RAMWE15} - RAMROM Card RAMA Fill
