roberto314/Unicomp2/RAMROM_512k_board/RAMROM_512k_board.kicad_pcb

## KiCad design RAMROM_512k_board/RAMROM_512k_board.kicad_pcb (continued)

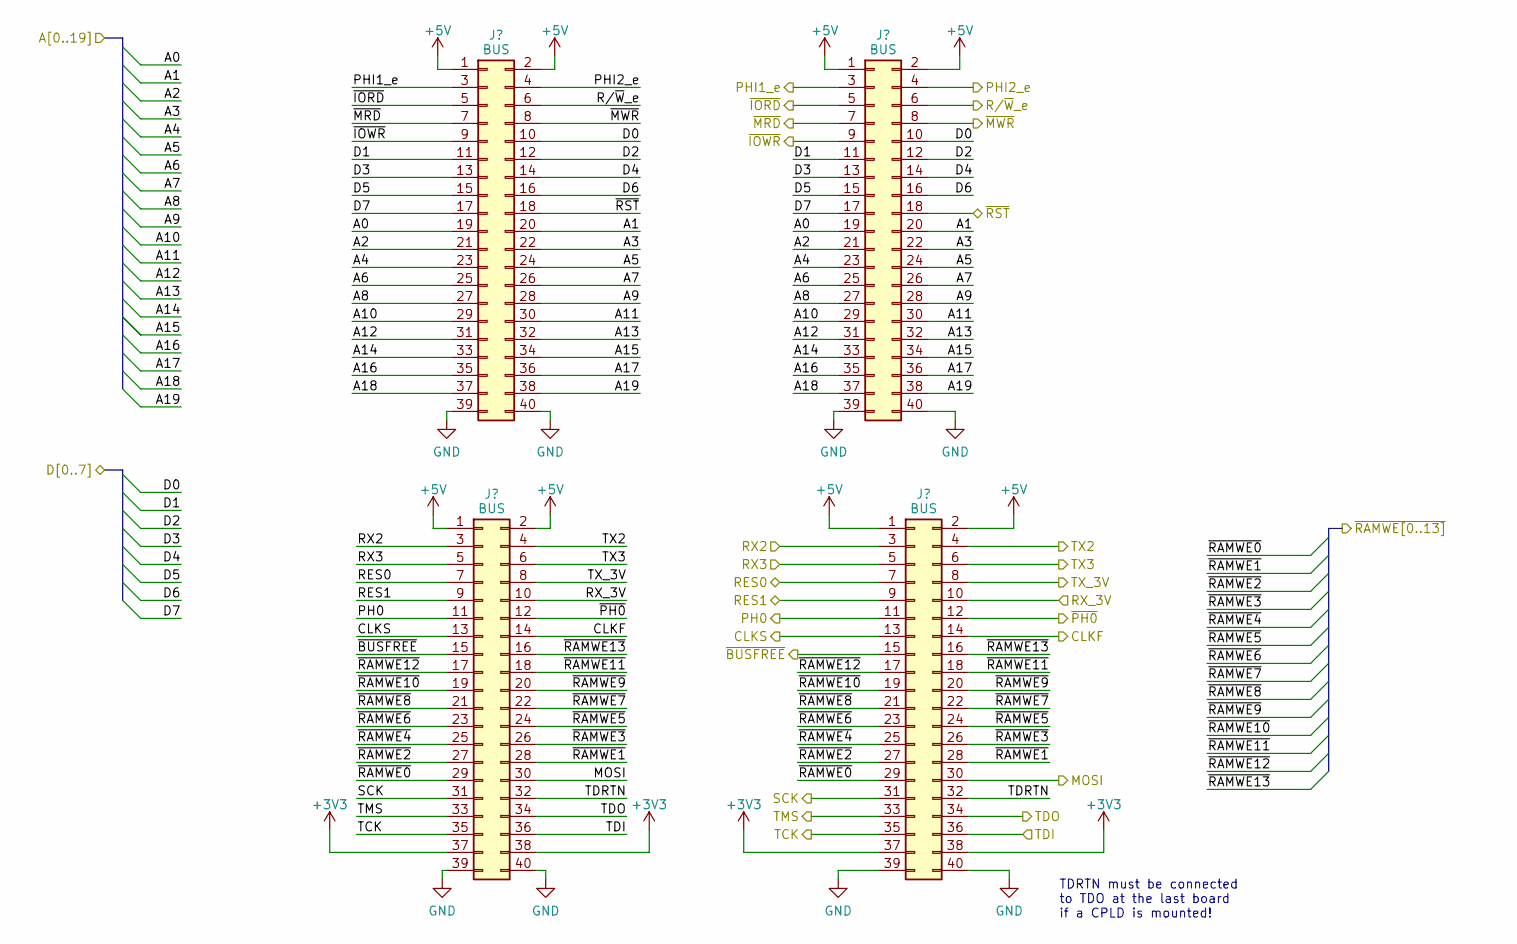
[picture p93: schematic bus.kicad_sch, Unicomp v2 - RAMROM Board]

Parts:
J1, J2, J3, J4: BUS; PinSocket_2x20_P2.54mm_Vertical

Connections:
+3V3: J2.37, J2.38, J4.37, J4.38; also elsewhere on the board
+5V: J1.1, J1.2, J2.1, J2.2, J3.1, J3.2, J4.1, J4.2; also elsewhere on the board
/A0: J1.19, J3.19; also elsewhere on the board
/A1: J1.20, J3.20; also elsewhere on the board
/A2: J1.21, J3.21; also elsewhere on the board
/A3: J1.22, J3.22; also elsewhere on the board
/A4: J1.23, J3.23; also elsewhere on the board
/A5: J1.24, J3.24; also elsewhere on the board
/A6: J1.25, J3.25; also elsewhere on the board
/A7: J1.26, J3.26; also elsewhere on the board
/A8: J1.27, J3.27; also elsewhere on the board
/A9: J1.28, J3.28; also elsewhere on the board
/A10: J1.29, J3.29; also elsewhere on the board
/A11: J1.30, J3.30; also elsewhere on the board
/A12: J1.31, J3.31; also elsewhere on the board
/A13: J1.32, J3.32; also elsewhere on the board
/A14: J1.33, J3.33; also elsewhere on the board
/A15: J1.34, J3.34; also elsewhere on the board
/A16: J1.35, J3.35; also elsewhere on the board
/A17: J1.36, J3.36; also elsewhere on the board
/A18: J1.37, J3.37; also elsewhere on the board
/A19: J1.38, J3.38; also elsewhere on the board
/Bus/TDRTN: J2.32, J4.32
/CLKF: J2.14, J4.14; also elsewhere on the board
/CLKS: J2.13, J4.13; also elsewhere on the board
/D0: J1.10, J3.10; also elsewhere on the board
/D1: J1.11, J3.11; also elsewhere on the board
/D2: J1.12, J3.12; also elsewhere on the board
/D3: J1.13, J3.13; also elsewhere on the board
/D4: J1.14, J3.14; also elsewhere on the board
/D5: J1.15, J3.15; also elsewhere on the board
/D6: J1.16, J3.16; also elsewhere on the board
/D7: J1.17, J3.17; also elsewhere on the board
/MOSI: J2.30, J4.30; also elsewhere on the board
/PH0: J2.11, J4.11
/PHI1_e: J1.3, J3.3
/PHI2_e: J1.4, J3.4
/RES0: J2.7, J4.7
/RES1: J2.9, J4.9
/RX1: J2.10, J4.10
/RX2: J2.3, J4.3; also elsewhere on the board
/RX3: J2.5, J4.5
/R/~W_e: J1.6, J3.6
/SCK: J2.31, J4.31; also elsewhere on the board
/TCK: J2.35, J4.35
/TDI: J2.36, J4.36
/TDO: J2.34, J4.34
/TMS: J2.33, J4.33
/TX1: J2.8, J4.8
/TX2: J2.4, J4.4; also elsewhere on the board
/TX3: J2.6, J4.6
/~BUSFREE: J2.15, J4.15; also elsewhere on the board
/~IORD: J1.5, J3.5
/~IOWR: J1.9, J3.9
/~MRD: J1.7, J3.7; also elsewhere on the board
/~MWR: J1.8, J3.8; also elsewhere on the board
/~PH0: J2.12, J4.12
/~RAMWE0: J2.29, J4.29; also elsewhere on the board
/~RAMWE1: J2.28, J4.28; also elsewhere on the board
/~RAMWE2: J2.27, J4.27; also elsewhere on the board
/~RAMWE3: J2.26, J4.26; also elsewhere on the board
/~RAMWE4: J2.25, J4.25; also elsewhere on the board
/~RAMWE5: J2.24, J4.24; also elsewhere on the board
/~RAMWE6: J2.23, J4.23; also elsewhere on the board
/~RAMWE7: J2.22, J4.22; also elsewhere on the board
/~RAMWE8: J2.21, J4.21; also elsewhere on the board
/~RAMWE9: J2.20, J4.20; also elsewhere on the board
/~RAMWE10: J2.19, J4.19; also elsewhere on the board
/~RAMWE11: J2.18, J4.18; also elsewhere on the board
/~RAMWE12: J2.17, J4.17; also elsewhere on the board
/~RAMWE13: J2.16, J4.16; also elsewhere on the board
/~RST: J1.18, J3.18; also elsewhere on the board
GND: J1.39, J1.40, J2.39, J2.40, J3.39, J3.40, J4.39, J4.40; also elsewhere on the board

Notes on the sheet:
TDRTN must be connected to TDO at the last board if a CPLD is mounted!

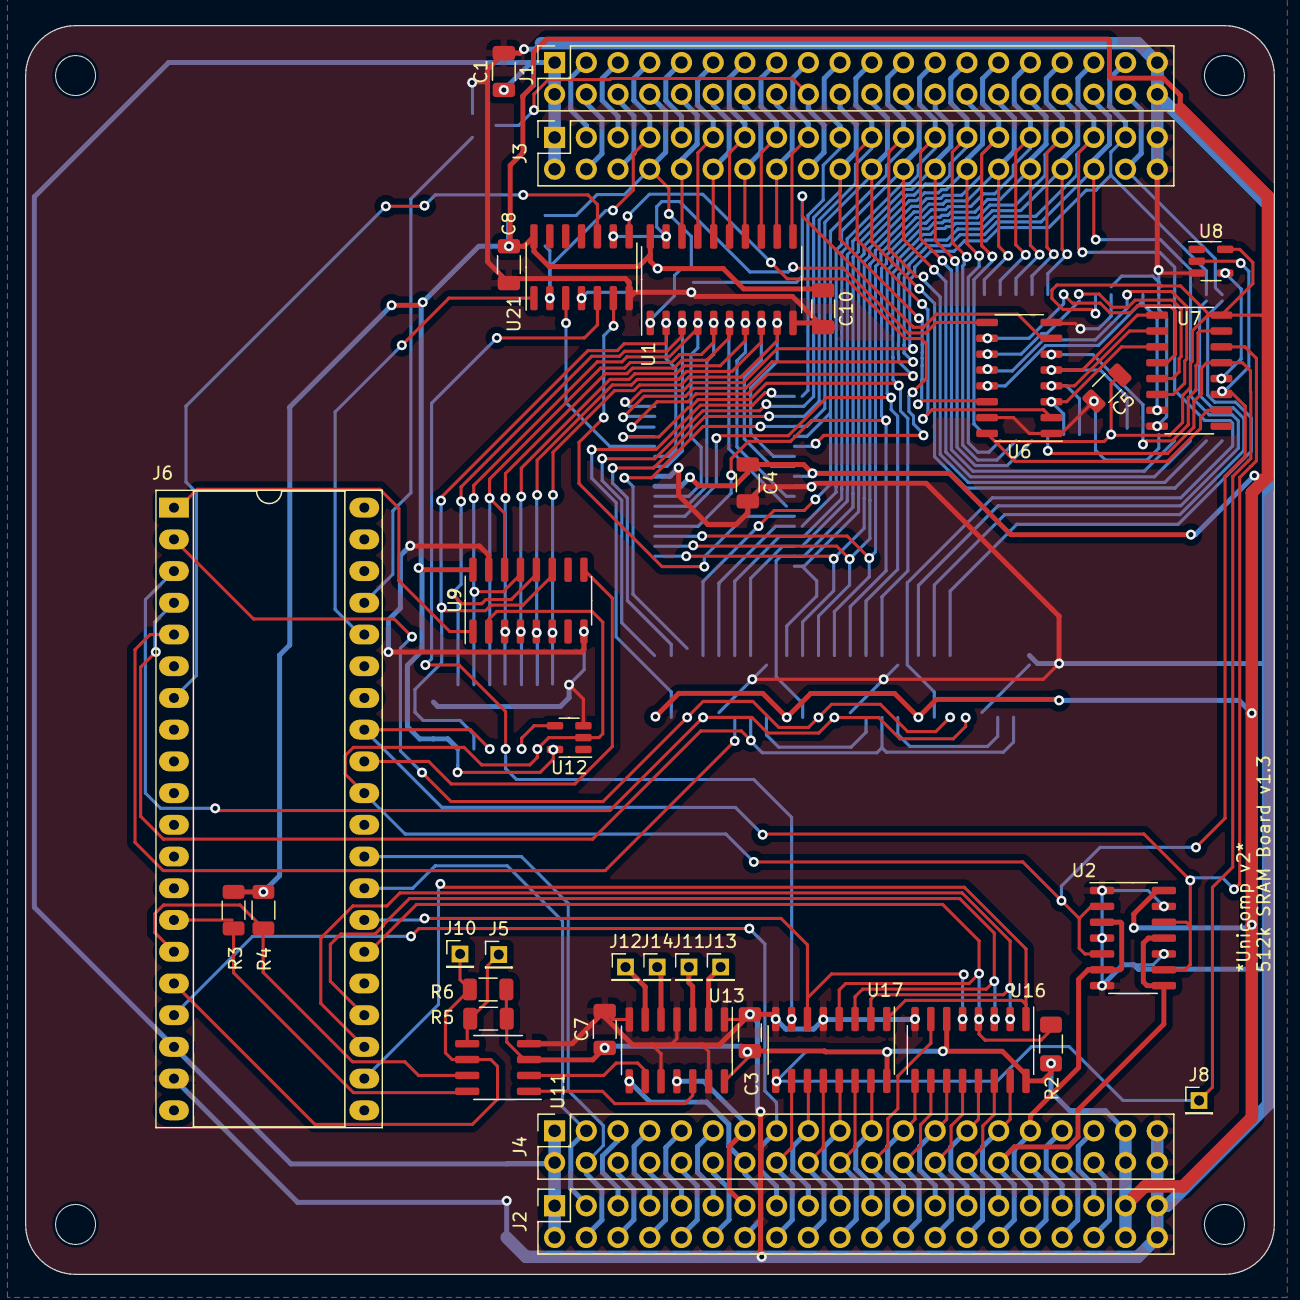
[picture p94: board RAMROM_512k_board.kicad_pcb from above]

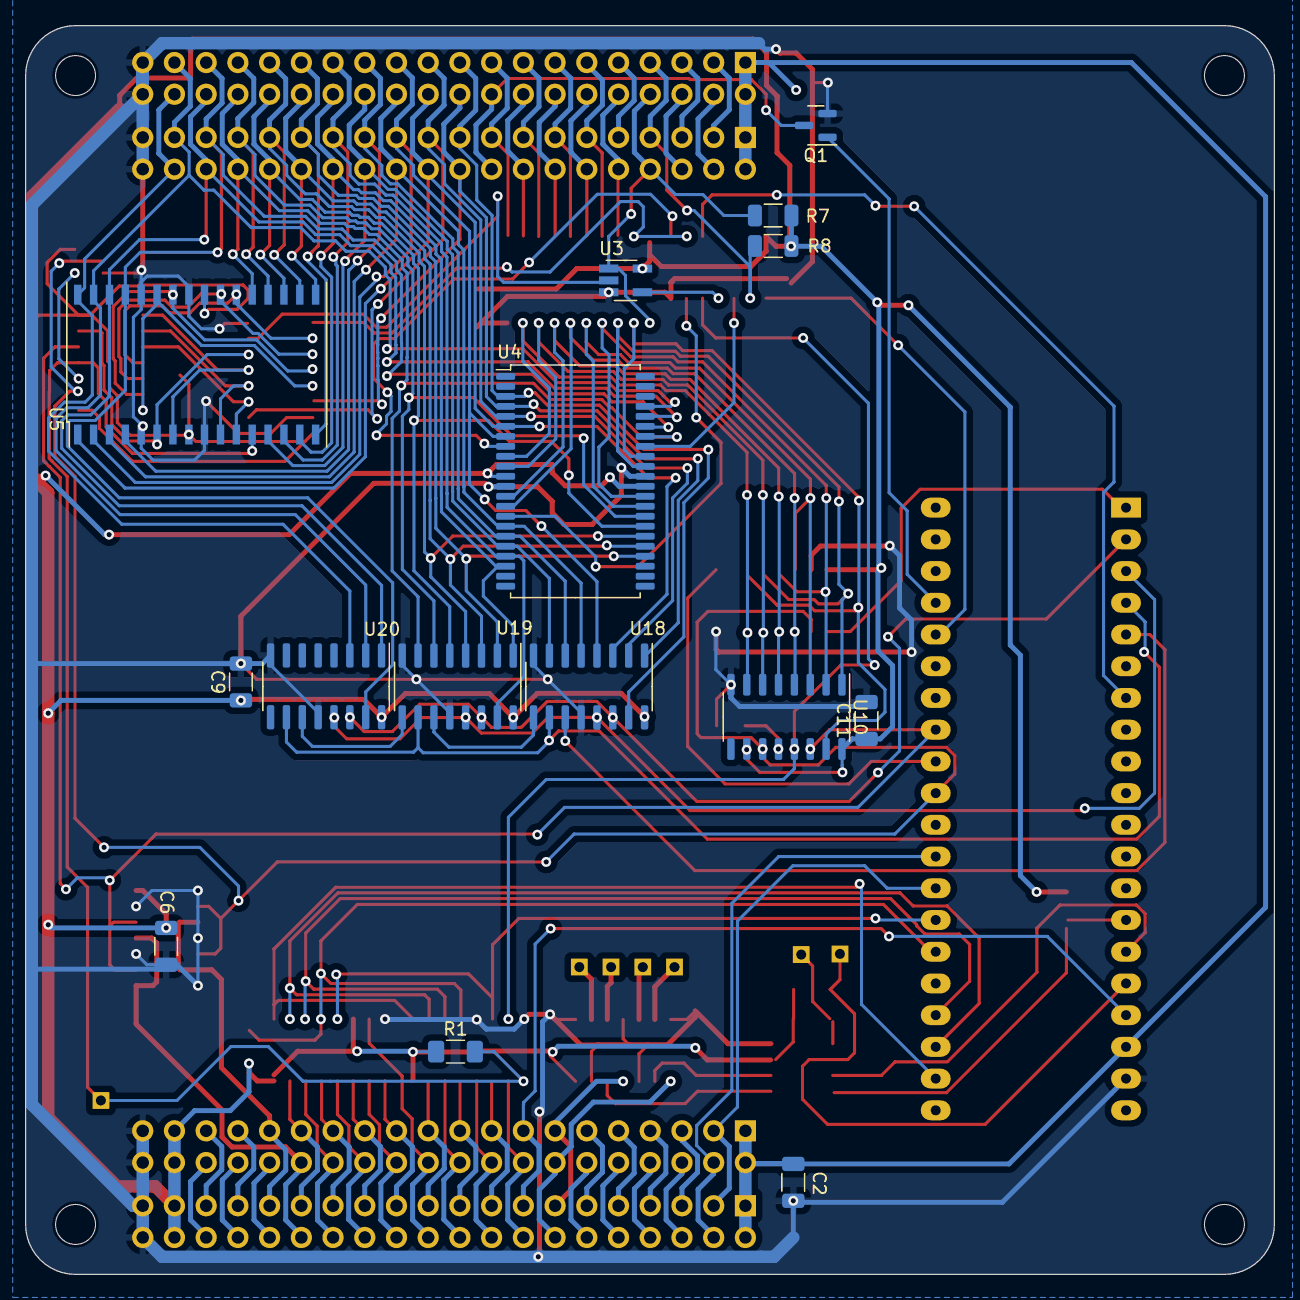
[picture p95: board RAMROM_512k_board.kicad_pcb from below]

Board: 2 copper layers, 100.0 x 100.0 mm, 55 parts (15 on the bottom side), 127 nets.
