roberto314/Unicomp2/not produced boards/RAMROM_CPLD_board/RAMROM_CPLD_board.kicad_pcb

## KiCad design not produced boards/RAMROM_CPLD_board/RAMROM_CPLD_board.kicad_pcb (2023-07-25)

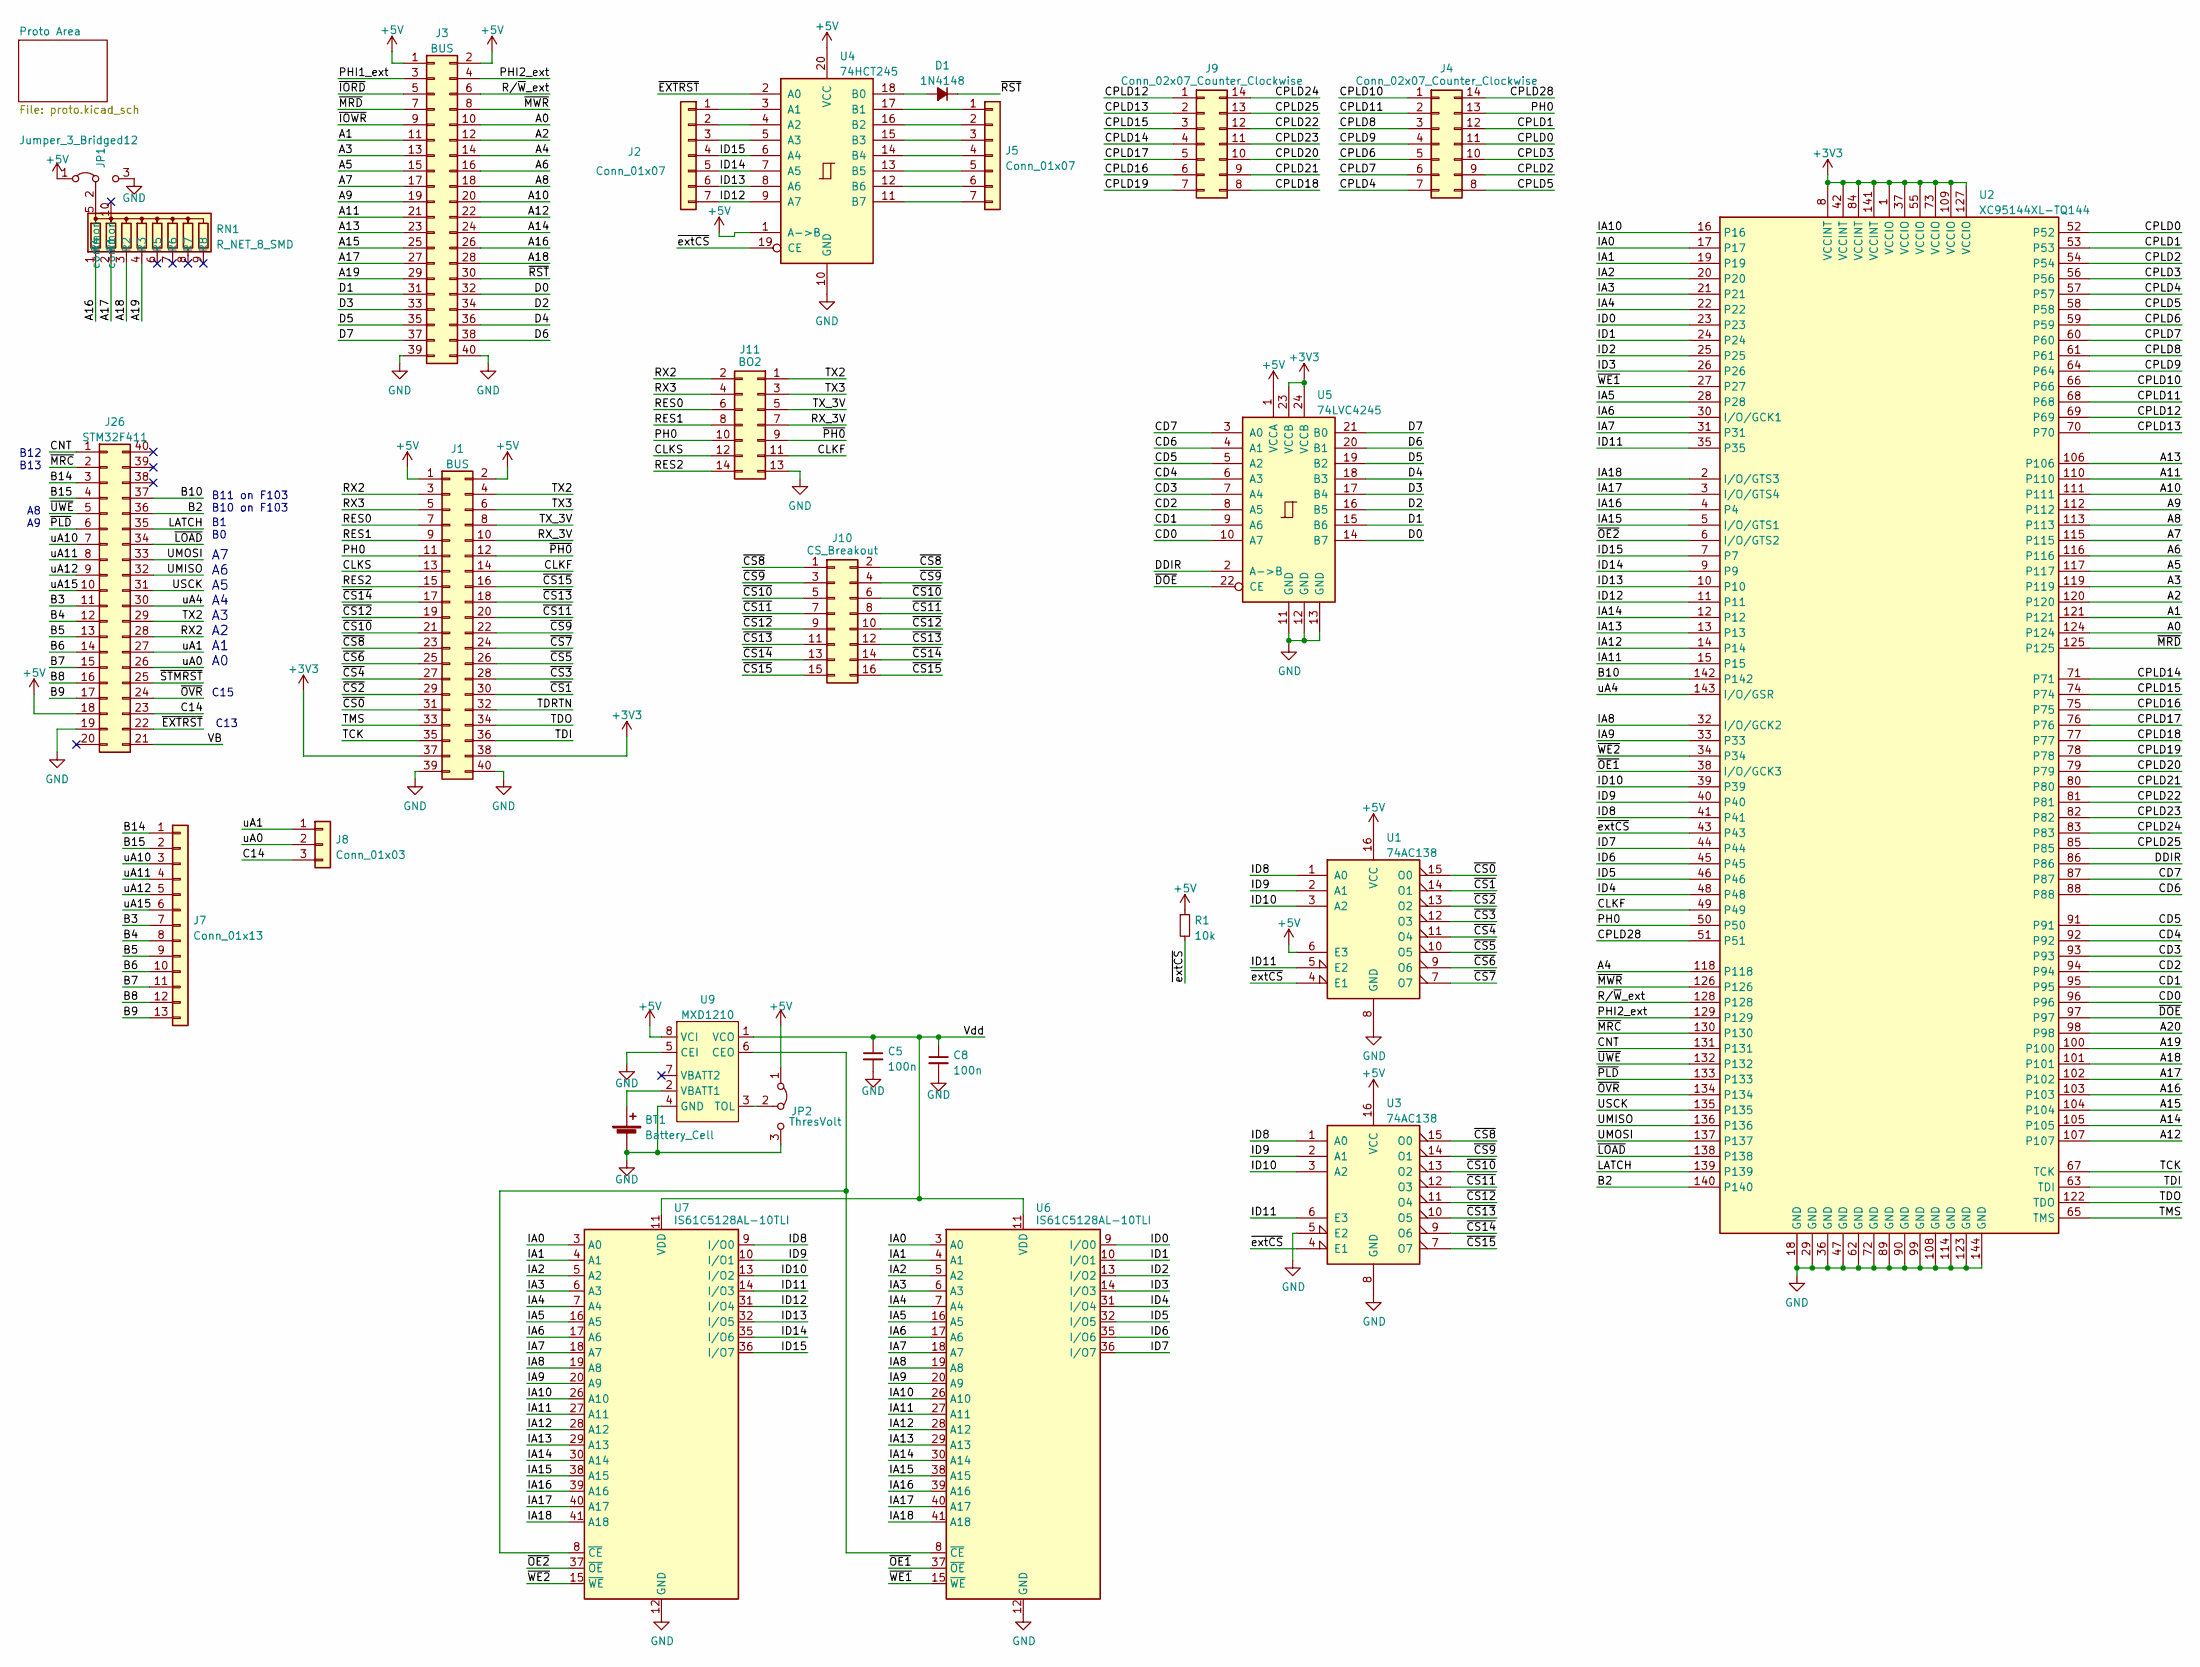
[picture p96: schematic RAMROM_CPLD_board.kicad_sch, Unicomp v2 - RAMROM Board]

Parts:
BT1: Battery_Cell; BatteryHolder_Keystone_103_1x20mm
C5, C8: 100n; C_1206_3216Metric
D1: 1N4148; D_1206_3216Metric_Pad1.42x1.75mm_HandSolder
J1, J3: BUS; PinSocket_2x20_P2.54mm_Vertical
J2, J5: Conn_01x07; PinHeader_1x07_P2.54mm_Vertical
J4, J9: Conn_02x07_Counter_Clockwise; PinHeader_2x07_P2.00mm_Vertical
J7: Conn_01x13; PinHeader_1x13_P2.54mm_Vertical
J8: Conn_01x03; PinHeader_1x03_P2.00mm_Vertical
J10: CS_Breakout; PinHeader_2x08_P2.00mm_Vertical
J11: BO2; PinHeader_2x07_P2.54mm_Vertical
J26: STM32F411; DIP-40_W15.24mm_Socket_LongPads
JP1: Jumper_3_Bridged12; SolderJumper-3_P1.3mm_Bridged12_RoundedPad1.0x1.5mm_NumberL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
JP2: ThresVolt; SolderJumper-3_P1.3mm_Bridged12_RoundedPad1.0x1.5mm_NumberL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
R1: 10k; R_1206_3216Metric
RN1: R_NET_8_SMD; R_Net2512_6.4x3.1_P1.27
U1, U3: 74AC138; TSSOP-16_4.4x5mm_P0.65mm
U2: XC95144XL-TQ144; TQFP-144_20x20mm_P0.5mm
U4: 74HCT245; DIP-20_W7.62mm_Socket_LongPads
U5: 74LVC4245; TSSOP-24_4.4x7.8mm_P0.65mm
U6, U7: IS61C5128AL-10TLI; TSOP-II-44_10.16x18.41mm_P0.8mm
U9: MXD1210; SOP-8_3.9x4.9mm_P1.27mm

Connections:
+3V3: J1.37, J1.38, U2.1 (VCCIO), U2.8 (VCCINT), U2.37 (VCCIO), U2.42 (VCCINT), U2.55 (VCCIO), U2.73 (VCCIO), U2.84 (VCCINT), U2.109 (VCCIO), U2.127 (VCCIO), U2.141 (VCCINT), U5.23 (VCCB), U5.24 (VCCB); also elsewhere on the board
+5V: J1.1, J1.2, J3.1, J3.2, J26.18, JP1.1 (A), JP2.1 (A), R1.1, U1.6 (E3), U1.16 (VCC), U3.16 (VCC), U4.1 (A->B), U4.20 (VCC), U5.1 (VCCA), U9.8 (VCI); also elsewhere on the board
/A0: J3.10, U2.124
/A1: J3.11, U2.121
/A2: J3.12, U2.120
/A3: J3.13, U2.119
/A4: J3.14, U2.118
/A5: J3.15, U2.117
/A6: J3.16, U2.116
/A7: J3.17, U2.115
/A8: J3.18, U2.113
/A9: J3.19, U2.112
/A10: J3.20, U2.111
/A11: J3.21, U2.110
/A12: J3.22, U2.107
/A13: J3.23, U2.106
/A14: J3.24, U2.105
/A15: J3.25, U2.104
/A16: J3.26, RN1.1 (R4), U2.103
/A17: J3.27, RN1.2 (R1), U2.102
/A18: J3.28, RN1.3 (R2), U2.101
/A19: J3.29, RN1.4 (R3), U2.100
/A20: U2.98
/B2: J26.36, U2.140
/B3: J7.7, J26.11
/B4: J7.8, J26.12
/B5: J7.9, J26.13
/B6: J7.10, J26.14
/B7: J7.11, J26.15
/B8: J7.12, J26.16
/B9: J7.13, J26.17
/B10: J26.37, U2.142
/B14: J7.1, J26.3
/B15: J7.2, J26.4
/C14: J8.3, J26.23
/CD0: U2.96, U5.10 (A7)
/CD1: U2.95, U5.9 (A6)
/CD2: U2.94, U5.8 (A5)
/CD3: U2.93, U5.7 (A4)
/CD4: U2.92, U5.6 (A3)
/CD5: U2.91, U5.5 (A2)
/CD6: U2.88, U5.4 (A1)
/CD7: U2.87, U5.3 (A0)
/CLKF: J1.14, J11.11, U2.49
/CLKS: J1.13, J11.12
/CNT: J26.1, U2.131
/CPLD0: J4.11, U2.52
/CPLD1: J4.12, U2.53
/CPLD2: J4.9, U2.54
/CPLD3: J4.10, U2.56
/CPLD4: J4.7, U2.57
/CPLD5: J4.8, U2.58
/CPLD6: J4.5, U2.59
/CPLD7: J4.6, U2.60
/CPLD8: J4.3, U2.61
/CPLD9: J4.4, U2.64
/CPLD10: J4.1, U2.66
/CPLD11: J4.2, U2.68
/CPLD12: J9.1, U2.69
/CPLD13: J9.2, U2.70
/CPLD14: J9.4, U2.71
/CPLD15: J9.3, U2.74
/CPLD16: J9.6, U2.75
/CPLD17: J9.5, U2.76
/CPLD18: J9.8, U2.77
/CPLD19: J9.7, U2.78
/CPLD20: J9.10, U2.79
/CPLD21: J9.9, U2.80
/CPLD22: J9.12, U2.81
/CPLD23: J9.11, U2.82
/CPLD24: J9.14, U2.83
/CPLD25: J9.13, U2.85
/CPLD28: J4.14, U2.51
/D0: J3.32, U5.14 (B7)
/D1: J3.31, U5.15 (B6)
/D2: J3.34, U5.16 (B5)
/D3: J3.33, U5.17 (B4)
/D4: J3.36, U5.18 (B3)
/D5: J3.35, U5.19 (B2)
/D6: J3.38, U5.20 (B1)
/D7: J3.37, U5.21 (B0)
/DDIR: U2.86, U5.2 (A->B)
/IA0: U2.17, U6.3 (A0), U7.3 (A0)
/IA1: U2.19, U6.4 (A1), U7.4 (A1)
/IA2: U2.20, U6.5 (A2), U7.5 (A2)
/IA3: U2.21, U6.6 (A3), U7.6 (A3)
/IA4: U2.22, U6.7 (A4), U7.7 (A4)
/IA5: U2.28, U6.16 (A5), U7.16 (A5)
/IA6: U2.30 (I/O/GCK1), U6.17 (A6), U7.17 (A6)
/IA7: U2.31, U6.18 (A7), U7.18 (A7)
/IA8: U2.32 (I/O/GCK2), U6.19 (A8), U7.19 (A8)
/IA9: U2.33, U6.20 (A9), U7.20 (A9)
/IA10: U2.16, U6.26 (A10), U7.26 (A10)
/IA11: U2.15, U6.27 (A11), U7.27 (A11)
/IA12: U2.14, U6.28 (A12), U7.28 (A12)
/IA13: U2.13, U6.29 (A13), U7.29 (A13)
/IA14: U2.12, U6.30 (A14), U7.30 (A14)
/IA15: U2.5 (I/O/GTS1), U6.38 (A15), U7.38 (A15)
/IA16: U2.4, U6.39 (A16), U7.39 (A16)
/IA17: U2.3 (I/O/GTS4), U6.40 (A17), U7.40 (A17)
/IA18: U2.2 (I/O/GTS3), U6.41 (A18), U7.41 (A18)
/ID0: U2.23, U6.9 (I/O0)
/ID1: U2.24, U6.10 (I/O1)
/ID2: U2.25, U6.13 (I/O2)
/ID3: U2.26, U6.14 (I/O3)
/ID4: U2.48, U6.31 (I/O4)
/ID5: U2.46, U6.32 (I/O5)
/ID6: U2.45, U6.35 (I/O6)
/ID7: U2.44, U6.36 (I/O7)
/ID8: U1.1 (A0), U2.41, U3.1 (A0), U7.9 (I/O0)
/ID9: U1.2 (A1), U2.40, U3.2 (A1), U7.10 (I/O1)
/ID10: U1.3 (A2), U2.39, U3.3 (A2), U7.13 (I/O2)
/ID11: U1.5 (E2), U2.35, U3.6 (E3), U7.14 (I/O3)
/ID12: J2.7, U2.11, U4.9 (A7), U7.31 (I/O4)
/ID13: J2.6, U2.10, U4.8 (A6), U7.32 (I/O5)
/ID14: J2.5, U2.9, U4.7 (A5), U7.35 (I/O6)
/ID15: J2.4, U2.7, U4.6 (A4), U7.36 (I/O7)
/LATCH: J26.35, U2.139
/PH0: J1.11, J4.13, J11.10, U2.50
/PHI1_ext: J3.3
/PHI2_ext: J3.4, U2.129
/RES0: J1.7, J11.6
/RES1: J1.9, J11.8
/RES2: J1.15, J11.14
/RX2: J1.3, J11.2, J26.28
/RX3: J1.5, J11.4
/RX_3V: J1.10, J11.7
/R/~W_ext: J3.6, U2.128
/TCK: J1.35, U2.67 (TCK)
/TDI: J1.36, U2.63 (TDI)
/TDO: J1.34, U2.122 (TDO)
/TDRTN: J1.32
/TMS: J1.33, U2.65 (TMS)
/TX2: J1.4, J11.1, J26.29
/TX3: J1.6, J11.3
/TX_3V: J1.8, J11.5
/UMISO: J26.32, U2.136
/UMOSI: J26.33, U2.137
/USCK: J26.31, U2.135
/VB: J26.21
/Vdd: C5.1, C8.1, U6.11 (VDD), U6.33 (VDD), U7.11 (VDD), U7.33 (VDD), U9.1 (VCO)
/uA0: J8.2, J26.26
/uA1: J8.1, J26.27
/uA4: J26.30, U2.143 (I/O/GSR)
/uA10: J7.3, J26.7
/uA11: J7.4, J26.8
/uA12: J7.5, J26.9
/uA15: J7.6, J26.10
/~CS0: J1.31, U1.15 (O0)
/~CS1: J1.30, U1.14 (O1)
/~CS2: J1.29, U1.13 (O2)
/~CS3: J1.28, U1.12 (O3)
/~CS4: J1.27, U1.11 (O4)
/~CS5: J1.26, U1.10 (O5)
/~CS6: J1.25, U1.9 (O6)
/~CS7: J1.24, U1.7 (O7)
/~CS8: J1.23, J10.1, J10.2, U3.15 (O0)
/~CS9: J1.22, J10.3, J10.4, U3.14 (O1)
/~CS10: J1.21, J10.5, J10.6, U3.13 (O2)
/~CS11: J1.20, J10.7, J10.8, U3.12 (O3)
/~CS12: J1.19, J10.9, J10.10, U3.11 (O4)
/~CS13: J1.18, J10.11, J10.12, U3.10 (O5)
/~CS14: J1.17, J10.13, J10.14, U3.9 (O6)
/~CS15: J1.16, J10.15, J10.16, U3.7 (O7)
/~DOE: U2.97, U5.22 (CE)
/~EXTRST: J26.22, U4.2 (A0)
/~IORD: J3.5
/~IOWR: J3.9
/~LOAD: J26.34, U2.138
/~MRC: J26.2, U2.130
/~MRD: J3.7, U2.125
/~MWR: J3.8, U2.126
/~OE1: U2.38 (I/O/GCK3), U6.37 (~OE)
/~OE2: U2.6 (I/O/GTS2), U7.37 (~OE)
/~OVR: J26.24, U2.134
/~PH0: J1.12, J11.9
/~PLD: J26.6, U2.133
/~RST: D1.1 (K), J3.30
/~STMRST: J26.25
/~UWE: J26.5, U2.132
/~WE1: U2.27, U6.15 (~WE)
/~WE2: U2.34, U7.15 (~WE)
/~extCS: R1.2, U1.4 (E1), U2.43, U3.4 (E1), U4.19 (CE)
GND: BT1.2 (-), C5.2, C8.2, J1.39, J1.40, J3.39, J3.40, J11.13, J26.19, JP1.3 (B), JP2.3 (B), U1.8 (GND), U2.18 (GND), U2.29 (GND), U2.36 (GND), U2.47 (GND), U2.62 (GND), U2.72 (GND), U2.89 (GND), U2.90 (GND), U2.99 (GND), U2.108 (GND), U2.114 (GND), U2.123 (GND), U2.144 (GND), U3.5 (E2), U3.8 (GND), U4.10 (GND), U5.11 (GND), U5.12 (GND), U5.13 (GND), U6.12 (GND), U6.34 (GND), U7.12 (GND), U7.34 (GND), U9.4 (GND), U9.5 (CEI); also elsewhere on the board
unnamed: BT1.1 (+), U9.2 (VBATT1)
unnamed: D1.2 (A), U4.18 (B0)
unnamed: J2.1, U4.3 (A1)
unnamed: J2.2, U4.4 (A2)
unnamed: J2.3, U4.5 (A3)
unnamed: J5.1, U4.17 (B1)
unnamed: J5.2, U4.16 (B2)
unnamed: J5.3, U4.15 (B3)
unnamed: J5.4, U4.14 (B4)
unnamed: J5.5, U4.13 (B5)
unnamed: J5.6, U4.12 (B6)
unnamed: J5.7, U4.11 (B7)
unnamed: JP1.2 (C), RN1.5 (common)
unnamed: JP2.2 (C), U9.3 (TOL)
unnamed: U6.8 (~CE), U7.8 (~CE), U9.6 (CEO)

Notes on the sheet:
C13
B11 on F103 B10 on F103
B12 B13
C15
A7 A6 A5 A4 A3 A2 A1 A0
B1 B0
A8 A9

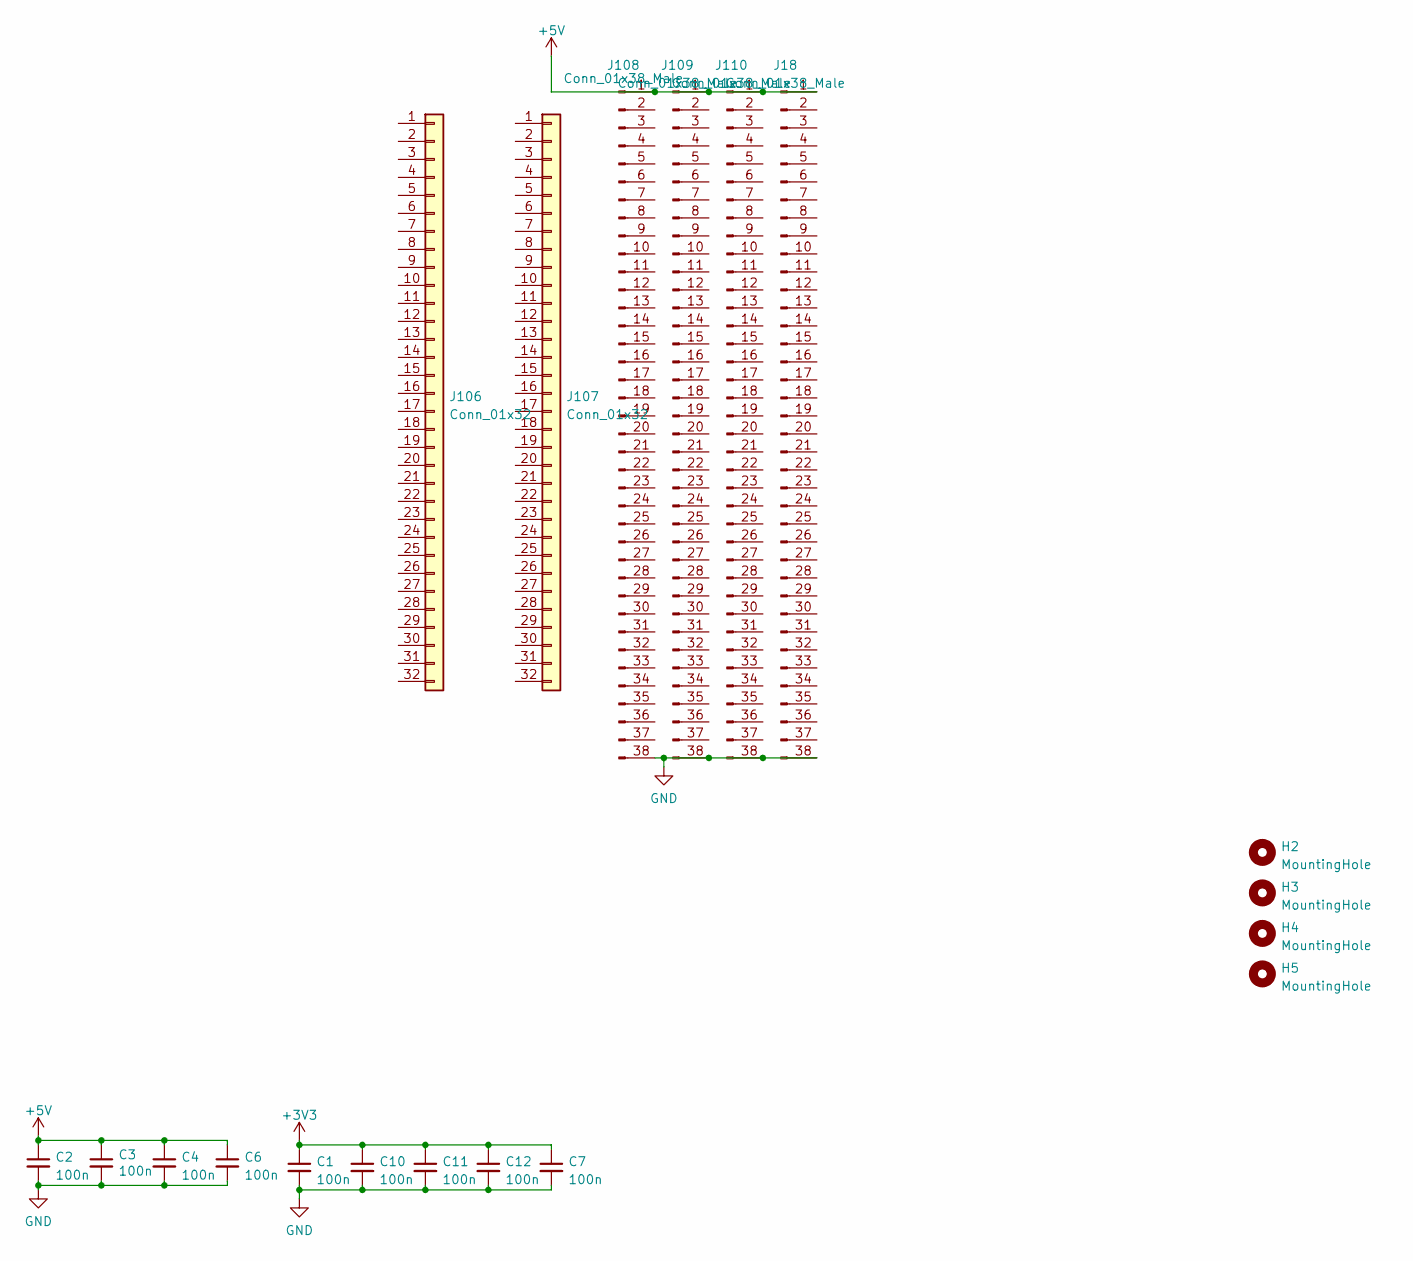
[picture p97: schematic proto.kicad_sch, Unicomp v2 - RAMROM Board]

Parts:
C1, C2, C4, C6, C7, C10, C11, C12: 100n; C_1206_3216Metric
C3: 100n; C_1206_3216Metric_Pad1.33x1.80mm_HandSolder
H2, H3, H4, H5: MountingHole; MountingHole_3.2mm_M3
J18, J108, J109, J110: Conn_01x38_Male; PinHeader_1x38_P2.54mm_Vertical
J106, J107: Conn_01x32; PinHeader_1x32_P2.54mm_Vertical

Connections:
+3V3: C1.1, C7.1, C10.1, C11.1, C12.1; also elsewhere on the board
+5V: C2.1, C3.1, C4.1, C6.1, J18.1, J108.1, J109.1, J110.1; also elsewhere on the board
GND: C1.2, C2.2, C3.2, C4.2, C6.2, C7.2, C10.2, C11.2, C12.2, J18.38, J108.38, J109.38, J110.38; also elsewhere on the board

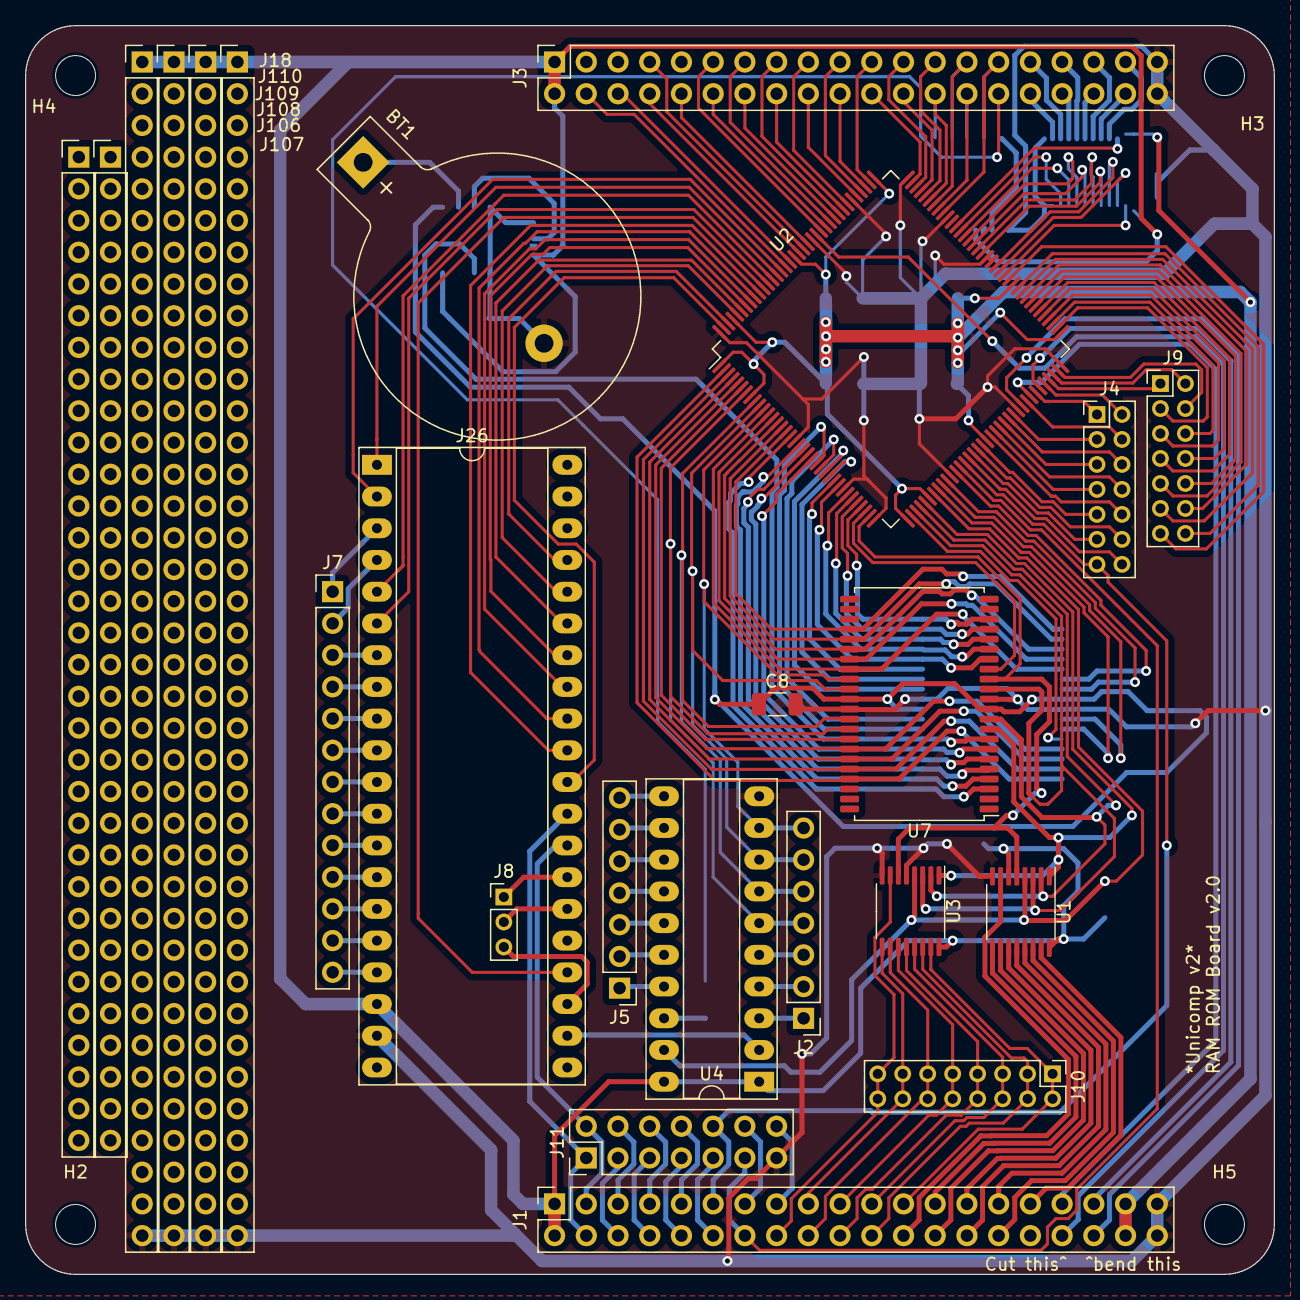
[picture p98: board RAMROM_CPLD_board.kicad_pcb from above]

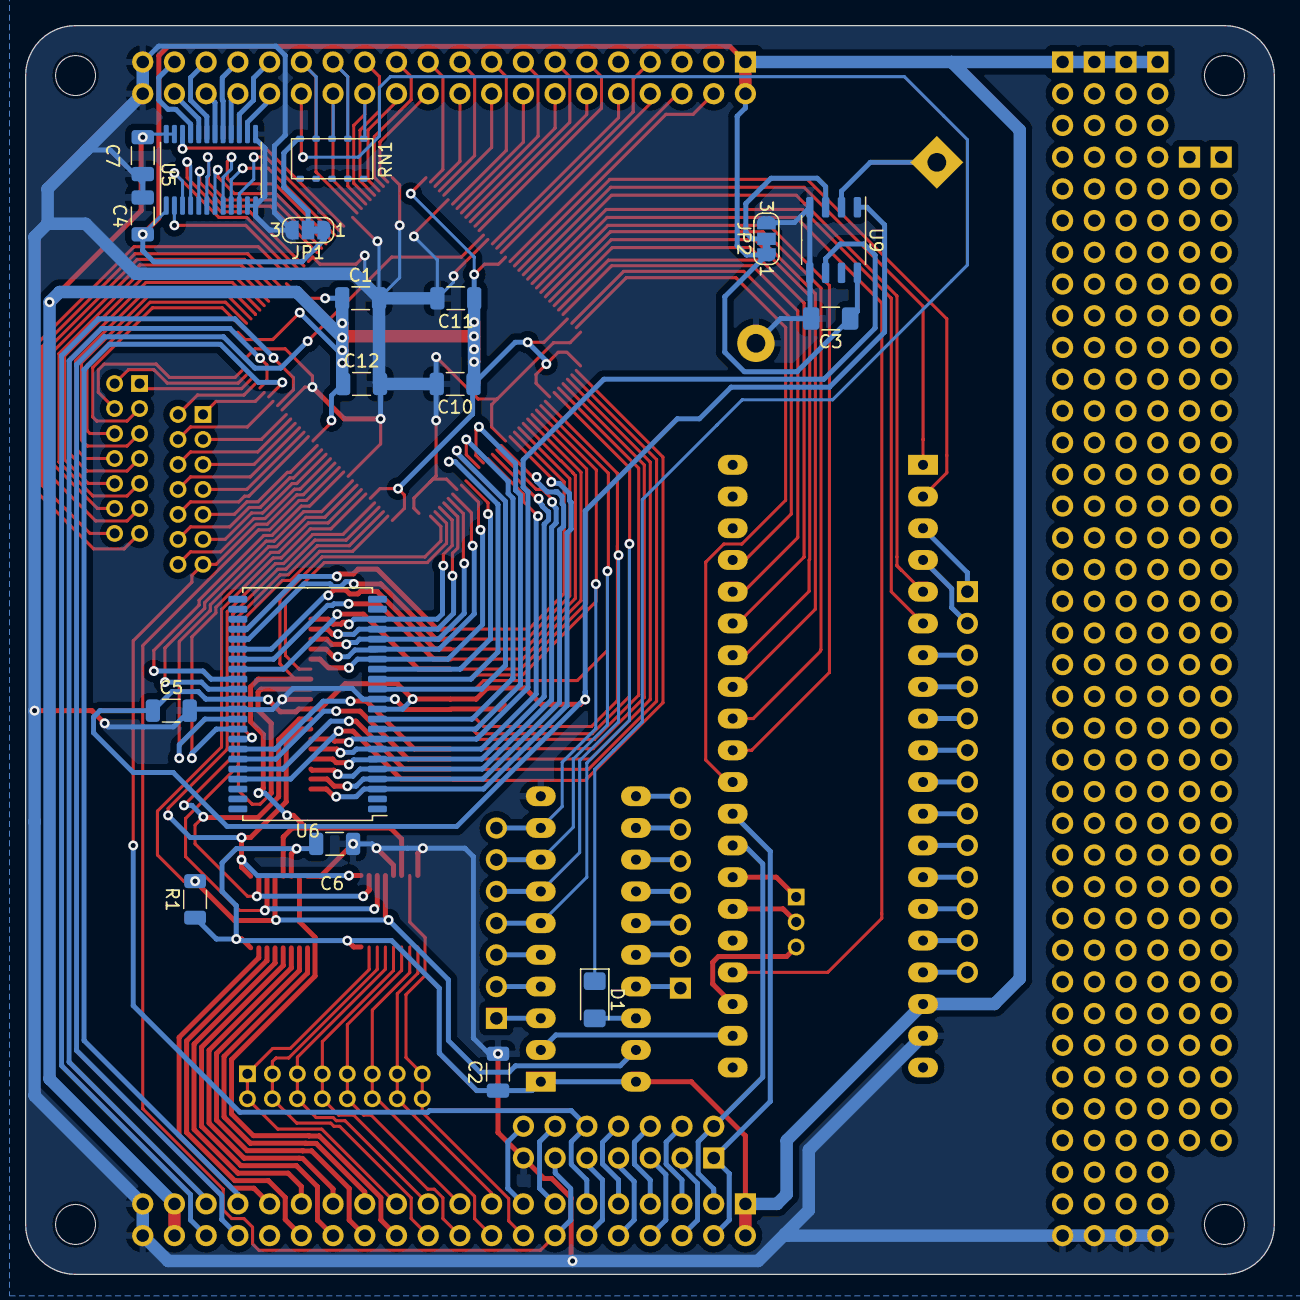
[picture p99: board RAMROM_CPLD_board.kicad_pcb from below]

Board: 2 copper layers, 100.0 x 100.0 mm, 46 parts (18 on the bottom side), 192 nets.
