roberto314/Unicomp2/not produced boards/RAMROM_Board_v3/RAMROM_Board_v3.kicad_pcb

## KiCad design not produced boards/RAMROM_Board_v3/RAMROM_Board_v3.kicad_pcb (2023-07-25)

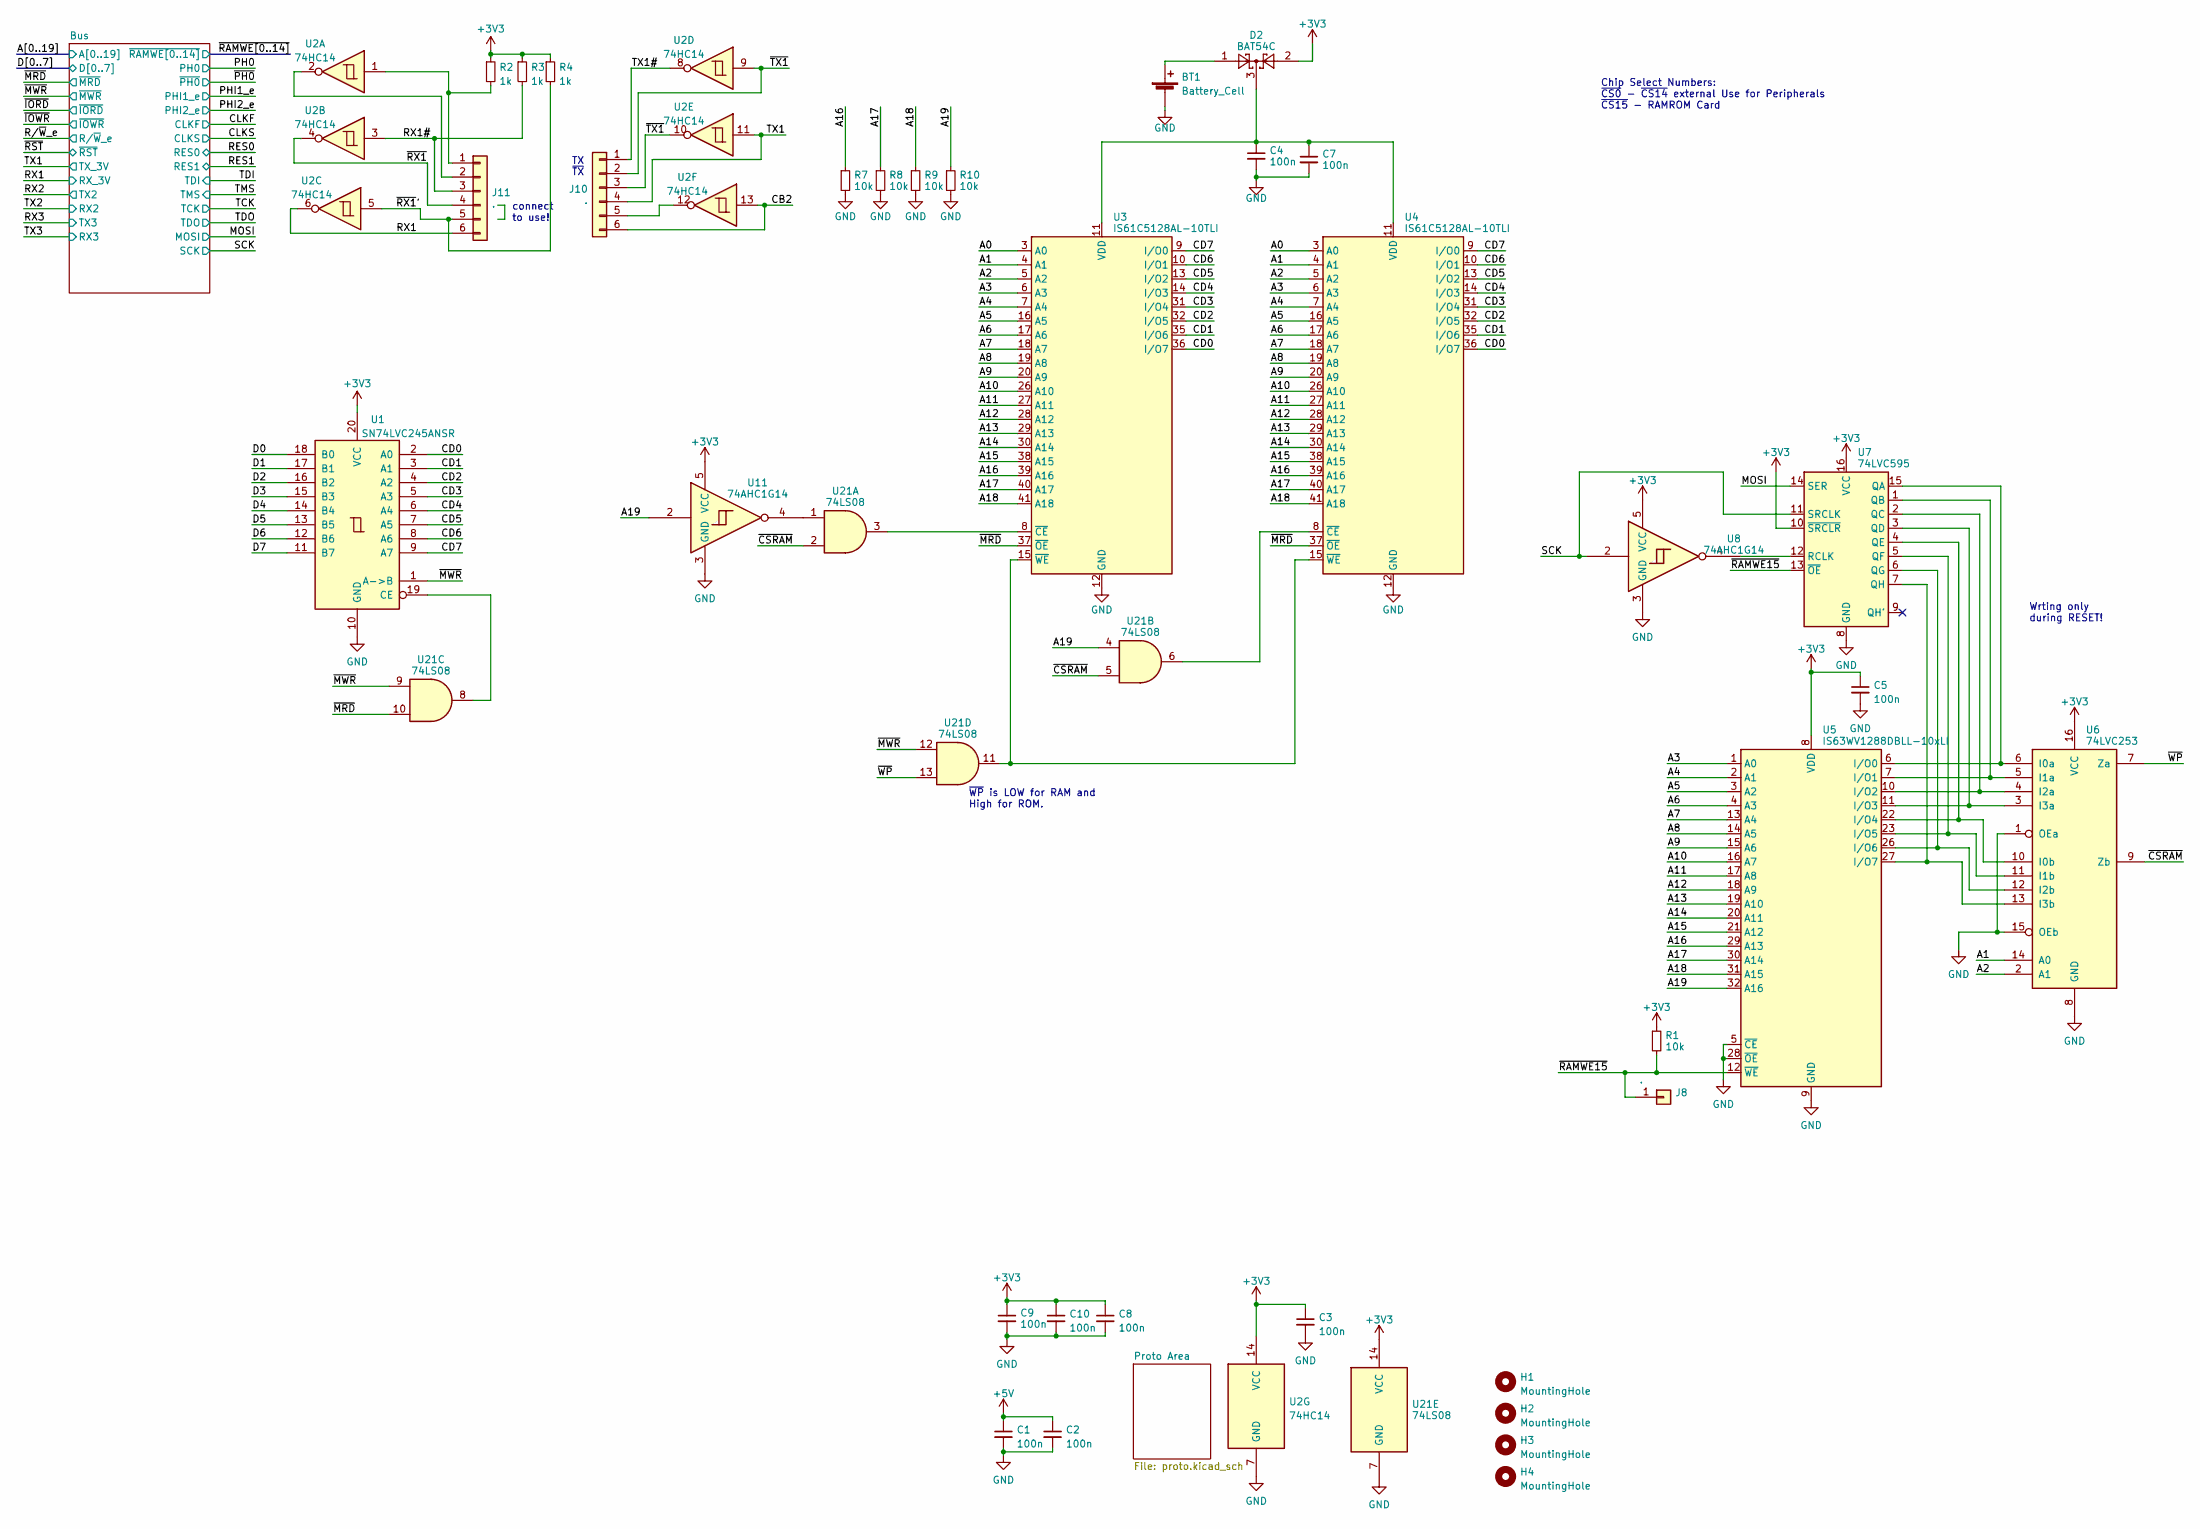
[picture p100: schematic RAMROM_Board_v3.kicad_sch, Unicomp v2 - RAMROM Board]

Parts:
BT1: Battery_Cell; BatteryHolder_Keystone_103_1x20mm
C1, C2, C3, C4, C5, C7, C8, C9, C10: 100n; C_1206_3216Metric
D2: BAT54C; SOT-23
H1, H2, H3, H4: MountingHole; MountingHole_3.2mm_M3
J8: .; PinHeader_1x01_P2.00mm_Vertical
J10, J11: .; PinHeader_1x06_P2.54mm_Vertical
R1, R7, R8, R9, R10: 10k; R_1206_3216Metric_Pad1.30x1.75mm_HandSolder
R2, R3, R4: 1k; R_1206_3216Metric_Pad1.30x1.75mm_HandSolder
U1: SN74LVC245ANSR; SO-20_5.3x12.6mm_P1.27mm
U2: 74HC14; DIP-14_W7.62mm_Socket
U3, U4: IS61C5128AL-10TLI; TSOP-II-44_10.16x18.41mm_P0.8mm
U5: IS63WV1288DBLL-10xLI; TSOP-II-32_21.0x10.2mm_P1.27mm
U6: 74LVC253; SO-16_3.9x9.9mm_P1.27mm
U7: 74LVC595; SO-16_3.9x9.9mm_P1.27mm
U8, U11: 74AHC1G14; SOT-23-5
U21: 74LS08; SOIC-14_3.9x8.7mm_P1.27mm

Connections:
+3V3: C3.1, C5.1, C8.1, C9.1, C10.1, D2.2, R1.1, R2.1, R3.1, R4.1, U1.20 (VCC), U2.14 (VCC), U5.8 (VDD), U5.24 (VDD), U6.16 (VCC), U7.10 (~SRCLR), U7.16 (VCC), U8.5 (VCC), U11.5 (VCC), U21.14 (VCC); also elsewhere on the board
+5V: C1.1, C2.1; also elsewhere on the board
/A0: U3.3 (A0), U4.3 (A0); also elsewhere on the board
/A1: U3.4 (A1), U4.4 (A1), U6.14 (A0); also elsewhere on the board
/A2: U3.5 (A2), U4.5 (A2), U6.2 (A1); also elsewhere on the board
/A3: U3.6 (A3), U4.6 (A3), U5.1 (A0); also elsewhere on the board
/A4: U3.7 (A4), U4.7 (A4), U5.2 (A1); also elsewhere on the board
/A5: U3.16 (A5), U4.16 (A5), U5.3 (A2); also elsewhere on the board
/A6: U3.17 (A6), U4.17 (A6), U5.4 (A3); also elsewhere on the board
/A7: U3.18 (A7), U4.18 (A7), U5.13 (A4); also elsewhere on the board
/A8: U3.19 (A8), U4.19 (A8), U5.14 (A5); also elsewhere on the board
/A9: U3.20 (A9), U4.20 (A9), U5.15 (A6); also elsewhere on the board
/A10: U3.26 (A10), U4.26 (A10), U5.16 (A7); also elsewhere on the board
/A11: U3.27 (A11), U4.27 (A11), U5.17 (A8); also elsewhere on the board
/A12: U3.28 (A12), U4.28 (A12), U5.18 (A9); also elsewhere on the board
/A13: U3.29 (A13), U4.29 (A13), U5.19 (A10); also elsewhere on the board
/A14: U3.30 (A14), U4.30 (A14), U5.20 (A11); also elsewhere on the board
/A15: U3.38 (A15), U4.38 (A15), U5.21 (A12); also elsewhere on the board
/A16: R7.1, U3.39 (A16), U4.39 (A16), U5.29 (A13); also elsewhere on the board
/A17: R8.1, U3.40 (A17), U4.40 (A17), U5.30 (A14); also elsewhere on the board
/A18: R9.1, U3.41 (A18), U4.41 (A18), U5.31 (A15); also elsewhere on the board
/A19: R10.1, U5.32 (A16), U11.2, U21.4; also elsewhere on the board
/CB2: J10.6, U2.13
/CD0: U1.2 (A0), U3.36 (I/O7), U4.36 (I/O7)
/CD1: U1.3 (A1), U3.35 (I/O6), U4.35 (I/O6)
/CD2: U1.4 (A2), U3.32 (I/O5), U4.32 (I/O5)
/CD3: U1.5 (A3), U3.31 (I/O4), U4.31 (I/O4)
/CD4: U1.6 (A4), U3.14 (I/O3), U4.14 (I/O3)
/CD5: U1.7 (A5), U3.13 (I/O2), U4.13 (I/O2)
/CD6: U1.8 (A6), U3.10 (I/O1), U4.10 (I/O1)
/CD7: U1.9 (A7), U3.9 (I/O0), U4.9 (I/O0)
/D0: U1.18 (B0); also elsewhere on the board
/D1: U1.17 (B1); also elsewhere on the board
/D2: U1.16 (B2); also elsewhere on the board
/D3: U1.15 (B3); also elsewhere on the board
/D4: U1.14 (B4); also elsewhere on the board
/D5: U1.13 (B5); also elsewhere on the board
/D6: U1.12 (B6); also elsewhere on the board
/D7: U1.11 (B7); also elsewhere on the board
/MOSI: U7.14 (SER); also elsewhere on the board
/RX1: J11.6, U2.6; also elsewhere on the board
/RX1#: J11.3, R3.2, U2.3
/SCK: U7.11 (SRCLK), U8.2; also elsewhere on the board
/TX1: J10.4, U2.11; also elsewhere on the board
/TX1#: J10.1, U2.8
/~CSRAM: U6.9 (Zb), U21.2, U21.5
/~MRD: U3.37 (~OE), U4.37 (~OE), U21.10; also elsewhere on the board
/~MWR: U1.1 (A->B), U21.9, U21.12; also elsewhere on the board
/~RAMWE15: J8.1, R1.2, U5.12 (~WE), U7.13 (~OE)
/~RX1: J11.4, U2.4
/~RX1': J11.5, R4.2, U2.5
/~TX1: J10.2, J10.3, U2.9, U2.10
/~WP: U6.7 (Za), U21.13
GND: BT1.2 (-), C1.2, C2.2, C3.2, C4.2, C5.2, C7.2, C8.2, C9.2, C10.2, R7.2, R8.2, R9.2, R10.2, U1.10 (GND), U2.7 (GND), U3.12 (GND), U3.34 (GND), U4.12 (GND), U4.34 (GND), U5.5 (~CE), U5.9 (GND), U5.25 (GND), U5.28 (~OE), U6.1 (OEa), U6.8 (GND), U6.15 (OEb), U7.8 (GND), U8.3 (GND), U11.3 (GND), U21.7 (GND); also elsewhere on the board
unnamed: BT1.1 (+), D2.1
unnamed: C4.1, C7.1, D2.3, U3.11 (VDD), U3.33 (VDD), U4.11 (VDD), U4.33 (VDD)
unnamed: J10.5, U2.12
unnamed: J11.1, R2.2, U2.1
unnamed: J11.2, U2.2
unnamed: U1.19 (CE), U21.8
unnamed: U3.8 (~CE), U21.3
unnamed: U3.15 (~WE), U4.15 (~WE), U21.11
unnamed: U4.8 (~CE), U21.6
unnamed: U5.6 (I/O0), U6.6 (I0a), U7.15 (QA)
unnamed: U5.7 (I/O1), U6.5 (I1a), U7.1 (QB)
unnamed: U5.10 (I/O2), U6.4 (I2a), U7.2 (QC)
unnamed: U5.11 (I/O3), U6.3 (I3a), U7.3 (QD)
unnamed: U5.22 (I/O4), U6.10 (I0b), U7.4 (QE)
unnamed: U5.23 (I/O5), U6.11 (I1b), U7.5 (QF)
unnamed: U5.26 (I/O6), U6.12 (I2b), U7.6 (QG)
unnamed: U5.27 (I/O7), U6.13 (I3b), U7.7 (QH)
unnamed: U7.12 (RCLK), U8.4
unnamed: U11.4, U21.1

Notes on the sheet:
Wrting only during RESET!
connect to use!
~{WP} is LOW for RAM and High for ROM.
TX ~{TX}
Chip Select Numbers: ~{CS0} - ~{CS14} external Use for Peripherals ~{CS15} - RAMROM Card

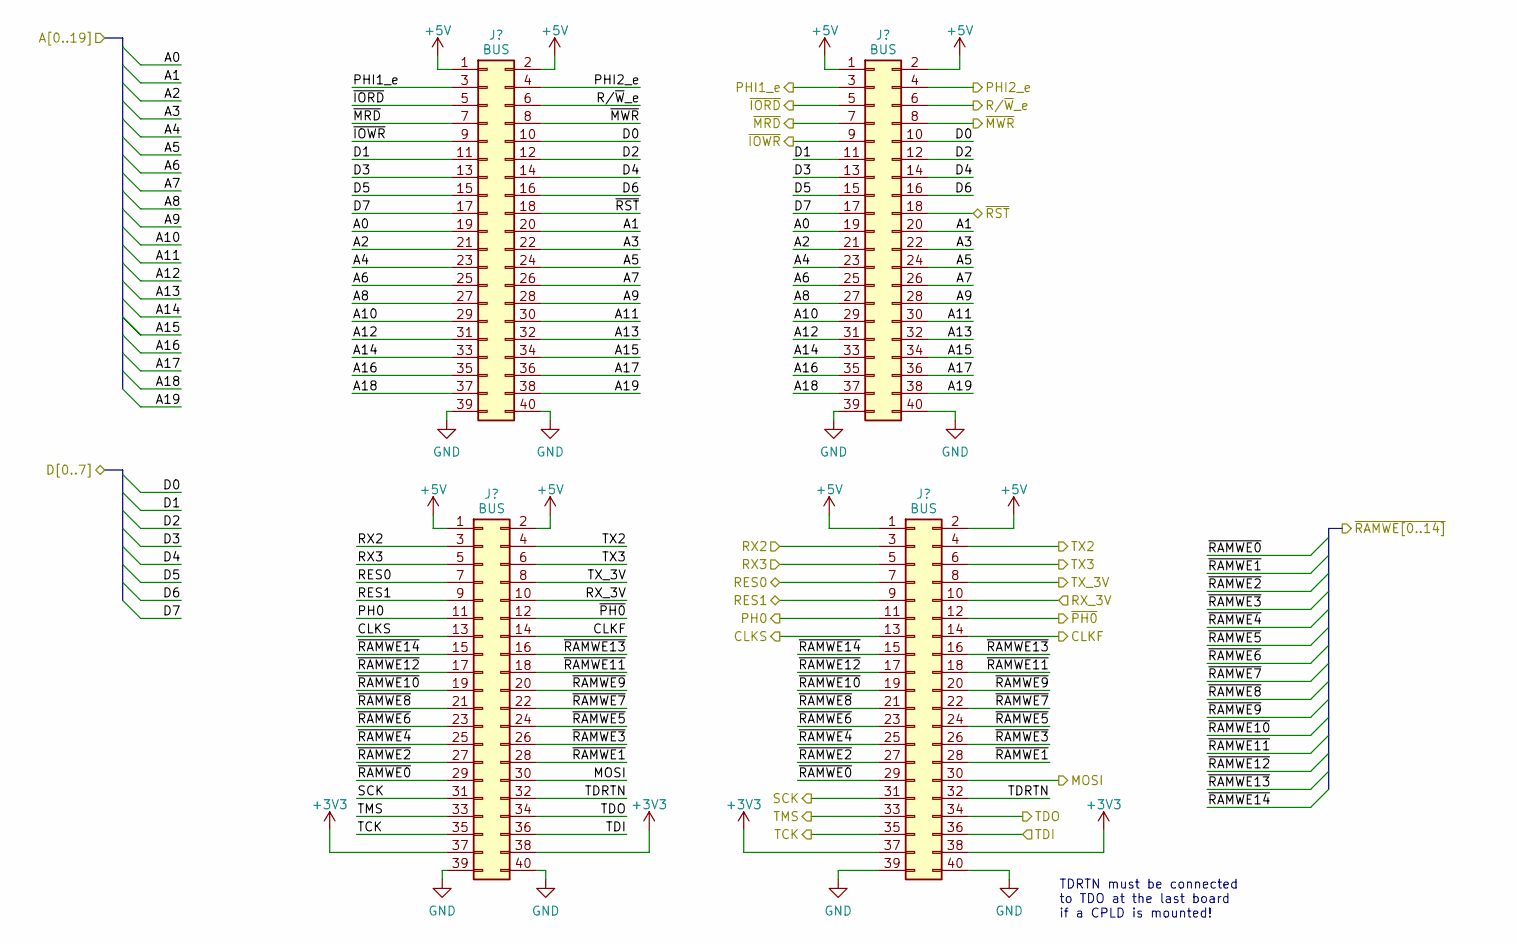
[picture p101: schematic bus.kicad_sch, Unicomp v2 - RAMROM Board]

Parts:
J1, J2, J3, J4: BUS; PinSocket_2x20_P2.54mm_Vertical

Connections:
+3V3: J2.37, J2.38, J4.37, J4.38; also elsewhere on the board
+5V: J1.1, J1.2, J2.1, J2.2, J3.1, J3.2, J4.1, J4.2; also elsewhere on the board
/A0: J1.19, J3.19; also elsewhere on the board
/A1: J1.20, J3.20; also elsewhere on the board
/A2: J1.21, J3.21; also elsewhere on the board
/A3: J1.22, J3.22; also elsewhere on the board
/A4: J1.23, J3.23; also elsewhere on the board
/A5: J1.24, J3.24; also elsewhere on the board
/A6: J1.25, J3.25; also elsewhere on the board
/A7: J1.26, J3.26; also elsewhere on the board
/A8: J1.27, J3.27; also elsewhere on the board
/A9: J1.28, J3.28; also elsewhere on the board
/A10: J1.29, J3.29; also elsewhere on the board
/A11: J1.30, J3.30; also elsewhere on the board
/A12: J1.31, J3.31; also elsewhere on the board
/A13: J1.32, J3.32; also elsewhere on the board
/A14: J1.33, J3.33; also elsewhere on the board
/A15: J1.34, J3.34; also elsewhere on the board
/A16: J1.35, J3.35; also elsewhere on the board
/A17: J1.36, J3.36; also elsewhere on the board
/A18: J1.37, J3.37; also elsewhere on the board
/A19: J1.38, J3.38; also elsewhere on the board
/Bus/TDRTN: J2.32, J4.32
/CLKF: J2.14, J4.14
/CLKS: J2.13, J4.13
/D0: J1.10, J3.10; also elsewhere on the board
/D1: J1.11, J3.11; also elsewhere on the board
/D2: J1.12, J3.12; also elsewhere on the board
/D3: J1.13, J3.13; also elsewhere on the board
/D4: J1.14, J3.14; also elsewhere on the board
/D5: J1.15, J3.15; also elsewhere on the board
/D6: J1.16, J3.16; also elsewhere on the board
/D7: J1.17, J3.17; also elsewhere on the board
/MOSI: J2.30, J4.30; also elsewhere on the board
/PH0: J2.11, J4.11
/PHI1_e: J1.3, J3.3
/PHI2_e: J1.4, J3.4
/RES0: J2.7, J4.7
/RES1: J2.9, J4.9
/RX1: J2.10, J4.10; also elsewhere on the board
/RX2: J2.4, J4.4
/RX3: J2.6, J4.6
/R/~W_e: J1.6, J3.6
/SCK: J2.31, J4.31; also elsewhere on the board
/TCK: J2.35, J4.35
/TDI: J2.36, J4.36
/TDO: J2.34, J4.34
/TMS: J2.33, J4.33
/TX1: J2.8, J4.8; also elsewhere on the board
/TX2: J2.3, J4.3
/TX3: J2.5, J4.5
/~IORD: J1.5, J3.5
/~IOWR: J1.9, J3.9
/~MRD: J1.7, J3.7; also elsewhere on the board
/~MWR: J1.8, J3.8; also elsewhere on the board
/~PH0: J2.12, J4.12
/~RAMWE0: J2.29, J4.29
/~RAMWE1: J2.28, J4.28
/~RAMWE2: J2.27, J4.27
/~RAMWE3: J2.26, J4.26
/~RAMWE4: J2.25, J4.25
/~RAMWE5: J2.24, J4.24
/~RAMWE6: J2.23, J4.23
/~RAMWE7: J2.22, J4.22
/~RAMWE8: J2.21, J4.21
/~RAMWE9: J2.20, J4.20
/~RAMWE10: J2.19, J4.19
/~RAMWE11: J2.18, J4.18
/~RAMWE12: J2.17, J4.17
/~RAMWE13: J2.16, J4.16
/~RAMWE14: J2.15, J4.15
/~RST: J1.18, J3.18
GND: J1.39, J1.40, J2.39, J2.40, J3.39, J3.40, J4.39, J4.40; also elsewhere on the board

Notes on the sheet:
TDRTN must be connected to TDO at the last board if a CPLD is mounted!

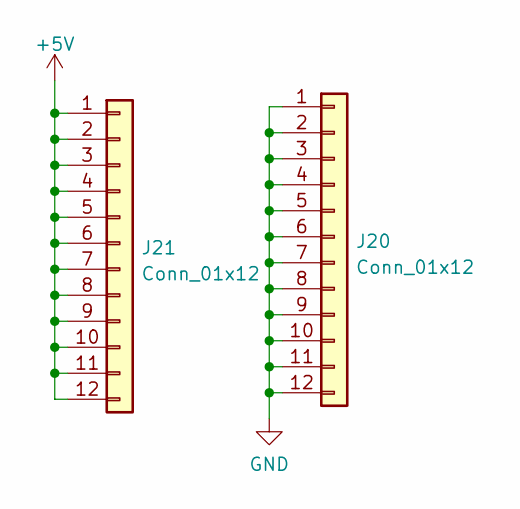
[picture p102: schematic proto.kicad_sch, Unicomp v2 - RAMROM Board]

Parts:
J20, J21: Conn_01x12; PinHeader_1x12_P2.54mm_Vertical

Connections:
+5V: J21.1, J21.2, J21.3, J21.4, J21.5, J21.6, J21.7, J21.8, J21.9, J21.10, J21.11, J21.12; also elsewhere on the board
GND: J20.1, J20.2, J20.3, J20.4, J20.5, J20.6, J20.7, J20.8, J20.9, J20.10, J20.11, J20.12; also elsewhere on the board

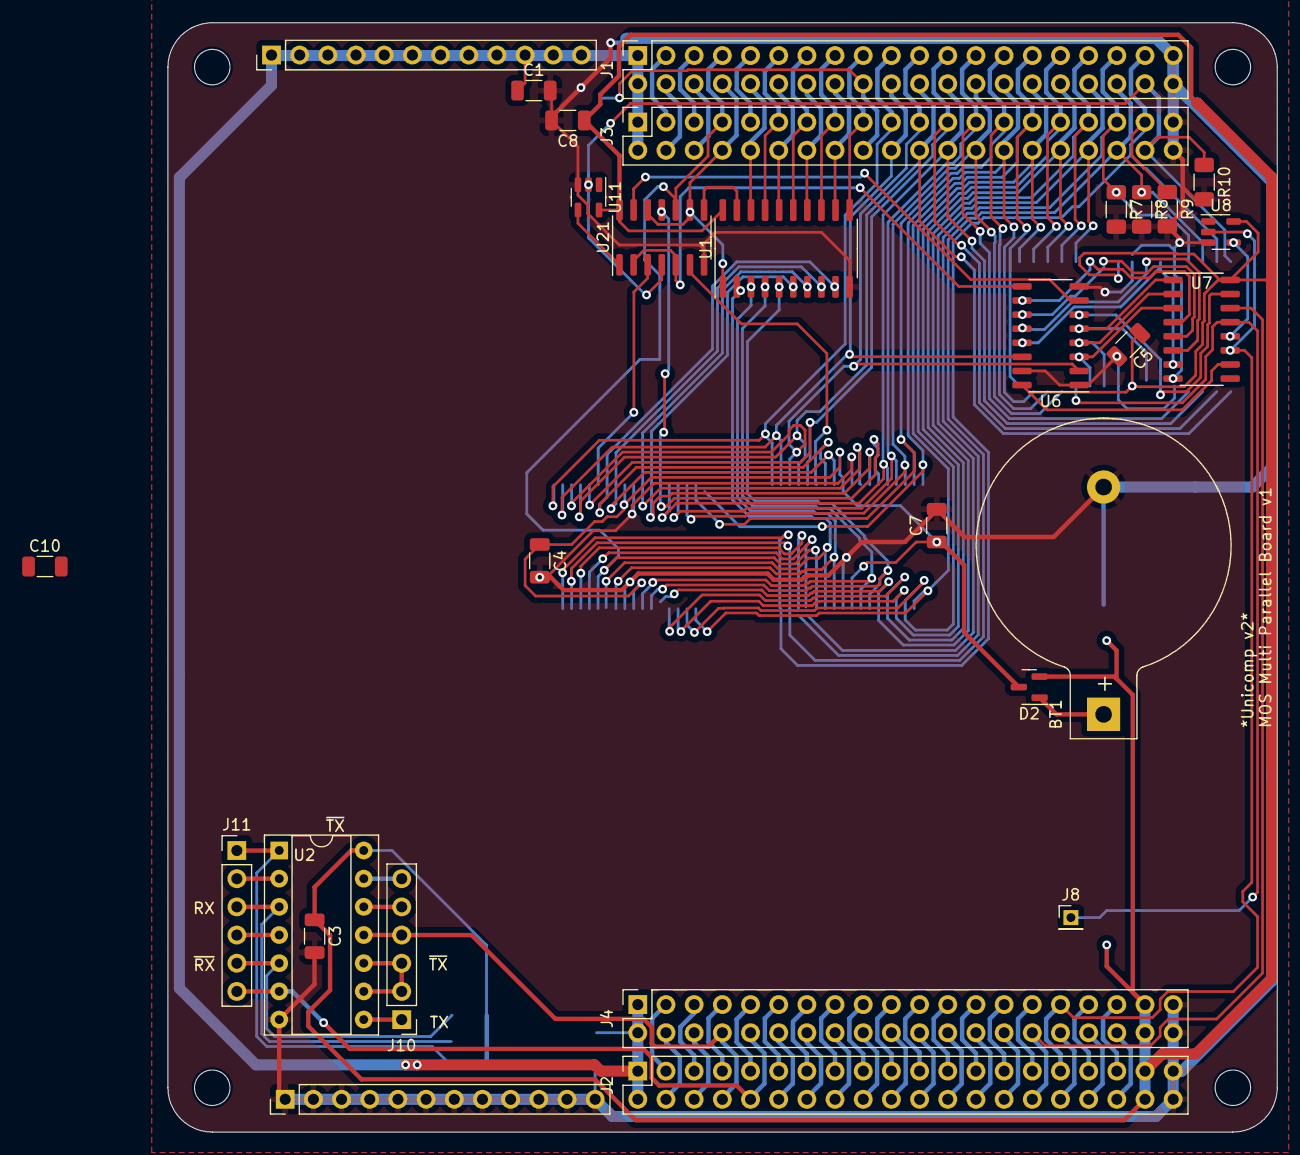
[picture p103: board RAMROM_Board_v3.kicad_pcb from above]

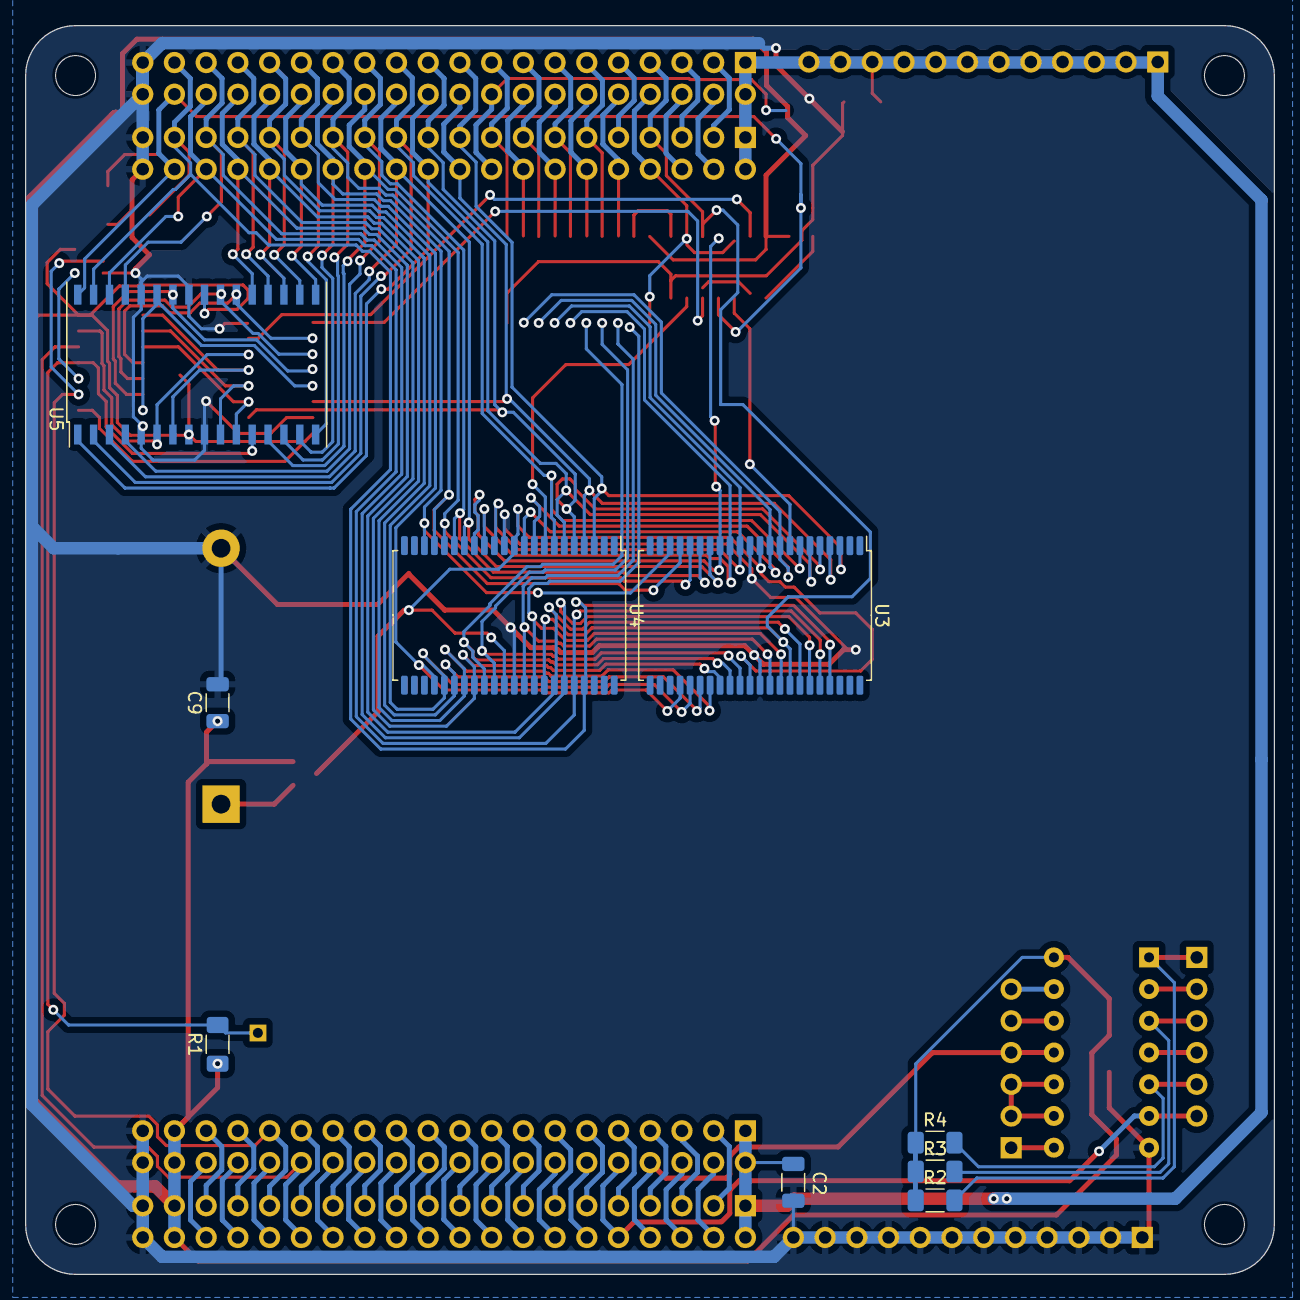
[picture p104: board RAMROM_Board_v3.kicad_pcb from below]

Board: 2 copper layers, 100.0 x 100.0 mm, 42 parts (9 on the bottom side), 109 nets.
