roberto314/Unicomp2/Synertek KTM2/UC2_synertek_KTM2/UC2_synertek_KTM2.kicad_pcb

## KiCad design Synertek KTM2/UC2_synertek_KTM2/UC2_synertek_KTM2.kicad_pcb (2023-07-25)

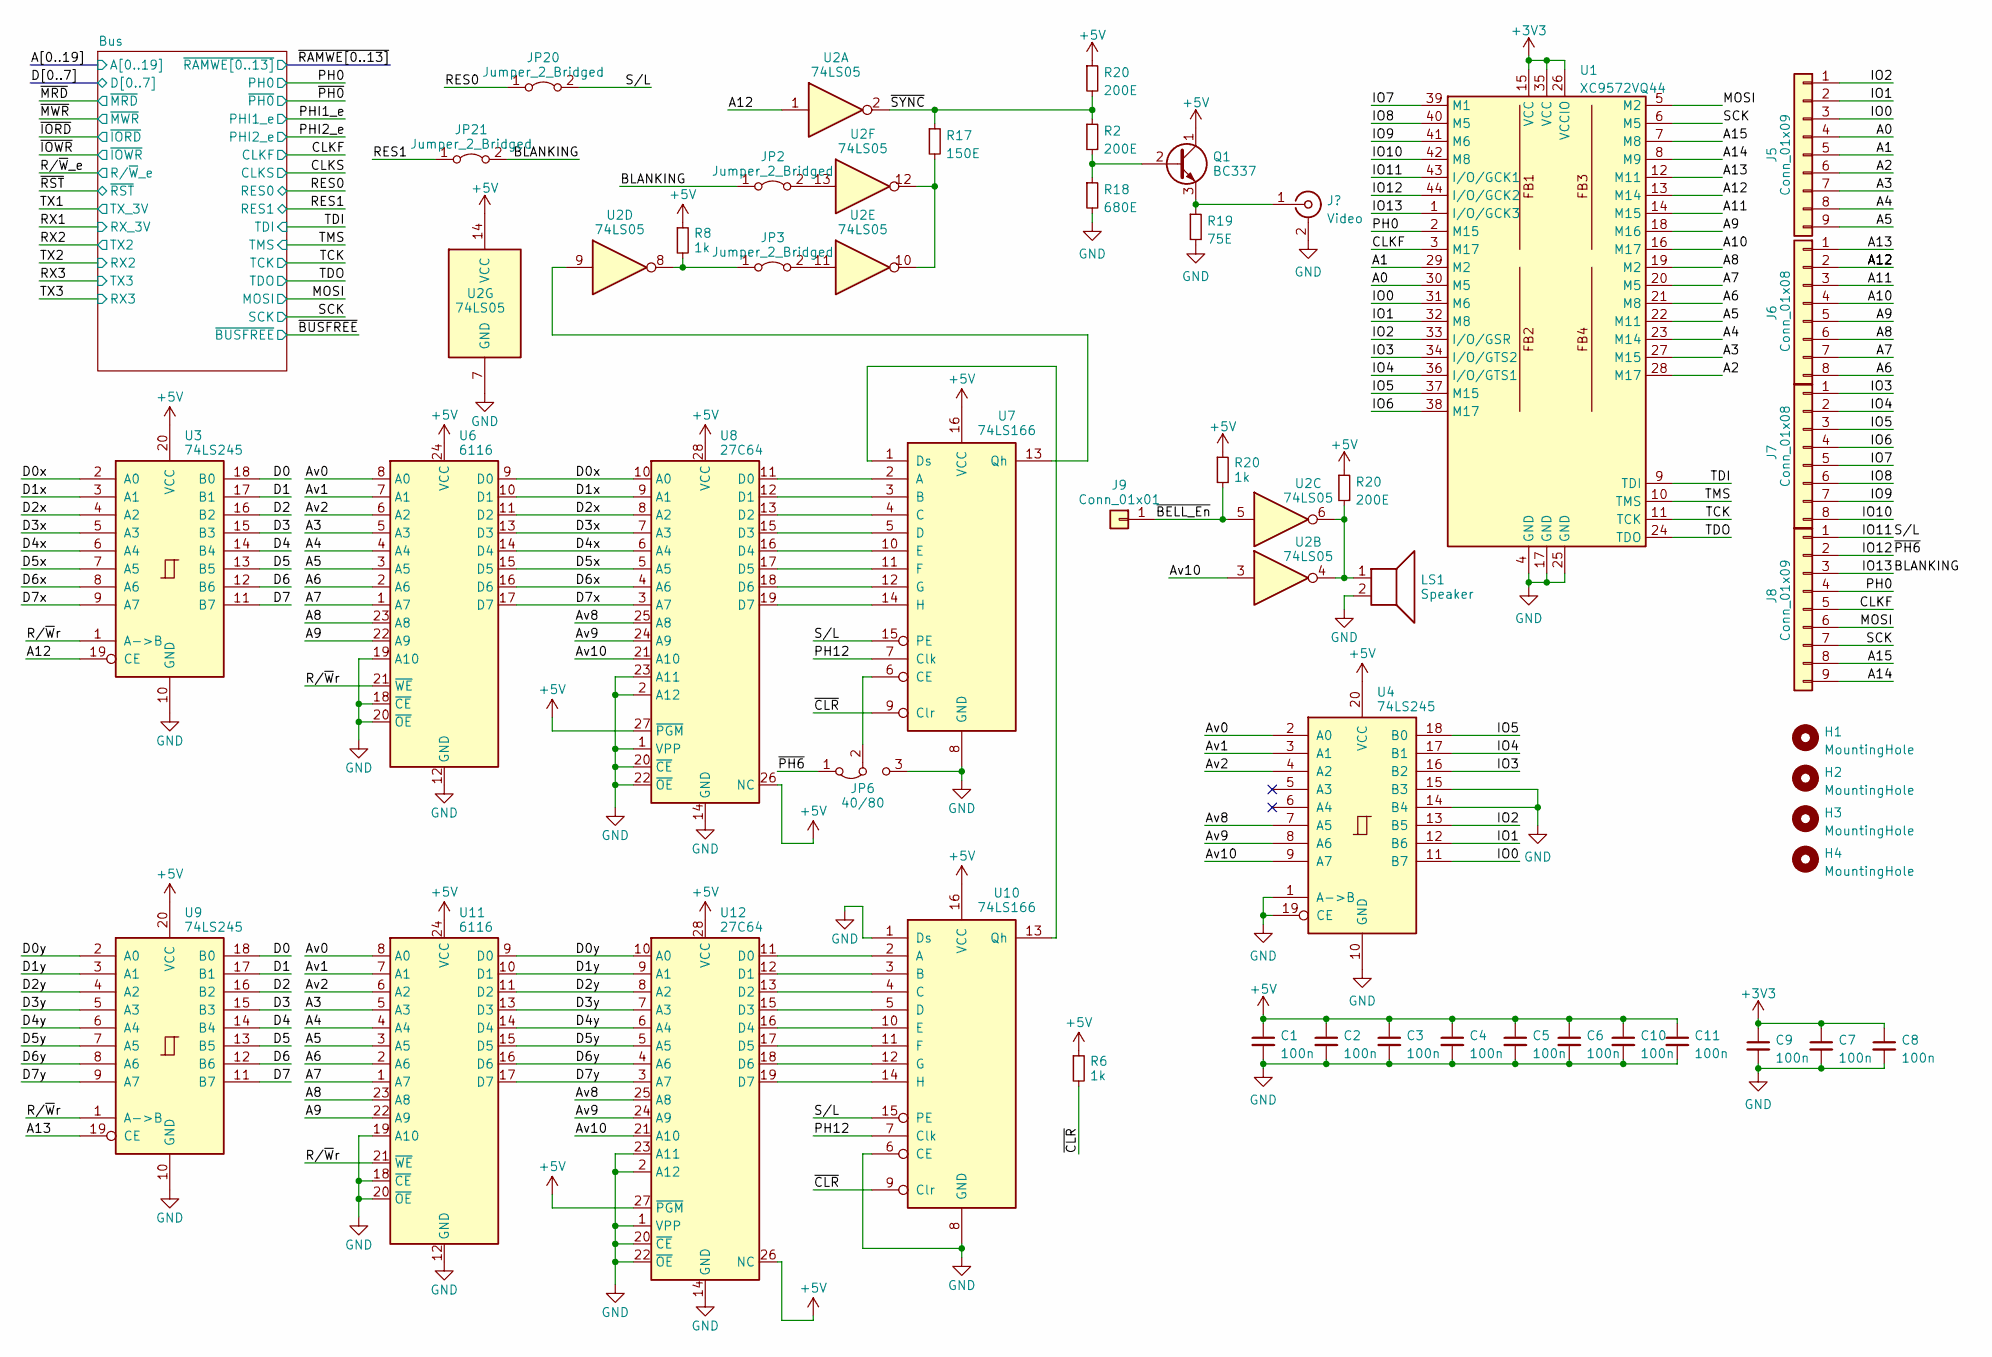
[picture p105: schematic UC2_synertek_KTM2.kicad_sch, Unicomp v2 - 6502 6802 Board]

Parts:
C1, C2, C3, C4, C5, C6, C7, C8, C9, C10, C11: 100n; C_1206_3216Metric
H1, H2, H3, H4: MountingHole; MountingHole_3.2mm_M3
J5, J8: Conn_01x09; PinHeader_1x09_P2.54mm_Vertical
J6, J7: Conn_01x08; PinHeader_1x08_P2.54mm_Vertical
J9: Conn_01x01; PinHeader_1x01_P2.54mm_Vertical
J20: Video; RCA-Jack
JP2, JP3, JP20, JP21: Jumper_2_Bridged; SolderJumper-2_P1.3mm_Bridged_RoundedPad1.0x1.5mm
JP6: 40/80; SolderJumper-3_P1.3mm_Bridged12_Pad1.0x1.5mm_NumberLabels
LS1: Speaker; MagneticBuzzer_Kingstate_KCG0601
Q1: BC337; TO-92_Inline
R2, R20: 200E; R_1206_3216Metric_Pad1.30x1.75mm_HandSolder
R6, R8: 1k; R_1206_3216Metric_Pad1.30x1.75mm_HandSolder
R17: 150E; R_1206_3216Metric_Pad1.30x1.75mm_HandSolder
R18: 680E; R_1206_3216Metric_Pad1.30x1.75mm_HandSolder
R19: 75E; R_1206_3216Metric_Pad1.30x1.75mm_HandSolder
U1: XC9572VQ44; TQFP-44_10x10mm_P0.8mm
U2: 74LS05; DIP-14_W7.62mm_LongPads
U3, U9: 74LS245; DIP-20_W7.62mm_LongPads
U4: 74LS245; SO-20_5.3x12.6mm_P1.27mm
U6, U11: 6116; DIP-24_W15.24mm_LongPads
U7, U10: 74LS166; DIP-16_W7.62mm_LongPads
U8, U12: 27C64; DIP-28_W15.24mm_LongPads

Connections:
+3V3: C7.1, C8.1, C9.1, U1.15 (VCC), U1.26 (VCCIO), U1.35 (VCC); also elsewhere on the board
+5V: C1.1, C2.1, C3.1, C4.1, C5.1, C6.1, C10.1, C11.1, Q1.1 (C), R6.1, R8.1, R20.1, U2.14 (VCC), U3.20 (VCC), U4.20 (VCC), U6.24 (VCC), U7.16 (VCC), U8.26 (NC), U8.27 (~PGM), U8.28 (VCC), U9.20 (VCC), U10.16 (VCC), U11.24 (VCC), U12.26 (NC), U12.27 (~PGM), U12.28 (VCC); also elsewhere on the board
/A0: J5.4, U1.30 (M5); also elsewhere on the board
/A1: J5.5, U1.29 (M2); also elsewhere on the board
/A2: J5.6, U1.28 (M17); also elsewhere on the board
/A3: J5.7, U1.27 (M15), U6.5 (A3), U11.5 (A3); also elsewhere on the board
/A4: J5.8, U1.23 (M14), U6.4 (A4), U11.4 (A4); also elsewhere on the board
/A5: J5.9, U1.22 (M11), U6.3 (A5), U11.3 (A5); also elsewhere on the board
/A6: J6.8, U1.21 (M8), U6.2 (A6), U11.2 (A6); also elsewhere on the board
/A7: J6.7, U1.20 (M5), U6.1 (A7), U11.1 (A7); also elsewhere on the board
/A8: J6.6, U1.19 (M2), U6.23 (A8), U11.23 (A8); also elsewhere on the board
/A9: J6.5, U1.18 (M16), U6.22 (A9), U11.22 (A9); also elsewhere on the board
/A10: J6.4, U1.16 (M17); also elsewhere on the board
/A11: J6.3, U1.14 (M15); also elsewhere on the board
/A12: J6.2, U1.13 (M14), U2.1, U3.19 (CE); also elsewhere on the board
/A13: J6.1, U1.12 (M11), U9.19 (CE); also elsewhere on the board
/A14: J8.9, U1.8 (M9); also elsewhere on the board
/A15: J8.8, U1.7 (M8); also elsewhere on the board
/Av0: U4.2 (A0), U6.8 (A0), U11.8 (A0)
/Av1: U4.3 (A1), U6.7 (A1), U11.7 (A1)
/Av2: U4.4 (A2), U6.6 (A2), U11.6 (A2)
/Av8: U4.7 (A5), U8.25 (A8), U12.25 (A8)
/Av9: U4.8 (A6), U8.24 (A9), U12.24 (A9)
/Av10: U2.3, U4.9 (A7), U8.21 (A10), U12.21 (A10)
/BLANKING: J8.3, JP2.1 (A), JP21.2 (B), U1.1 (I/O/GCK3)
/CLKF: J8.5, U1.3 (M17); also elsewhere on the board
/D0: U3.18 (B0), U9.18 (B0); also elsewhere on the board
/D0x: U3.2 (A0), U6.9 (D0), U8.10 (A0)
/D0y: U9.2 (A0), U11.9 (D0), U12.10 (A0)
/D1: U3.17 (B1), U9.17 (B1); also elsewhere on the board
/D1x: U3.3 (A1), U6.10 (D1), U8.9 (A1)
/D1y: U9.3 (A1), U11.10 (D1), U12.9 (A1)
/D2: U3.16 (B2), U9.16 (B2); also elsewhere on the board
/D2x: U3.4 (A2), U6.11 (D2), U8.8 (A2)
/D2y: U9.4 (A2), U11.11 (D2), U12.8 (A2)
/D3: U3.15 (B3), U9.15 (B3); also elsewhere on the board
/D3x: U3.5 (A3), U6.13 (D3), U8.7 (A3)
/D3y: U9.5 (A3), U11.13 (D3), U12.7 (A3)
/D4: U3.14 (B4), U9.14 (B4); also elsewhere on the board
/D4x: U3.6 (A4), U6.14 (D4), U8.6 (A4)
/D4y: U9.6 (A4), U11.14 (D4), U12.6 (A4)
/D5: U3.13 (B5), U9.13 (B5); also elsewhere on the board
/D5x: U3.7 (A5), U6.15 (D5), U8.5 (A5)
/D5y: U9.7 (A5), U11.15 (D5), U12.5 (A5)
/D6: U3.12 (B6), U9.12 (B6); also elsewhere on the board
/D6x: U3.8 (A6), U6.16 (D6), U8.4 (A6)
/D6y: U9.8 (A6), U11.16 (D6), U12.4 (A6)
/D7: U3.11 (B7), U9.11 (B7); also elsewhere on the board
/D7x: U3.9 (A7), U6.17 (D7), U8.3 (A7)
/D7y: U9.9 (A7), U11.17 (D7), U12.3 (A7)
/IO0: J5.3, U1.31 (M6), U4.11 (B7)
/IO1: J5.2, U1.32 (M8), U4.12 (B6)
/IO2: J5.1, U1.33 (I/O/GSR), U4.13 (B5)
/IO3: J7.1, U1.34 (I/O/GTS2), U4.16 (B2)
/IO4: J7.2, U1.36 (I/O/GTS1), U4.17 (B1)
/IO5: J7.3, U1.37 (M15), U4.18 (B0)
/IO6: J7.4, U1.38 (M17)
/IO7: J7.5, U1.39 (M1)
/IO8: J7.6, U1.40 (M5)
/IO9: J7.7, U1.41 (M6)
/IO10: J7.8, U1.42 (M8)
/IO11: J8.1, JP20.2 (B), U1.43 (I/O/GCK1), U7.15 (PE), U10.15 (PE)
/IO12: J8.2, JP6.1 (A), U1.44 (I/O/GCK2)
/MOSI: J8.6, U1.5 (M2); also elsewhere on the board
/PH0: J8.4, U1.2 (M15); also elsewhere on the board
/PH12: U7.7 (Clk), U10.7 (Clk)
/RES0: JP20.1 (A); also elsewhere on the board
/RES1: JP21.1 (A); also elsewhere on the board
/R/~Wr: U3.1 (A->B), U6.21 (~WE), U9.1 (A->B), U11.21 (~WE)
/SCK: J8.7, U1.6 (M5); also elsewhere on the board
/TCK: U1.11 (TCK); also elsewhere on the board
/TDI: U1.9 (TDI); also elsewhere on the board
/TDO: U1.24 (TDO); also elsewhere on the board
/TMS: U1.10 (TMS); also elsewhere on the board
/~CLR: R6.2, U7.9 (Clr), U10.9 (Clr)
GND: C1.2, C2.2, C3.2, C4.2, C5.2, C6.2, C7.2, C8.2, C9.2, C10.2, C11.2, J20.2 (Ext), JP6.3 (B), LS1.2, R18.2, R19.2, U1.4 (GND), U1.17 (GND), U1.25 (GND), U2.7 (GND), U3.10 (GND), U4.1 (A->B), U4.10 (GND), U4.14 (B4), U4.15 (B3), U4.19 (CE), U6.12 (GND), U6.18 (~CE), U6.19 (A10), U6.20 (~OE), U7.8 (GND), U8.1 (VPP), U8.2 (A12), U8.14 (GND), U8.20 (~CE), U8.22 (~OE), U8.23 (A11), U9.10 (GND), U10.1 (Ds), U10.6 (CE), U10.8 (GND), U11.12 (GND), U11.18 (~CE), U11.19 (A10), U11.20 (~OE), U12.1 (VPP), U12.2 (A12), U12.14 (GND), U12.20 (~CE), U12.22 (~OE), U12.23 (A11); also elsewhere on the board
unnamed: J20.1 (In), Q1.3 (E), R19.1
unnamed: JP2.2 (B), U2.13
unnamed: JP3.1 (A), R8.2, U2.8
unnamed: JP3.2 (B), U2.11
unnamed: JP6.2 (C), U7.6 (CE)
unnamed: Q1.2 (B), R2.2, R18.1
unnamed: R17.2, U2.10, U2.12
unnamed: U7.2 (A), U8.11 (D0)
unnamed: U7.3 (B), U8.12 (D1)
unnamed: U7.4 (C), U8.13 (D2)
unnamed: U7.5 (D), U8.15 (D3)
unnamed: U7.10 (E), U8.16 (D4)
unnamed: U7.11 (F), U8.17 (D5)
unnamed: U7.12 (G), U8.18 (D6)
unnamed: U7.14 (H), U8.19 (D7)
unnamed: U2.9, U7.13 (Qh)
unnamed: U10.2 (A), U12.11 (D0)
unnamed: U10.3 (B), U12.12 (D1)
unnamed: U10.4 (C), U12.13 (D2)
unnamed: U10.5 (D), U12.15 (D3)
unnamed: U10.10 (E), U12.16 (D4)
unnamed: U10.11 (F), U12.17 (D5)
unnamed: U10.12 (G), U12.18 (D6)
unnamed: U10.14 (H), U12.19 (D7)
unnamed: U7.1 (Ds), U10.13 (Qh)
