roberto314/Unicomp2/RAMROM_512k_board/F401-blackpill_Unicomp_RAMROM/main.h

/*
 * main.h
 *
 *  Created on: Sep 23, 2020
 *      Author: rob
 */

#ifndef MAIN_H_
#define MAIN_H_

#include <stdio.h>
#include <string.h>
#include "ostrich.h"
#include "ch.h"
#include "hal.h"

#include "shell.h"
#include "chprintf.h"
#include "comm.h"

#endif /* MAIN_H_ */
