roberto314/Unicomp2/RAMROM_512k_board/F401-blackpill_Unicomp_RAMROM/userlib/include/mypwm.h

/*
 * pwm.h
 *
 *  Created on: Sep 23, 2020
 *      Author: rob
 */

#ifndef USERLIB_INCLUDE_MYPWM_H_
#define USERLIB_INCLUDE_MYPWM_H_

extern void mypwmInit(void);
extern void cmd_change_freq(BaseSequentialStream *chp, int argc, char *argv[]);
extern void cmd_change_pw4(BaseSequentialStream *chp, int argc, char *argv[]);


#endif /* USERLIB_INCLUDE_MYPWM_H_ */
